Glen-collab/polly-connect/flash_future_polly.docx

Step 1: Create the device in the admin portal

1. Log in as admin at https://polly-connect.com

2. Go to Settings → Devices → Add Device

3. Name it (e.g. "Grandma's Polly")

4. Write down the 6-digit claim code — that's all you need

Step 2: Build the firmware (one time only)

In your ESP-IDF CMD terminal:

cd C:\Users\big_g\Desktop\polly-connect\firmware\polly-waveshare-s3

idf.py build

You only need to build once. Same binary for every device.

Step 3: Flash the device

Plug in the new device, check Device Manager for the COM port, then:

idf.py -p COM5 flash

(Use whatever COM port it shows up on)

Step 4: Give customer the claim code + instructions

Tell them:

1. Go to polly-connect.com → Register

2. Plug in Polly → connect to "Polly-Setup" WiFi on your phone

3. Enter the 6-digit claim code + your home WiFi credentials → hit Connect

4. Go to Settings → Devices on the website → enter the same claim code

5. Done — Polly is yours
