Glen-collab/polly-connect/server/core/database.py

"""
Database module for Polly Connect
"""

import hashlib
import json
import sqlite3
import re
import secrets
from datetime import datetime, timedelta
from typing import Optional, List, Dict


class PollyDB:
    def __init__(self, db_path: str = "polly.db"):
        self.db_path = db_path
        self._conn = None
        if db_path == ":memory:":
            self._conn = sqlite3.connect(":memory:", check_same_thread=False)
        self._init_db()
        self._run_migrations()

    def _get_connection(self):
        if self._conn:
            return self._conn
        return sqlite3.connect(self.db_path)

    def _init_db(self):
        conn = self._get_connection()
        try:
            # Enable WAL mode for better concurrent access
            conn.execute("PRAGMA journal_mode=WAL")

            # ── Original items table ──
            conn.execute("""
                CREATE TABLE IF NOT EXISTS items (
                    id INTEGER PRIMARY KEY AUTOINCREMENT,
                    item TEXT NOT NULL,
                    item_normalized TEXT NOT NULL,
                    location TEXT NOT NULL,
                    location_normalized TEXT NOT NULL,
                    context TEXT,
                    raw_input TEXT,
                    created_at TIMESTAMP DEFAULT CURRENT_TIMESTAMP,
                    updated_at TIMESTAMP DEFAULT CURRENT_TIMESTAMP
                )
            """)
            conn.execute("CREATE INDEX IF NOT EXISTS idx_item_normalized ON items(item_normalized)")
            conn.execute("CREATE INDEX IF NOT EXISTS idx_location_normalized ON items(location_normalized)")

            # ── Device registration ──
            conn.execute("""
                CREATE TABLE IF NOT EXISTS devices (
                    id INTEGER PRIMARY KEY AUTOINCREMENT,
                    device_id TEXT UNIQUE NOT NULL,
                    api_key TEXT,
                    name TEXT,
                    user_id INTEGER REFERENCES user_profiles(id),
                    registered_at TIMESTAMP DEFAULT CURRENT_TIMESTAMP,
                    last_seen TIMESTAMP
                )
            """)

            # ── User profiles ──
            conn.execute("""
                CREATE TABLE IF NOT EXISTS user_profiles (
                    id INTEGER PRIMARY KEY AUTOINCREMENT,
                    name TEXT NOT NULL,
                    familiar_name TEXT,
                    subscription_tier TEXT DEFAULT 'basic',
                    bible_topic_preference TEXT,
                    music_genre_preference TEXT,
                    memory_care_mode INTEGER DEFAULT 0,
                    created_at TIMESTAMP DEFAULT CURRENT_TIMESTAMP,
                    updated_at TIMESTAMP DEFAULT CURRENT_TIMESTAMP
                )
            """)

            # ── Question sessions (Q&A tracking) ──
            conn.execute("""
                CREATE TABLE IF NOT EXISTS question_sessions (
                    id INTEGER PRIMARY KEY AUTOINCREMENT,
                    user_id INTEGER REFERENCES user_profiles(id),
                    question_id TEXT NOT NULL,
                    question_text TEXT NOT NULL,
                    answer_text TEXT,
                    audio_s3_key TEXT,
                    week INTEGER,
                    theme TEXT,
                    answered INTEGER DEFAULT 0,
                    created_at TIMESTAMP DEFAULT CURRENT_TIMESTAMP
                )
            """)

            # ── Free-form stories ──
            conn.execute("""
                CREATE TABLE IF NOT EXISTS stories (
                    id INTEGER PRIMARY KEY AUTOINCREMENT,
                    user_id INTEGER REFERENCES user_profiles(id),
                    transcript TEXT,
                    audio_s3_key TEXT,
                    speaker_name TEXT,
                    chapter TEXT,
                    source TEXT DEFAULT 'voice',
                    duration_seconds REAL,
                    created_at TIMESTAMP DEFAULT CURRENT_TIMESTAMP
                )
            """)

            # ── Medication schedules ──
            conn.execute("""
                CREATE TABLE IF NOT EXISTS medications (
                    id INTEGER PRIMARY KEY AUTOINCREMENT,
                    user_id INTEGER REFERENCES user_profiles(id),
                    name TEXT NOT NULL,
                    dosage TEXT,
                    times TEXT NOT NULL,
                    active_days TEXT DEFAULT '["mon","tue","wed","thu","fri","sat","sun"]',
                    active INTEGER DEFAULT 1,
                    created_at TIMESTAMP DEFAULT CURRENT_TIMESTAMP
                )
            """)

            # ── Medication compliance logs ──
            conn.execute("""
                CREATE TABLE IF NOT EXISTS medication_logs (
                    id INTEGER PRIMARY KEY AUTOINCREMENT,
                    medication_id INTEGER REFERENCES medications(id),
                    status TEXT NOT NULL,
                    reminder_count INTEGER DEFAULT 0,
                    scheduled_time TEXT,
                    responded_at TIMESTAMP,
                    created_at TIMESTAMP DEFAULT CURRENT_TIMESTAMP
                )
            """)

            # ── Bible verses ──
            conn.execute("""
                CREATE TABLE IF NOT EXISTS bible_verses (
                    id INTEGER PRIMARY KEY AUTOINCREMENT,
                    reference TEXT NOT NULL,
                    text TEXT NOT NULL,
                    reflection TEXT,
                    topic TEXT,
                    day_of_year INTEGER
                )
            """)

            # ── Joke history (prevent repeats) ──
            conn.execute("""
                CREATE TABLE IF NOT EXISTS joke_history (
                    id INTEGER PRIMARY KEY AUTOINCREMENT,
                    user_id INTEGER REFERENCES user_profiles(id),
                    joke_id TEXT NOT NULL,
                    told_at TIMESTAMP DEFAULT CURRENT_TIMESTAMP
                )
            """)

            # ── Almanac weather ──
            conn.execute("""
                CREATE TABLE IF NOT EXISTS almanac_weather (
                    id INTEGER PRIMARY KEY AUTOINCREMENT,
                    year INTEGER NOT NULL,
                    week INTEGER NOT NULL,
                    region TEXT DEFAULT 'general',
                    forecast TEXT NOT NULL,
                    details TEXT
                )
            """)

            # ── Family members ──
            conn.execute("""
                CREATE TABLE IF NOT EXISTS family_members (
                    id INTEGER PRIMARY KEY AUTOINCREMENT,
                    name TEXT NOT NULL,
                    name_normalized TEXT NOT NULL,
                    relationship TEXT,
                    primary_user_id INTEGER REFERENCES user_profiles(id),
                    visit_count INTEGER DEFAULT 1,
                    first_seen TIMESTAMP DEFAULT CURRENT_TIMESTAMP,
                    last_seen TIMESTAMP DEFAULT CURRENT_TIMESTAMP
                )
            """)
            conn.execute("CREATE INDEX IF NOT EXISTS idx_family_name ON family_members(name_normalized)")

            # ── Story tags ──
            conn.execute("""
                CREATE TABLE IF NOT EXISTS story_tags (
                    id INTEGER PRIMARY KEY AUTOINCREMENT,
                    story_id INTEGER REFERENCES stories(id),
                    tag_type TEXT NOT NULL,
                    tag_value TEXT NOT NULL
                )
            """)
            conn.execute("CREATE INDEX IF NOT EXISTS idx_story_tags ON story_tags(story_id)")

            # ── Structured memories (narrative-enriched) ──
            conn.execute("""
                CREATE TABLE IF NOT EXISTS memories (
                    id INTEGER PRIMARY KEY AUTOINCREMENT,
                    story_id INTEGER REFERENCES stories(id),
                    speaker TEXT,
                    bucket TEXT DEFAULT 'ordinary_world',
                    life_phase TEXT DEFAULT 'unknown',
                    text_summary TEXT,
                    text TEXT,
                    people TEXT DEFAULT '[]',
                    locations TEXT DEFAULT '[]',
                    emotions TEXT DEFAULT '[]',
                    fingerprint TEXT,
                    verification_status TEXT DEFAULT 'unverified',
                    verified_by TEXT,
                    verified_at TIMESTAMP,
                    created_at TIMESTAMP DEFAULT CURRENT_TIMESTAMP
                )
            """)
            conn.execute("CREATE INDEX IF NOT EXISTS idx_memories_speaker ON memories(speaker)")
            conn.execute("CREATE INDEX IF NOT EXISTS idx_memories_bucket ON memories(bucket)")
            conn.execute("CREATE INDEX IF NOT EXISTS idx_memories_verification ON memories(verification_status)")

            # ── Memory verifications (audit trail) ──
            conn.execute("""
                CREATE TABLE IF NOT EXISTS memory_verifications (
                    id INTEGER PRIMARY KEY AUTOINCREMENT,
                    memory_id INTEGER REFERENCES memories(id),
                    verifier_name TEXT NOT NULL,
                    verifier_relationship TEXT,
                    status TEXT NOT NULL,
                    notes TEXT,
                    created_at TIMESTAMP DEFAULT CURRENT_TIMESTAMP
                )
            """)

            # ── Chapter drafts ──
            conn.execute("""
                CREATE TABLE IF NOT EXISTS chapter_drafts (
                    id INTEGER PRIMARY KEY AUTOINCREMENT,
                    chapter_number INTEGER,
                    title TEXT,
                    bucket TEXT,
                    life_phase TEXT,
                    memory_ids TEXT DEFAULT '[]',
                    content TEXT,
                    status TEXT DEFAULT 'draft',
                    created_at TIMESTAMP DEFAULT CURRENT_TIMESTAMP,
                    updated_at TIMESTAMP DEFAULT CURRENT_TIMESTAMP
                )
            """)

            # ── Session tracking ──
            conn.execute("""
                CREATE TABLE IF NOT EXISTS sessions (
                    id INTEGER PRIMARY KEY AUTOINCREMENT,
                    device_id TEXT,
                    user_id INTEGER REFERENCES user_profiles(id),
                    jokes_told INTEGER DEFAULT 0,
                    questions_asked INTEGER DEFAULT 0,
                    stories_recorded INTEGER DEFAULT 0,
                    duration_seconds REAL,
                    started_at TIMESTAMP DEFAULT CURRENT_TIMESTAMP,
                    ended_at TIMESTAMP
                )
            """)

            # ── Photos ──
            conn.execute("""
                CREATE TABLE IF NOT EXISTS photos (
                    id INTEGER PRIMARY KEY AUTOINCREMENT,
                    user_id INTEGER REFERENCES user_profiles(id),
                    filename TEXT NOT NULL,
                    original_name TEXT,
                    caption TEXT,
                    date_taken TEXT,
                    tags TEXT DEFAULT '[]',
                    story_id INTEGER REFERENCES stories(id),
                    uploaded_by TEXT,
                    created_at TIMESTAMP DEFAULT CURRENT_TIMESTAMP
                )
            """)

            # ── Family message board ──
            conn.execute("""
                CREATE TABLE IF NOT EXISTS family_messages (
                    id INTEGER PRIMARY KEY AUTOINCREMENT,
                    tenant_id INTEGER,
                    from_name TEXT NOT NULL,
                    to_name TEXT,
                    message TEXT NOT NULL,
                    created_at TIMESTAMP DEFAULT CURRENT_TIMESTAMP,
                    expires_at TIMESTAMP,
                    read INTEGER DEFAULT 0
                )
            """)
            conn.execute("CREATE INDEX IF NOT EXISTS idx_family_messages_tenant ON family_messages(tenant_id)")

            # ── family_messages migrations ──
            msg_cols = {row[1] for row in conn.execute("PRAGMA table_info(family_messages)").fetchall()}
            if "device_id" not in msg_cols:
                conn.execute("ALTER TABLE family_messages ADD COLUMN device_id TEXT")
            if "audio_filename" not in msg_cols:
                conn.execute("ALTER TABLE family_messages ADD COLUMN audio_filename TEXT")

            # ── Connected families (cross-tenant message board access) ──
            conn.execute("""
                CREATE TABLE IF NOT EXISTS connected_families (
                    id INTEGER PRIMARY KEY AUTOINCREMENT,
                    tenant_id INTEGER NOT NULL,
                    connected_tenant_id INTEGER NOT NULL,
                    connected_tenant_name TEXT NOT NULL,
                    nickname TEXT,
                    status TEXT DEFAULT 'accepted',
                    created_at TIMESTAMP DEFAULT CURRENT_TIMESTAMP,
                    UNIQUE(tenant_id, connected_tenant_id)
                )
            """)
            # Migration: add status column if missing
            cf_cols = {row[1] for row in conn.execute("PRAGMA table_info(connected_families)").fetchall()}
            if "status" not in cf_cols:
                conn.execute("ALTER TABLE connected_families ADD COLUMN status TEXT DEFAULT 'accepted'")
            if "share_tree" not in cf_cols:
                conn.execute("ALTER TABLE connected_families ADD COLUMN share_tree INTEGER DEFAULT 0")
            if "tree_requested" not in cf_cols:
                conn.execute("ALTER TABLE connected_families ADD COLUMN tree_requested INTEGER DEFAULT 0")
            if "last_wall_visit" not in cf_cols:
                conn.execute("ALTER TABLE connected_families ADD COLUMN last_wall_visit TIMESTAMP")

            # ── Shared Wall ──
            conn.execute("""
                CREATE TABLE IF NOT EXISTS shared_wall_items (
                    id INTEGER PRIMARY KEY AUTOINCREMENT,
                    from_tenant_id INTEGER NOT NULL,
                    to_tenant_id INTEGER NOT NULL,
                    content_type TEXT NOT NULL,
                    content_id INTEGER,
                    caption TEXT,
                    created_at TIMESTAMP DEFAULT CURRENT_TIMESTAMP
                )
            """)
            conn.execute("CREATE INDEX IF NOT EXISTS idx_shared_wall_pair ON shared_wall_items(from_tenant_id, to_tenant_id)")

            conn.execute("""
                CREATE TABLE IF NOT EXISTS wall_comments (
                    id INTEGER PRIMARY KEY AUTOINCREMENT,
                    wall_item_id INTEGER NOT NULL,
                    tenant_id INTEGER NOT NULL,
                    tenant_name TEXT,
                    comment TEXT,
                    audio_filename TEXT,
                    created_at TIMESTAMP DEFAULT CURRENT_TIMESTAMP
                )
            """)

            conn.execute("""
                CREATE TABLE IF NOT EXISTS wall_reactions (
                    id INTEGER PRIMARY KEY AUTOINCREMENT,
                    wall_item_id INTEGER NOT NULL,
                    tenant_id INTEGER NOT NULL,
                    reaction TEXT NOT NULL,
                    created_at TIMESTAMP DEFAULT CURRENT_TIMESTAMP,
                    UNIQUE(wall_item_id, tenant_id)
                )
            """)

            # ── Aviary (community feed) tables ──

            conn.execute("""
                CREATE TABLE IF NOT EXISTS aviary_posts (
                    id INTEGER PRIMARY KEY AUTOINCREMENT,
                    tenant_id INTEGER NOT NULL,
                    author_name TEXT NOT NULL,
                    content_type TEXT NOT NULL DEFAULT 'text',
                    content TEXT,
                    photo_filename TEXT,
                    audio_filename TEXT,
                    created_at TIMESTAMP DEFAULT CURRENT_TIMESTAMP
                )
            """)
            conn.execute("CREATE INDEX IF NOT EXISTS idx_aviary_tenant ON aviary_posts(tenant_id)")

            conn.execute("""
                CREATE TABLE IF NOT EXISTS aviary_reactions (
                    id INTEGER PRIMARY KEY AUTOINCREMENT,
                    post_id INTEGER NOT NULL,
                    tenant_id INTEGER NOT NULL,
                    reactor_name TEXT,
                    reaction TEXT NOT NULL,
                    created_at TIMESTAMP DEFAULT CURRENT_TIMESTAMP,
                    UNIQUE(post_id, tenant_id)
                )
            """)

            conn.execute("""
                CREATE TABLE IF NOT EXISTS aviary_comments (
                    id INTEGER PRIMARY KEY AUTOINCREMENT,
                    post_id INTEGER NOT NULL,
                    tenant_id INTEGER NOT NULL,
                    author_name TEXT NOT NULL,
                    comment TEXT,
                    audio_filename TEXT,
                    created_at TIMESTAMP DEFAULT CURRENT_TIMESTAMP
                )
            """)

            # ── Chatter Groups ──

            conn.execute("""
                CREATE TABLE IF NOT EXISTS chatter_groups (
                    id INTEGER PRIMARY KEY AUTOINCREMENT,
                    name TEXT NOT NULL,
                    creator_tenant_id INTEGER NOT NULL,
                    created_at TIMESTAMP DEFAULT CURRENT_TIMESTAMP
                )
            """)

            conn.execute("""
                CREATE TABLE IF NOT EXISTS chatter_group_members (
                    id INTEGER PRIMARY KEY AUTOINCREMENT,
                    group_id INTEGER NOT NULL,
                    tenant_id INTEGER NOT NULL,
                    role TEXT NOT NULL DEFAULT 'member',
                    joined_at TIMESTAMP DEFAULT CURRENT_TIMESTAMP,
                    last_read_at TIMESTAMP DEFAULT '2000-01-01',
                    UNIQUE(group_id, tenant_id),
                    FOREIGN KEY (group_id) REFERENCES chatter_groups(id)
                )
            """)

            # Migration: add group_id to aviary_posts
            ap_cols = {row[1] for row in conn.execute("PRAGMA table_info(aviary_posts)").fetchall()}
            if "group_id" not in ap_cols:
                conn.execute("ALTER TABLE aviary_posts ADD COLUMN group_id INTEGER")
                conn.execute("CREATE INDEX IF NOT EXISTS idx_aviary_group ON aviary_posts(group_id)")

            # ── Multi-tenant tables ──

            conn.execute("""
                CREATE TABLE IF NOT EXISTS tenants (
                    id INTEGER PRIMARY KEY AUTOINCREMENT,
                    name TEXT NOT NULL,
                    created_at TIMESTAMP DEFAULT CURRENT_TIMESTAMP,
                    updated_at TIMESTAMP DEFAULT CURRENT_TIMESTAMP
                )
            """)

            conn.execute("""
                CREATE TABLE IF NOT EXISTS accounts (
                    id INTEGER PRIMARY KEY AUTOINCREMENT,
                    email TEXT UNIQUE NOT NULL,
                    password_hash TEXT NOT NULL,
                    name TEXT NOT NULL,
                    tenant_id INTEGER REFERENCES tenants(id),
                    role TEXT DEFAULT 'caretaker',
                    created_at TIMESTAMP DEFAULT CURRENT_TIMESTAMP,
                    last_login TIMESTAMP
                )
            """)
            conn.execute("CREATE INDEX IF NOT EXISTS idx_accounts_tenant ON accounts(tenant_id)")

            conn.execute("""
                CREATE TABLE IF NOT EXISTS web_sessions (
                    id TEXT PRIMARY KEY,
                    account_id INTEGER REFERENCES accounts(id),
                    tenant_id INTEGER REFERENCES tenants(id),
                    created_at TIMESTAMP DEFAULT CURRENT_TIMESTAMP,
                    expires_at TIMESTAMP,
                    last_active TIMESTAMP DEFAULT CURRENT_TIMESTAMP
                )
            """)
            conn.execute("CREATE INDEX IF NOT EXISTS idx_web_sessions_account ON web_sessions(account_id)")

            # ── Firmware versions (OTA updates) ──
            conn.execute("""
                CREATE TABLE IF NOT EXISTS firmware_versions (
                    id INTEGER PRIMARY KEY AUTOINCREMENT,
                    variant TEXT NOT NULL,
                    version TEXT NOT NULL,
                    filename TEXT NOT NULL,
                    file_size INTEGER,
                    file_hash TEXT,
                    release_notes TEXT,
                    is_active INTEGER DEFAULT 0,
                    uploaded_at TIMESTAMP DEFAULT CURRENT_TIMESTAMP
                )
            """)

            # ── Narrative log (track which stories were read back) ──
            conn.execute("""
                CREATE TABLE IF NOT EXISTS narrative_log (
                    id INTEGER PRIMARY KEY AUTOINCREMENT,
                    tenant_id INTEGER,
                    story_id INTEGER REFERENCES stories(id),
                    query TEXT,
                    created_at TIMESTAMP DEFAULT CURRENT_TIMESTAMP
                )
            """)
            conn.execute("CREATE INDEX IF NOT EXISTS idx_narrative_log_tenant ON narrative_log(tenant_id, created_at)")
            conn.execute("CREATE INDEX IF NOT EXISTS idx_narrative_log_story ON narrative_log(story_id, created_at)")

            # ── Story narratives (cached GPT narratives for replay) ──
            conn.execute("""
                CREATE TABLE IF NOT EXISTS story_narratives (
                    id INTEGER PRIMARY KEY AUTOINCREMENT,
                    tenant_id INTEGER,
                    narrative TEXT NOT NULL,
                    attribution TEXT,
                    story_ids TEXT,
                    query TEXT,
                    status TEXT DEFAULT 'draft',
                    created_at TIMESTAMP DEFAULT CURRENT_TIMESTAMP
                )
            """)

            # ── Device events (admin telemetry) ──
            conn.execute("""
                CREATE TABLE IF NOT EXISTS device_events (
                    id INTEGER PRIMARY KEY AUTOINCREMENT,
                    device_id TEXT NOT NULL,
                    tenant_id INTEGER,
                    event_type TEXT NOT NULL,
                    intent TEXT,
                    success INTEGER DEFAULT 1,
                    detail TEXT,
                    created_at TIMESTAMP DEFAULT CURRENT_TIMESTAMP
                )
            """)
            conn.execute("CREATE INDEX IF NOT EXISTS idx_device_events_device_time ON device_events(device_id, created_at)")
            conn.execute("CREATE INDEX IF NOT EXISTS idx_device_events_type_time ON device_events(event_type, created_at)")

            conn.commit()
        finally:
            if not self._conn:
                conn.close()

    def _run_migrations(self):
        """Add columns to existing tables (safe to run repeatedly)."""
        conn = self._get_connection()
        try:
            # Get existing columns for user_profiles
            cols = {row[1] for row in conn.execute("PRAGMA table_info(user_profiles)").fetchall()}
            migrations = {
                "owner_email": "ALTER TABLE user_profiles ADD COLUMN owner_email TEXT",
                "caretaker_name": "ALTER TABLE user_profiles ADD COLUMN caretaker_name TEXT",
                "caretaker_email": "ALTER TABLE user_profiles ADD COLUMN caretaker_email TEXT",
                "setup_complete": "ALTER TABLE user_profiles ADD COLUMN setup_complete INTEGER DEFAULT 0",
                "squawk_interval": "ALTER TABLE user_profiles ADD COLUMN squawk_interval INTEGER DEFAULT 10",
                "chatter_interval": "ALTER TABLE user_profiles ADD COLUMN chatter_interval INTEGER DEFAULT 45",
                "squawk_snoozed_until": "ALTER TABLE user_profiles ADD COLUMN squawk_snoozed_until TIMESTAMP",
                "quiet_hours_start": "ALTER TABLE user_profiles ADD COLUMN quiet_hours_start INTEGER DEFAULT 21",
                "quiet_hours_end": "ALTER TABLE user_profiles ADD COLUMN quiet_hours_end INTEGER DEFAULT 7",
                "location_city": "ALTER TABLE user_profiles ADD COLUMN location_city TEXT",
                "location_lat": "ALTER TABLE user_profiles ADD COLUMN location_lat REAL",
                "location_lon": "ALTER TABLE user_profiles ADD COLUMN location_lon REAL",
                "squawk_volume": "ALTER TABLE user_profiles ADD COLUMN squawk_volume INTEGER DEFAULT 30",
                "rms_threshold": "ALTER TABLE user_profiles ADD COLUMN rms_threshold INTEGER DEFAULT 200",
                "voice_volume": "ALTER TABLE user_profiles ADD COLUMN voice_volume INTEGER DEFAULT 100",
                "blessing_volume": "ALTER TABLE user_profiles ADD COLUMN blessing_volume INTEGER DEFAULT 80",
                "kid_mode": "ALTER TABLE user_profiles ADD COLUMN kid_mode INTEGER DEFAULT 0",
                "nostalgia_profile": "ALTER TABLE user_profiles ADD COLUMN nostalgia_profile TEXT",
                "hometown": "ALTER TABLE user_profiles ADD COLUMN hometown TEXT",
                "birth_year": "ALTER TABLE user_profiles ADD COLUMN birth_year INTEGER",
                "squawk_quiet_override": "ALTER TABLE user_profiles ADD COLUMN squawk_quiet_override INTEGER DEFAULT 0",
                "book_page_count": "ALTER TABLE user_profiles ADD COLUMN book_page_count INTEGER",
                "book_cover_config": "ALTER TABLE user_profiles ADD COLUMN book_cover_config TEXT",
                "last_aviary_visit": "ALTER TABLE user_profiles ADD COLUMN last_aviary_visit TIMESTAMP",
            }
            for col, sql in migrations.items():
                if col not in cols:
                    conn.execute(sql)

            # Get existing columns for stories
            cols = {row[1] for row in conn.execute("PRAGMA table_info(stories)").fetchall()}
            migrations = {
                "verified": "ALTER TABLE stories ADD COLUMN verified INTEGER DEFAULT 0",
                "verified_by": "ALTER TABLE stories ADD COLUMN verified_by TEXT",
                "verified_at": "ALTER TABLE stories ADD COLUMN verified_at TIMESTAMP",
                "corrected_transcript": "ALTER TABLE stories ADD COLUMN corrected_transcript TEXT",
                "question_text": "ALTER TABLE stories ADD COLUMN question_text TEXT",
                "photo_id": "ALTER TABLE stories ADD COLUMN photo_id INTEGER REFERENCES photos(id)",
                "qr_in_book": "ALTER TABLE stories ADD COLUMN qr_in_book INTEGER DEFAULT 1",
                "photo_in_book": "ALTER TABLE stories ADD COLUMN photo_in_book INTEGER DEFAULT 1",
                "private": "ALTER TABLE stories ADD COLUMN private INTEGER DEFAULT 0",
            }
            for col, sql in migrations.items():
                if col not in cols:
                    conn.execute(sql)

            # ── Multi-tenant migrations: add tenant_id to all data tables ──
            tenant_tables = [
                "items", "stories", "question_sessions", "medications",
                "medication_logs", "joke_history", "family_members", "memories",
                "memory_verifications", "chapter_drafts", "sessions", "photos",
                "story_tags", "user_profiles", "devices", "family_messages",
            ]
            for table in tenant_tables:
                cols = {row[1] for row in conn.execute(f"PRAGMA table_info({table})").fetchall()}
                if "tenant_id" not in cols:
                    conn.execute(f"ALTER TABLE {table} ADD COLUMN tenant_id INTEGER")

            # Add in_book to photos
            cols = {row[1] for row in conn.execute("PRAGMA table_info(photos)").fetchall()}
            if "in_book" not in cols:
                conn.execute("ALTER TABLE photos ADD COLUMN in_book INTEGER DEFAULT 1")
            if "wall_only" not in cols:
                conn.execute("ALTER TABLE photos ADD COLUMN wall_only INTEGER DEFAULT 0")

            # Add is_admin and terms_accepted_at to accounts
            cols = {row[1] for row in conn.execute("PRAGMA table_info(accounts)").fetchall()}
            if "is_admin" not in cols:
                conn.execute("ALTER TABLE accounts ADD COLUMN is_admin INTEGER DEFAULT 0")
                # First account is always admin (manufacturer)
                conn.execute("UPDATE accounts SET is_admin = 1 WHERE id = 1")
            if "terms_accepted_at" not in cols:
                conn.execute("ALTER TABLE accounts ADD COLUMN terms_accepted_at TIMESTAMP")

            # Add api_key_hash and firmware info to devices
            cols = {row[1] for row in conn.execute("PRAGMA table_info(devices)").fetchall()}
            if "api_key_hash" not in cols:
                conn.execute("ALTER TABLE devices ADD COLUMN api_key_hash TEXT")
            if "fw_version" not in cols:
                conn.execute("ALTER TABLE devices ADD COLUMN fw_version TEXT")
            if "fw_variant" not in cols:
                conn.execute("ALTER TABLE devices ADD COLUMN fw_variant TEXT")
            if "claim_code" not in cols:
                conn.execute("ALTER TABLE devices ADD COLUMN claim_code TEXT")
            if "claimed_at" not in cols:
                conn.execute("ALTER TABLE devices ADD COLUMN claimed_at TIMESTAMP")

            # Per-device settings (NULL = inherit from tenant user_profiles)
            device_settings_migrations = {
                "dev_quiet_hours_start": "ALTER TABLE devices ADD COLUMN dev_quiet_hours_start INTEGER",
                "dev_quiet_hours_end": "ALTER TABLE devices ADD COLUMN dev_quiet_hours_end INTEGER",
                "dev_squawk_interval": "ALTER TABLE devices ADD COLUMN dev_squawk_interval INTEGER",
                "dev_chatter_interval": "ALTER TABLE devices ADD COLUMN dev_chatter_interval INTEGER",
                "dev_squawk_volume": "ALTER TABLE devices ADD COLUMN dev_squawk_volume INTEGER",
                "dev_snoozed_until": "ALTER TABLE devices ADD COLUMN dev_snoozed_until TIMESTAMP",
                "dev_quiet_override": "ALTER TABLE devices ADD COLUMN dev_quiet_override INTEGER",
                "dev_message_nag": "ALTER TABLE devices ADD COLUMN dev_message_nag INTEGER",
                "dev_kid_mode": "ALTER TABLE devices ADD COLUMN dev_kid_mode INTEGER",
            }
            for col, sql in device_settings_migrations.items():
                if col not in cols:
                    conn.execute(sql)

            # Create default tenant #1 and backfill
            conn.execute("INSERT OR IGNORE INTO tenants (id, name) VALUES (1, 'Default')")
            for table in tenant_tables:
                conn.execute(f"UPDATE {table} SET tenant_id = 1 WHERE tenant_id IS NULL")

            # ── Family access code migrations ──
            # Add family_code columns to tenants
            cols = {row[1] for row in conn.execute("PRAGMA table_info(tenants)").fetchall()}
            if "family_code" not in cols:
                conn.execute("ALTER TABLE tenants ADD COLUMN family_code TEXT")
            if "family_code_created_at" not in cols:
                conn.execute("ALTER TABLE tenants ADD COLUMN family_code_created_at TIMESTAMP")

            # ── Medications device_id column ──
            cols = {row[1] for row in conn.execute("PRAGMA table_info(medications)").fetchall()}
            if "device_id" not in cols:
                conn.execute("ALTER TABLE medications ADD COLUMN device_id TEXT")

            # ── Items prep column ──
            cols = {row[1] for row in conn.execute("PRAGMA table_info(items)").fetchall()}
            if "prep" not in cols:
                conn.execute("ALTER TABLE items ADD COLUMN prep TEXT DEFAULT 'on'")

            # ── Family tree migrations ──
            cols = {row[1] for row in conn.execute("PRAGMA table_info(family_members)").fetchall()}
            fm_migrations = {
                "parent_member_id": "ALTER TABLE family_members ADD COLUMN parent_member_id INTEGER REFERENCES family_members(id)",
                "relation_to_owner": "ALTER TABLE family_members ADD COLUMN relation_to_owner TEXT",
                "generation": "ALTER TABLE family_members ADD COLUMN generation INTEGER DEFAULT 0",
            }
            for col, sql in fm_migrations.items():
                if col not in cols:
                    conn.execute(sql)

            # Add extended info to family_members
            cols = {row[1] for row in conn.execute("PRAGMA table_info(family_members)").fetchall()}
            fm_ext = {
                "deceased": "ALTER TABLE family_members ADD COLUMN deceased INTEGER DEFAULT 0",
                "spouse_name": "ALTER TABLE family_members ADD COLUMN spouse_name TEXT",
                "bio": "ALTER TABLE family_members ADD COLUMN bio TEXT",
                "added_by": "ALTER TABLE family_members ADD COLUMN added_by TEXT",
                "birth_year": "ALTER TABLE family_members ADD COLUMN birth_year INTEGER",
                "deceased_year": "ALTER TABLE family_members ADD COLUMN deceased_year INTEGER",
                "access_code": "ALTER TABLE family_members ADD COLUMN access_code TEXT",
                "code_created_at": "ALTER TABLE family_members ADD COLUMN code_created_at TIMESTAMP",
                "is_minor": "ALTER TABLE family_members ADD COLUMN is_minor INTEGER DEFAULT 0",
                "email": "ALTER TABLE family_members ADD COLUMN email TEXT",
            }
            for col, sql in fm_ext.items():
                if col not in cols:
                    conn.execute(sql)

            # Add family_member_id + onboarding columns to web_sessions
            cols = {row[1] for row in conn.execute("PRAGMA table_info(web_sessions)").fetchall()}
            ws_migrations = {
                "family_member_id": "ALTER TABLE web_sessions ADD COLUMN family_member_id INTEGER",
                "onboarding_complete": "ALTER TABLE web_sessions ADD COLUMN onboarding_complete INTEGER DEFAULT 0",
                "invitation_id": "ALTER TABLE web_sessions ADD COLUMN invitation_id INTEGER",
                "last_onboarding_step": "ALTER TABLE web_sessions ADD COLUMN last_onboarding_step INTEGER DEFAULT 1",
            }
            for col, sql in ws_migrations.items():
                if col not in cols:
                    conn.execute(sql)

            # Family invitations table
            conn.execute("""
                CREATE TABLE IF NOT EXISTS family_invitations (
                    id INTEGER PRIMARY KEY AUTOINCREMENT,
                    tenant_id INTEGER NOT NULL,
                    family_member_id INTEGER,
                    inviter_name TEXT NOT NULL,
                    invitee_name TEXT NOT NULL,
                    invitee_email TEXT NOT NULL,
                    voice_message_filename TEXT,
                    family_code TEXT NOT NULL,
                    status TEXT DEFAULT 'sent',
                    sent_at TIMESTAMP DEFAULT CURRENT_TIMESTAMP,
                    visited_at TIMESTAMP,
                    onboarded_at TIMESTAMP,
                    converted_at TIMESTAMP,
                    converted_tenant_id INTEGER,
                    feedback_rating INTEGER,
                    feedback_note TEXT
                )
            """)

            # Add timeline columns to memories
            cols = {row[1] for row in conn.execute("PRAGMA table_info(memories)").fetchall()}
            mem_migrations = {
                "estimated_year": "ALTER TABLE memories ADD COLUMN estimated_year INTEGER",
                "owner_age": "ALTER TABLE memories ADD COLUMN owner_age INTEGER",
                "year_confidence": "ALTER TABLE memories ADD COLUMN year_confidence TEXT DEFAULT 'none'",
                # ── Legacy Funnel: every surface (story/photo/chatter/wall) feeds memories ──
                "source": "ALTER TABLE memories ADD COLUMN source TEXT DEFAULT 'story'",
                "source_ref": "ALTER TABLE memories ADD COLUMN source_ref INTEGER",
                "include_in_book": "ALTER TABLE memories ADD COLUMN include_in_book INTEGER DEFAULT 1",
                "is_quote": "ALTER TABLE memories ADD COLUMN is_quote INTEGER DEFAULT 0",
                "story_value": "ALTER TABLE memories ADD COLUMN story_value REAL",
                # The owner dated or moved this story themselves: the AI
                # sorter never overrides their placement
                "placed_by_user": "ALTER TABLE memories ADD COLUMN placed_by_user INTEGER DEFAULT 0",
                # "Move to this chapter": pinned to a written chapter's draft
                "pinned_draft_id": "ALTER TABLE memories ADD COLUMN pinned_draft_id INTEGER",
            }
            for col, sql in mem_migrations.items():
                if col not in cols:
                    conn.execute(sql)

            # Add chapter continuity columns to chapter_drafts
            cols = {row[1] for row in conn.execute("PRAGMA table_info(chapter_drafts)").fetchall()}
            cd_migrations = {
                "summary": "ALTER TABLE chapter_drafts ADD COLUMN summary TEXT",
                "needs_refresh": "ALTER TABLE chapter_drafts ADD COLUMN needs_refresh INTEGER DEFAULT 0",
                # Memories the coverage check found absent from the prose —
                # the PDF prints these verbatim after the chapter.
                "missing_memory_ids": "ALTER TABLE chapter_drafts ADD COLUMN missing_memory_ids TEXT DEFAULT '[]'",
                # Owner edited the prose by hand: never auto-rewrite it
                "hand_edited": "ALTER TABLE chapter_drafts ADD COLUMN hand_edited INTEGER DEFAULT 0",
                # The version a rewrite replaced, so a rewrite is never a loss
                "previous_content": "ALTER TABLE chapter_drafts ADD COLUMN previous_content TEXT",
                # {memory_id: "bucket/life_phase"} when the chapter was written;
                # a story whose placement changes since then moves out
                "placements": "ALTER TABLE chapter_drafts ADD COLUMN placements TEXT",
            }
            for col, sql in cd_migrations.items():
                if col not in cols:
                    conn.execute(sql)
                    if col == "hand_edited":
                        # Drafts saved after generation were edited by hand
                        conn.execute("UPDATE chapter_drafts SET hand_edited = 1 "
                                     "WHERE updated_at IS NOT NULL AND updated_at > created_at")

            # Prayer requests table
            conn.execute("""
                CREATE TABLE IF NOT EXISTS prayer_requests (
                    id INTEGER PRIMARY KEY AUTOINCREMENT,
                    tenant_id INTEGER,
                    name TEXT NOT NULL,
                    request TEXT,
                    active INTEGER DEFAULT 1,
                    created_at TIMESTAMP DEFAULT CURRENT_TIMESTAMP
                )
            """)

            # Pronunciation guide table
            conn.execute("""
                CREATE TABLE IF NOT EXISTS pronunciations (
                    id INTEGER PRIMARY KEY AUTOINCREMENT,
                    tenant_id INTEGER,
                    word TEXT NOT NULL,
                    phonetic TEXT NOT NULL,
                    created_at TIMESTAMP DEFAULT CURRENT_TIMESTAMP
                )
            """)

            # Nostalgia snippets table
            conn.execute("""
                CREATE TABLE IF NOT EXISTS nostalgia_snippets (
                    id INTEGER PRIMARY KEY AUTOINCREMENT,
                    tenant_id INTEGER,
                    category TEXT NOT NULL,
                    variation_number INTEGER NOT NULL,
                    text TEXT NOT NULL,
                    last_used TIMESTAMP,
                    created_at TIMESTAMP DEFAULT CURRENT_TIMESTAMP
                )
            """)
            conn.execute("CREATE INDEX IF NOT EXISTS idx_nostalgia_tenant ON nostalgia_snippets(tenant_id)")

            # Add original_text to nostalgia_snippets for tracking edits
            cols = {row[1] for row in conn.execute("PRAGMA table_info(nostalgia_snippets)").fetchall()}
            if "original_text" not in cols:
                conn.execute("ALTER TABLE nostalgia_snippets ADD COLUMN original_text TEXT")

            # Deleted nostalgia snippets log (so GPT avoids these topics)
            conn.execute("""
                CREATE TABLE IF NOT EXISTS nostalgia_deleted (
                    id INTEGER PRIMARY KEY AUTOINCREMENT,
                    tenant_id INTEGER,
                    category TEXT,
                    text TEXT NOT NULL,
                    deleted_at TIMESTAMP DEFAULT CURRENT_TIMESTAMP
                )
            """)

            # Song briefs table (chapter-to-song pipeline)
            conn.execute("""
                CREATE TABLE IF NOT EXISTS song_briefs (
                    id INTEGER PRIMARY KEY AUTOINCREMENT,
                    tenant_id INTEGER,
                    chapter_number INTEGER,
                    chapter_title TEXT,
                    song_title TEXT,
                    genre TEXT,
                    jungian_stage TEXT,
                    lyrics_json TEXT,
                    style_prompt TEXT,
                    essence_json TEXT,
                    audio_filename TEXT,
                    created_at TIMESTAMP DEFAULT CURRENT_TIMESTAMP
                )
            """)

            # Prayer recordings table (voice prayers, blessings, grace)
            conn.execute("""
                CREATE TABLE IF NOT EXISTS prayer_recordings (
                    id INTEGER PRIMARY KEY AUTOINCREMENT,
                    tenant_id INTEGER,
                    speaker_name TEXT,
                    category TEXT NOT NULL DEFAULT 'general',
                    title TEXT,
                    audio_filename TEXT NOT NULL,
                    transcript TEXT,
                    schedule_time TEXT,
                    schedule_days TEXT DEFAULT '0,1,2,3,4,5,6',
                    active INTEGER DEFAULT 1,
                    play_count INTEGER DEFAULT 0,
                    last_played TIMESTAMP,
                    created_at TIMESTAMP DEFAULT CURRENT_TIMESTAMP
                )
            """)

            # Add family_name and role columns to web_sessions
            cols = {row[1] for row in conn.execute("PRAGMA table_info(web_sessions)").fetchall()}
            if "family_name" not in cols:
                conn.execute("ALTER TABLE web_sessions ADD COLUMN family_name TEXT")
            if "role" not in cols:
                conn.execute("ALTER TABLE web_sessions ADD COLUMN role TEXT")

            # ── Subscription / Stripe migrations ──
            cols = {row[1] for row in conn.execute("PRAGMA table_info(tenants)").fetchall()}
            sub_migrations = {
                "subscription_tier": "ALTER TABLE tenants ADD COLUMN subscription_tier TEXT DEFAULT 'trial'",
                "subscription_status": "ALTER TABLE tenants ADD COLUMN subscription_status TEXT DEFAULT 'active'",
                "stripe_customer_id": "ALTER TABLE tenants ADD COLUMN stripe_customer_id TEXT",
                "stripe_subscription_id": "ALTER TABLE tenants ADD COLUMN stripe_subscription_id TEXT",
                "trial_ends_at": "ALTER TABLE tenants ADD COLUMN trial_ends_at TIMESTAMP",
                # One-time "Buy the Book" unlock (separate from monthly tier)
                "book_purchased": "ALTER TABLE tenants ADD COLUMN book_purchased INTEGER DEFAULT 0",
            }
            for col, sql in sub_migrations.items():
                if col not in cols:
                    conn.execute(sql)

            # Set trial_ends_at for existing tenants that don't have it yet
            # (30 days from now for existing users, generous grace period)
            conn.execute("""
                UPDATE tenants SET trial_ends_at = datetime('now', '+30 days')
                WHERE trial_ends_at IS NULL AND subscription_tier IS NULL AND id > 1
            """)
            # Tenant 1 (admin) gets legacy tier
            conn.execute("""
                UPDATE tenants SET subscription_tier = 'legacy', subscription_status = 'active'
                WHERE id = 1 AND (subscription_tier IS NULL OR subscription_tier = 'trial')
            """)

            # Photo index table (Memory module — photo-based item indexing)
            conn.execute("""
                CREATE TABLE IF NOT EXISTS photo_indexes (
                    id INTEGER PRIMARY KEY AUTOINCREMENT,
                    tenant_id INTEGER,
                    filename TEXT NOT NULL,
                    location TEXT NOT NULL,
                    description TEXT,
                    item_count INTEGER DEFAULT 0,
                    created_at TIMESTAMP DEFAULT CURRENT_TIMESTAMP
                )
            """)

            # Add recorded_by_member_id to stories (tracks which family member recorded)
            story_cols = {row[1] for row in conn.execute("PRAGMA table_info(stories)").fetchall()}
            if "recorded_by_member_id" not in story_cols:
                conn.execute("ALTER TABLE stories ADD COLUMN recorded_by_member_id INTEGER")

            # Security questions for code recovery
            conn.execute("""
                CREATE TABLE IF NOT EXISTS security_questions (
                    id INTEGER PRIMARY KEY AUTOINCREMENT,
                    tenant_id INTEGER NOT NULL,
                    question TEXT NOT NULL,
                    answer_hash TEXT NOT NULL,
                    created_at TIMESTAMP DEFAULT CURRENT_TIMESTAMP
                )
            """)

            conn.commit()
        finally:
            if not self._conn:
                conn.close()

    @staticmethod
    def _normalize(text: str) -> str:
        if not text:
            return ""
        text = text.lower().strip()
        text = re.sub(r'\b(the|a|an|my|that|this)\b', '', text)
        text = re.sub(r'\s+', ' ', text).strip()
        return text

    # ── Tenant management ──

    def create_tenant(self, name: str) -> int:
        conn = self._get_connection()
        try:
            cursor = conn.execute(
                "INSERT INTO tenants (name) VALUES (?)", (name,)
            )
            conn.commit()
            return cursor.lastrowid
        finally:
            if not self._conn:
                conn.close()

    def get_tenant(self, tenant_id: int) -> Optional[Dict]:
        conn = self._get_connection()
        try:
            conn.row_factory = sqlite3.Row
            result = conn.execute(
                "SELECT * FROM tenants WHERE id = ?", (tenant_id,)
            ).fetchone()
            return dict(result) if result else None
        finally:
            if not self._conn:
                conn.close()

    def get_all_tenants(self) -> List[Dict]:
        conn = self._get_connection()
        try:
            conn.row_factory = sqlite3.Row
            results = conn.execute("SELECT * FROM tenants ORDER BY name").fetchall()
            return [dict(r) for r in results]
        finally:
            if not self._conn:
                conn.close()

    def delete_tenant(self, tenant_id: int) -> Dict[str, int]:
        """ADMIN: permanently delete a tenant and all of its data. Sweeps every
        table that has a tenant_id column, then removes the tenant row itself.
        Returns {table: rows_deleted}."""
        conn = self._get_connection()
        try:
            tables = [r[0] for r in conn.execute(
                "SELECT name FROM sqlite_master WHERE type='table'").fetchall()]
            deleted = {}
            for t in tables:
                if t == "tenants":
                    continue
                cols = [c[1] for c in conn.execute(f"PRAGMA table_info({t})").fetchall()]
                if "tenant_id" in cols:
                    cur = conn.execute(f"DELETE FROM {t} WHERE tenant_id = ?", (tenant_id,))
                    if cur.rowcount:
                        deleted[t] = cur.rowcount
            cur = conn.execute("DELETE FROM tenants WHERE id = ?", (tenant_id,))
            deleted["tenants"] = cur.rowcount
            conn.commit()
            return deleted
        finally:
            if not self._conn:
                conn.close()

    def set_tenant_subscription(self, tenant_id: int, tier: str, status: str = "active"):
        """ADMIN: set a tenant's subscription tier + status (trial|basic|legacy)."""
        conn = self._get_connection()
        try:
            conn.execute(
                "UPDATE tenants SET subscription_tier = ?, subscription_status = ? WHERE id = ?",
                (tier, status, tenant_id))
            conn.commit()
        finally:
            if not self._conn:
                conn.close()

    def is_book_purchased(self, tenant_id: int) -> bool:
        """True if this tenant bought the one-time Legacy Book unlock."""
        conn = self._get_connection()
        try:
            row = conn.execute(
                "SELECT book_purchased FROM tenants WHERE id = ?", (tenant_id,)
            ).fetchone()
            return bool(row and row[0])
        finally:
            if not self._conn:
                conn.close()

    def set_book_purchased(self, tenant_id: int, purchased: bool = True):
        """Mark the one-time Legacy Book unlock for a tenant."""
        conn = self._get_connection()
        try:
            conn.execute("UPDATE tenants SET book_purchased = ? WHERE id = ?",
                         (1 if purchased else 0, tenant_id))
            conn.commit()
        finally:
            if not self._conn:
                conn.close()

    # ── Connected families (cross-tenant) ──

    def send_friend_request(self, tenant_id: int, target_family_code: str) -> Optional[Dict]:
        """Connect to another family by code. Sender is instantly connected.
        Target gets a pending request they must accept."""
        conn = self._get_connection()
        try:
            conn.row_factory = sqlite3.Row
            target = conn.execute(
                "SELECT * FROM tenants WHERE family_code = ?", (target_family_code,)
            ).fetchone()
            if not target:
                return None
            target_tid = target["id"]
            if target_tid == tenant_id:
                return None  # Can't connect to yourself

            # Check if already connected or pending in either direction
            existing = conn.execute(
                "SELECT 1 FROM connected_families WHERE "
                "(tenant_id = ? AND connected_tenant_id = ?) OR "
                "(tenant_id = ? AND connected_tenant_id = ?)",
                (tenant_id, target_tid, target_tid, tenant_id)
            ).fetchone()
            if existing:
                return None

            # Get both tenant names
            my_tenant = conn.execute("SELECT name FROM tenants WHERE id = ?", (tenant_id,)).fetchone()
            my_name = my_tenant["name"] if my_tenant else "Unknown"
            target_name = target["name"]

            # Sender side: instantly accepted, tree shared, wall visit set to now
            conn.execute(
                "INSERT INTO connected_families (tenant_id, connected_tenant_id, connected_tenant_name, status, share_tree, last_wall_visit) VALUES (?, ?, ?, 'accepted', 1, datetime('now'))",
                (tenant_id, target_tid, target_name))
            # Target side: pending, tree pre-shared, wall visit set to now
            conn.execute(
                "INSERT INTO connected_families (tenant_id, connected_tenant_id, connected_tenant_name, status, share_tree, last_wall_visit) VALUES (?, ?, ?, 'pending', 1, datetime('now'))",
                (target_tid, tenant_id, my_name))
            conn.commit()
            return {"connected_tenant_id": target_tid, "connected_tenant_name": target_name}
        finally:
            if not self._conn:
                conn.close()

    def send_friend_request_by_tenant(self, tenant_id: int, target_tenant_id: int) -> Optional[Dict]:
        """Connect to another family by tenant ID (email-based discovery).
        Same as send_friend_request but skips code lookup."""
        conn = self._get_connection()
        try:
            conn.row_factory = sqlite3.Row
            if target_tenant_id == tenant_id:
                return None

            existing = conn.execute(
                "SELECT 1 FROM connected_families WHERE "
                "(tenant_id = ? AND connected_tenant_id = ?) OR "
                "(tenant_id = ? AND connected_tenant_id = ?)",
                (tenant_id, target_tenant_id, target_tenant_id, tenant_id)
            ).fetchone()
            if existing:
                return None

            my_tenant = conn.execute("SELECT name FROM tenants WHERE id = ?", (tenant_id,)).fetchone()
            target_tenant = conn.execute("SELECT name FROM tenants WHERE id = ?", (target_tenant_id,)).fetchone()
            if not target_tenant:
                return None
            my_name = my_tenant["name"] if my_tenant else "Unknown"
            target_name = target_tenant["name"]

            # Sender side: instantly accepted, tree shared, wall visit set to now
            conn.execute(
                "INSERT INTO connected_families (tenant_id, connected_tenant_id, connected_tenant_name, status, share_tree, last_wall_visit) VALUES (?, ?, ?, 'accepted', 1, datetime('now'))",
                (tenant_id, target_tenant_id, target_name))
            # Target side: pending (they need to accept), tree pre-shared, wall visit set to now
            conn.execute(
                "INSERT INTO connected_families (tenant_id, connected_tenant_id, connected_tenant_name, status, share_tree, last_wall_visit) VALUES (?, ?, ?, 'pending', 1, datetime('now'))",
                (target_tenant_id, tenant_id, my_name))
            conn.commit()
            return {"connected_tenant_id": target_tenant_id, "connected_tenant_name": target_name}
        finally:
            if not self._conn:
                conn.close()

    def accept_friend_request(self, tenant_id: int, requester_tenant_id: int) -> bool:
        """Accept a pending friend request. Updates to accepted and adds sender to accepter's family tree."""
        conn = self._get_connection()
        try:
            conn.row_factory = sqlite3.Row
            # Find the pending request
            pending = conn.execute(
                "SELECT * FROM connected_families WHERE tenant_id = ? AND connected_tenant_id = ? AND status = 'pending'",
                (tenant_id, requester_tenant_id)
            ).fetchone()
            if not pending:
                return False

            # Update to accepted and auto-share trees both ways
            conn.execute(
                "UPDATE connected_families SET status = 'accepted', share_tree = 1 WHERE id = ?",
                (pending["id"],))
            # Also share on the other side
            conn.execute(
                "UPDATE connected_families SET share_tree = 1 WHERE tenant_id = ? AND connected_tenant_id = ? AND status = 'accepted'",
                (requester_tenant_id, tenant_id))

            # Get the requester's owner name to add to accepter's family tree
            requester_user = conn.execute(
                "SELECT name FROM user_profiles WHERE tenant_id = ? LIMIT 1",
                (requester_tenant_id,)
            ).fetchone()
            requester_name = requester_user["name"] if requester_user else pending["connected_tenant_name"]

            # Add requester to accepter's family tree as "Friend" (if not already there)
            existing_member = conn.execute(
                "SELECT 1 FROM family_members WHERE LOWER(name) = ? AND tenant_id = ?",
                (requester_name.lower(), tenant_id)
            ).fetchone()
            if not existing_member:
                name_norm = requester_name.lower().strip()
                conn.execute("""
                    INSERT INTO family_members (name, name_normalized, relationship, relation_to_owner,
                    generation, tenant_id, added_by)
                    VALUES (?, ?, 'friend', 'friend', 0, ?, 'Polly Connect')
                """, (requester_name, name_norm, tenant_id))

            conn.commit()
            return True
        finally:
            if not self._conn:
                conn.close()

    def decline_friend_request(self, tenant_id: int, requester_tenant_id: int):
        """Decline a friend request. Removes both directions."""
        conn = self._get_connection()
        try:
            # Remove both directions
            conn.execute(
                "DELETE FROM connected_families WHERE tenant_id = ? AND connected_tenant_id = ?",
                (tenant_id, requester_tenant_id))
            conn.execute(
                "DELETE FROM connected_families WHERE tenant_id = ? AND connected_tenant_id = ?",
                (requester_tenant_id, tenant_id))
            conn.commit()
        finally:
            if not self._conn:
                conn.close()

    def disconnect_family(self, tenant_id: int, connected_tenant_id: int):
        """Remove a family connection (both directions)."""
        conn = self._get_connection()
        try:
            conn.execute(
                "DELETE FROM connected_families WHERE tenant_id = ? AND connected_tenant_id = ?",
                (tenant_id, connected_tenant_id))
            conn.execute(
                "DELETE FROM connected_families WHERE tenant_id = ? AND connected_tenant_id = ?",
                (connected_tenant_id, tenant_id))
            conn.commit()
        finally:
            if not self._conn:
                conn.close()

    def get_connected_families(self, tenant_id: int) -> List[Dict]:
        """Get accepted connections for this tenant."""
        conn = self._get_connection()
        try:
            conn.row_factory = sqlite3.Row
            results = conn.execute(
                "SELECT * FROM connected_families WHERE tenant_id = ? AND status = 'accepted' ORDER BY connected_tenant_name",
                (tenant_id,)
            ).fetchall()
            return [dict(r) for r in results]
        finally:
            if not self._conn:
                conn.close()

    def get_pending_friend_requests(self, tenant_id: int) -> List[Dict]:
        """Get pending friend requests sent TO this tenant."""
        conn = self._get_connection()
        try:
            conn.row_factory = sqlite3.Row
            results = conn.execute(
                "SELECT * FROM connected_families WHERE tenant_id = ? AND status = 'pending' ORDER BY created_at DESC",
                (tenant_id,)
            ).fetchall()
            return [dict(r) for r in results]
        finally:
            if not self._conn:
                conn.close()

    # ── Shared Wall ──

    def share_to_wall(self, from_tenant_id: int, to_tenant_id: int,
                      content_type: str, content_id: int, caption: str = None) -> Optional[int]:
        """Share a photo/story/message to the wall between two connected families."""
        conn = self._get_connection()
        try:
            # Verify connection exists
            conn.row_factory = sqlite3.Row
            exists = conn.execute(
                "SELECT 1 FROM connected_families WHERE tenant_id = ? AND connected_tenant_id = ? AND status = 'accepted'",
                (from_tenant_id, to_tenant_id)
            ).fetchone()
            if not exists:
                return None
            # Prevent duplicates
            dup = conn.execute(
                "SELECT 1 FROM shared_wall_items WHERE from_tenant_id = ? AND to_tenant_id = ? AND content_type = ? AND content_id = ?",
                (from_tenant_id, to_tenant_id, content_type, content_id)
            ).fetchone()
            if dup:
                return None
            cursor = conn.execute(
                "INSERT INTO shared_wall_items (from_tenant_id, to_tenant_id, content_type, content_id, caption) VALUES (?, ?, ?, ?, ?)",
                (from_tenant_id, to_tenant_id, content_type, content_id, caption))
            conn.commit()
            return cursor.lastrowid
        finally:
            if not self._conn:
                conn.close()

    def get_wall_items(self, tenant_a: int, tenant_b: int, limit: int = 50) -> List[Dict]:
        """Get all shared wall items between two tenants (both directions), newest first."""
        conn = self._get_connection()
        try:
            conn.row_factory = sqlite3.Row
            rows = conn.execute("""
                SELECT w.*, t.name as from_tenant_name
                FROM shared_wall_items w
                LEFT JOIN tenants t ON t.id = w.from_tenant_id
                WHERE (w.from_tenant_id = ? AND w.to_tenant_id = ?)
                   OR (w.from_tenant_id = ? AND w.to_tenant_id = ?)
                ORDER BY w.created_at DESC LIMIT ?
            """, (tenant_a, tenant_b, tenant_b, tenant_a, limit)).fetchall()

            items = []
            for r in rows:
                item = dict(r)
                ctype = item["content_type"]
                cid = item["content_id"]
                if ctype == "photo" and cid:
                    photo = conn.execute("SELECT filename, caption, date_taken FROM photos WHERE id = ?", (cid,)).fetchone()
                    if photo:
                        item["photo"] = dict(photo)
                    else:
                        continue  # skip orphaned
                elif ctype == "story" and cid:
                    story = conn.execute(
                        "SELECT corrected_transcript, transcript, audio_s3_key, speaker_name, question_text FROM stories WHERE id = ?",
                        (cid,)).fetchone()
                    if story:
                        item["story"] = dict(story)
                    else:
                        continue
                elif ctype == "message" and cid:
                    msg = conn.execute(
                        "SELECT from_name, message, audio_filename FROM family_messages WHERE id = ?",
                        (cid,)).fetchone()
                    if msg:
                        item["message"] = dict(msg)
                    else:
                        continue
                items.append(item)
            return items
        finally:
            if not self._conn:
                conn.close()

    def react_to_wall_item(self, wall_item_id: int, tenant_id: int, reaction: str) -> bool:
        """Toggle a reaction on a wall item. Same reaction again = remove it."""
        conn = self._get_connection()
        try:
            existing = conn.execute(
                "SELECT reaction FROM wall_reactions WHERE wall_item_id = ? AND tenant_id = ?",
                (wall_item_id, tenant_id)
            ).fetchone()
            if existing and existing[0] == reaction:
                # Same reaction = toggle off
                conn.execute("DELETE FROM wall_reactions WHERE wall_item_id = ? AND tenant_id = ?",
                             (wall_item_id, tenant_id))
            else:
                # New or different reaction = upsert
                conn.execute(
                    "INSERT OR REPLACE INTO wall_reactions (wall_item_id, tenant_id, reaction) VALUES (?, ?, ?)",
                    (wall_item_id, tenant_id, reaction))
            conn.commit()
            return True
        finally:
            if not self._conn:
                conn.close()

    def get_wall_reactions(self, wall_item_ids: list) -> dict:
        """Get reactions for a list of wall item IDs. Returns {item_id: [{tenant_id, reaction}]}."""
        if not wall_item_ids:
            return {}
        conn = self._get_connection()
        try:
            conn.row_factory = sqlite3.Row
            placeholders = ",".join("?" * len(wall_item_ids))
            rows = conn.execute(
                f"SELECT wall_item_id, tenant_id, reaction FROM wall_reactions WHERE wall_item_id IN ({placeholders})",
                wall_item_ids
            ).fetchall()
            result = {}
            for r in rows:
                wid = r["wall_item_id"]
                if wid not in result:
                    result[wid] = []
                result[wid].append({"tenant_id": r["tenant_id"], "reaction": r["reaction"]})
            return result
        finally:
            if not self._conn:
                conn.close()

    def add_wall_comment(self, wall_item_id: int, tenant_id: int,
                         tenant_name: str, comment: str = None,
                         audio_filename: str = None) -> int:
        conn = self._get_connection()
        try:
            cursor = conn.execute(
                "INSERT INTO wall_comments (wall_item_id, tenant_id, tenant_name, comment, audio_filename) VALUES (?, ?, ?, ?, ?)",
                (wall_item_id, tenant_id, tenant_name, comment, audio_filename))
            conn.commit()
            return cursor.lastrowid
        finally:
            if not self._conn:
                conn.close()

    def get_wall_comments(self, wall_item_ids: list) -> dict:
        """Returns {item_id: [comment_dicts]} for all given wall item IDs."""
        if not wall_item_ids:
            return {}
        conn = self._get_connection()
        try:
            conn.row_factory = sqlite3.Row
            placeholders = ",".join("?" * len(wall_item_ids))
            rows = conn.execute(
                f"SELECT * FROM wall_comments WHERE wall_item_id IN ({placeholders}) ORDER BY created_at ASC",
                wall_item_ids
            ).fetchall()
            result = {}
            for r in rows:
                d = dict(r)
                wid = d["wall_item_id"]
                if wid not in result:
                    result[wid] = []
                result[wid].append(d)
            return result
        finally:
            if not self._conn:
                conn.close()

    def get_wall_new_count(self, from_tenant_id: int, to_tenant_id: int) -> int:
        """Count wall items shared TO this tenant since their last wall visit."""
        conn = self._get_connection()
        try:
            # Get last visit timestamp
            row = conn.execute(
                "SELECT last_wall_visit FROM connected_families WHERE tenant_id = ? AND connected_tenant_id = ? AND status = 'accepted'",
                (to_tenant_id, from_tenant_id)
            ).fetchone()
            last_visit = row[0] if row and row[0] else "2000-01-01"
            count = conn.execute(
                "SELECT COUNT(*) FROM shared_wall_items WHERE from_tenant_id = ? AND to_tenant_id = ? AND created_at > ?",
                (from_tenant_id, to_tenant_id, last_visit)
            ).fetchone()[0]
            return count
        finally:
            if not self._conn:
                conn.close()

    def delete_wall_item(self, item_id: int, tenant_id: int) -> bool:
        """Delete a wall item (only the sharer can remove it)."""
        conn = self._get_connection()
        try:
            conn.execute("DELETE FROM shared_wall_items WHERE id = ? AND from_tenant_id = ?", (item_id, tenant_id))
            conn.commit()
            return True
        finally:
            if not self._conn:
                conn.close()

    # ── Family Invitations ──

    def save_family_invitation(self, tenant_id: int, family_member_id: int,
                                inviter_name: str, invitee_name: str,
                                invitee_email: str, voice_filename: str = None,
                                family_code: str = None) -> int:
        conn = self._get_connection()
        try:
            cursor = conn.execute("""
                INSERT INTO family_invitations
                (tenant_id, family_member_id, inviter_name, invitee_name, invitee_email,
                 voice_message_filename, family_code)
                VALUES (?, ?, ?, ?, ?, ?, ?)
            """, (tenant_id, family_member_id, inviter_name, invitee_name,
                  invitee_email, voice_filename, family_code))
            conn.commit()
            return cursor.lastrowid
        finally:
            if not self._conn:
                conn.close()

    def get_invitation_by_id(self, invitation_id: int) -> Optional[Dict]:
        conn = self._get_connection()
        try:
            conn.row_factory = sqlite3.Row
            result = conn.execute(
                "SELECT * FROM family_invitations WHERE id = ?", (invitation_id,)
            ).fetchone()
            return dict(result) if result else None
        finally:
            if not self._conn:
                conn.close()

    def get_invitations_for_tenant(self, tenant_id: int) -> List[Dict]:
        conn = self._get_connection()
        try:
            conn.row_factory = sqlite3.Row
            results = conn.execute(
                "SELECT * FROM family_invitations WHERE tenant_id = ? ORDER BY sent_at DESC",
                (tenant_id,)
            ).fetchall()
            return [dict(r) for r in results]
        finally:
            if not self._conn:
                conn.close()

    def get_invitation_by_email_and_tenant(self, email: str, tenant_id: int) -> Optional[Dict]:
        conn = self._get_connection()
        try:
            conn.row_factory = sqlite3.Row
            result = conn.execute(
                "SELECT * FROM family_invitations WHERE LOWER(invitee_email) = ? AND tenant_id = ? ORDER BY sent_at DESC LIMIT 1",
                (email.lower(), tenant_id)
            ).fetchone()
            return dict(result) if result else None
        finally:
            if not self._conn:
                conn.close()

    def update_invitation_status(self, invitation_id: int, status: str, **kwargs):
        conn = self._get_connection()
        try:
            timestamp_col = {
                "visited": "visited_at",
                "onboarded": "onboarded_at",
                "converted": "converted_at",
            }.get(status)
            if timestamp_col:
                conn.execute(
                    f"UPDATE family_invitations SET status = ?, {timestamp_col} = CURRENT_TIMESTAMP WHERE id = ?",
                    (status, invitation_id))
            else:
                conn.execute(
                    "UPDATE family_invitations SET status = ? WHERE id = ?",
                    (status, invitation_id))
            # Handle extra kwargs like converted_tenant_id
            for key, val in kwargs.items():
                if key in ("converted_tenant_id", "feedback_rating", "feedback_note"):
                    conn.execute(
                        f"UPDATE family_invitations SET {key} = ? WHERE id = ?",
                        (val, invitation_id))
            conn.commit()
        finally:
            if not self._conn:
                conn.close()

    def mark_session_onboarded(self, session_id: str, step: int = None):
        conn = self._get_connection()
        try:
            if step:
                conn.execute(
                    "UPDATE web_sessions SET last_onboarding_step = ? WHERE id = ?",
                    (step, session_id))
            else:
                conn.execute(
                    "UPDATE web_sessions SET onboarding_complete = 1 WHERE id = ?",
                    (session_id,))
            conn.commit()
        finally:
            if not self._conn:
                conn.close()

    def save_onboarding_feedback(self, invitation_id: int, rating: int, note: str = None):
        conn = self._get_connection()
        try:
            conn.execute(
                "UPDATE family_invitations SET feedback_rating = ?, feedback_note = ? WHERE id = ?",
                (rating, note, invitation_id))
            conn.commit()
        finally:
            if not self._conn:
                conn.close()

    def get_invitation_funnel_stats(self) -> Dict:
        conn = self._get_connection()
        try:
            row = conn.execute("""
                SELECT
                    COUNT(*) as total_sent,
                    SUM(CASE WHEN status IN ('visited','onboarded','converted') THEN 1 ELSE 0 END) as total_visited,
                    SUM(CASE WHEN status IN ('onboarded','converted') THEN 1 ELSE 0 END) as total_onboarded,
                    SUM(CASE WHEN status = 'converted' THEN 1 ELSE 0 END) as total_converted
                FROM family_invitations
            """).fetchone()
            return {
                "total_sent": row[0] or 0,
                "total_visited": row[1] or 0,
                "total_onboarded": row[2] or 0,
                "total_converted": row[3] or 0,
            }
        finally:
            if not self._conn:
                conn.close()

    # ── Account management ──

    def create_account(self, email: str, password_hash: str, name: str,
                       tenant_id: int, role: str = "caretaker") -> int:
        conn = self._get_connection()
        try:
            cursor = conn.execute("""
                INSERT INTO accounts (email, password_hash, name, tenant_id, role, terms_accepted_at)
                VALUES (?, ?, ?, ?, ?, CURRENT_TIMESTAMP)
            """, (email, password_hash, name, tenant_id, role))
            conn.commit()
            return cursor.lastrowid
        finally:
            if not self._conn:
                conn.close()

    def get_account_by_email(self, email: str) -> Optional[Dict]:
        conn = self._get_connection()
        try:
            conn.row_factory = sqlite3.Row
            result = conn.execute(
                "SELECT * FROM accounts WHERE email = ?", (email,)
            ).fetchone()
            return dict(result) if result else None
        finally:
            if not self._conn:
                conn.close()

    def get_account_by_id(self, account_id: int) -> Optional[Dict]:
        conn = self._get_connection()
        try:
            conn.row_factory = sqlite3.Row
            result = conn.execute(
                "SELECT * FROM accounts WHERE id = ?", (account_id,)
            ).fetchone()
            return dict(result) if result else None
        finally:
            if not self._conn:
                conn.close()

    def update_account_login(self, account_id: int):
        conn = self._get_connection()
        try:
            conn.execute(
                "UPDATE accounts SET last_login = CURRENT_TIMESTAMP WHERE id = ?",
                (account_id,)
            )
            conn.commit()
        finally:
            if not self._conn:
                conn.close()

    def has_accounts(self) -> bool:
        conn = self._get_connection()
        try:
            count = conn.execute("SELECT COUNT(*) FROM accounts").fetchone()[0]
            return count > 0
        finally:
            if not self._conn:
                conn.close()

    # ── Web session management ──

    def create_web_session(self, account_id: int, tenant_id: int,
                           duration_hours: int = 72) -> str:
        session_id = secrets.token_urlsafe(32)
        expires_at = (datetime.utcnow() + timedelta(hours=duration_hours)).isoformat()
        conn = self._get_connection()
        try:
            conn.execute("""
                INSERT INTO web_sessions (id, account_id, tenant_id, expires_at)
                VALUES (?, ?, ?, ?)
            """, (session_id, account_id, tenant_id, expires_at))
            conn.commit()
            return session_id
        finally:
            if not self._conn:
                conn.close()

    def get_web_session(self, session_id: str) -> Optional[Dict]:
        conn = self._get_connection()
        try:
            conn.row_factory = sqlite3.Row
            result = conn.execute("""
                SELECT ws.*, a.name as account_name, a.email as account_email,
                       a.role as account_role, a.is_admin as account_is_admin,
                       ws.role as session_role, ws.family_name
                FROM web_sessions ws
                LEFT JOIN accounts a ON ws.account_id = a.id
                WHERE ws.id = ? AND ws.expires_at > datetime('now')
            """, (session_id,)).fetchone()
            return dict(result) if result else None
        finally:
            if not self._conn:
                conn.close()

    def touch_web_session(self, session_id: str):
        conn = self._get_connection()
        try:
            conn.execute(
                "UPDATE web_sessions SET last_active = CURRENT_TIMESTAMP WHERE id = ?",
                (session_id,)
            )
            conn.commit()
        finally:
            if not self._conn:
                conn.close()

    def delete_web_session(self, session_id: str):
        conn = self._get_connection()
        try:
            conn.execute("DELETE FROM web_sessions WHERE id = ?", (session_id,))
            conn.commit()
        finally:
            if not self._conn:
                conn.close()

    def cleanup_expired_sessions(self):
        conn = self._get_connection()
        try:
            conn.execute("DELETE FROM web_sessions WHERE expires_at <= datetime('now')")
            conn.commit()
        finally:
            if not self._conn:
                conn.close()

    # ── Family access code ──

    def generate_family_code(self, tenant_id: int) -> str:
        import random
        code = f"{random.randint(0, 999999):06d}"
        conn = self._get_connection()
        try:
            conn.execute(
                "UPDATE tenants SET family_code = ?, family_code_created_at = CURRENT_TIMESTAMP WHERE id = ?",
                (code, tenant_id)
            )
            conn.commit()
            return code
        finally:
            if not self._conn:
                conn.close()

    def revoke_family_code(self, tenant_id: int):
        conn = self._get_connection()
        try:
            conn.execute(
                "UPDATE tenants SET family_code = NULL, family_code_created_at = NULL WHERE id = ?",
                (tenant_id,)
            )
            # Kill all active family sessions for this tenant
            conn.execute(
                "DELETE FROM web_sessions WHERE tenant_id = ? AND role = 'family'",
                (tenant_id,)
            )
            conn.commit()
        finally:
            if not self._conn:
                conn.close()

    def validate_family_code(self, code: str) -> Optional[Dict]:
        """Validate a family access code. Checks tenant-level family_code only."""
        conn = self._get_connection()
        try:
            conn.row_factory = sqlite3.Row
            result = conn.execute(
                "SELECT * FROM tenants WHERE family_code = ?", (code,)
            ).fetchone()
            if result:
                return {"tenant": dict(result), "type": "general"}
            return None
        finally:
            if not self._conn:
                conn.close()

    def create_family_session(self, tenant_id: int, family_name: str,
                              duration_hours: int = 72) -> str:
        session_id = secrets.token_urlsafe(32)
        expires_at = (datetime.utcnow() + timedelta(hours=duration_hours)).isoformat()
        conn = self._get_connection()
        try:
            conn.execute("""
                INSERT INTO web_sessions (id, account_id, tenant_id, expires_at, family_name, role)
                VALUES (?, NULL, ?, ?, ?, 'family')
            """, (session_id, tenant_id, expires_at, family_name))
            conn.commit()
            return session_id
        finally:
            if not self._conn:
                conn.close()

    # ── Device management (per-tenant) ──

    def register_device(self, device_id: str, tenant_id: int, name: str = None,
                        api_key: str = None) -> Dict:
        api_key_hash = hashlib.sha256(api_key.encode()).hexdigest() if api_key else None
        conn = self._get_connection()
        try:
            conn.row_factory = sqlite3.Row
            existing = conn.execute(
                "SELECT * FROM devices WHERE device_id = ?", (device_id,)
            ).fetchone()
            if existing:
                conn.execute("""
                    UPDATE devices SET tenant_id = ?, name = ?, api_key_hash = ?,
                    last_seen = CURRENT_TIMESTAMP WHERE device_id = ?
                """, (tenant_id, name or existing["name"], api_key_hash or existing["api_key_hash"],
                      device_id))
            else:
                conn.execute("""
                    INSERT INTO devices (device_id, tenant_id, name, api_key_hash)
                    VALUES (?, ?, ?, ?)
                """, (device_id, tenant_id, name, api_key_hash))
            conn.commit()
            result = conn.execute(
                "SELECT * FROM devices WHERE device_id = ?", (device_id,)
            ).fetchone()
            return dict(result)
        finally:
            if not self._conn:
                conn.close()

    def get_device(self, device_id: str) -> Optional[Dict]:
        conn = self._get_connection()
        try:
            conn.row_factory = sqlite3.Row
            result = conn.execute(
                "SELECT * FROM devices WHERE device_id = ?", (device_id,)
            ).fetchone()
            return dict(result) if result else None
        finally:
            if not self._conn:
                conn.close()

    def get_all_devices(self) -> List[Dict]:
        """All devices regardless of tenant (for admin view)."""
        conn = self._get_connection()
        try:
            conn.row_factory = sqlite3.Row
            results = conn.execute(
                """SELECT d.*, t.name AS tenant_name
                   FROM devices d LEFT JOIN tenants t ON d.tenant_id = t.id
                   ORDER BY d.registered_at DESC"""
            ).fetchall()
            return [dict(r) for r in results]
        finally:
            if not self._conn:
                conn.close()

    def get_device_by_api_key_hash(self, api_key_hash: str) -> Optional[Dict]:
        conn = self._get_connection()
        try:
            conn.row_factory = sqlite3.Row
            result = conn.execute(
                "SELECT * FROM devices WHERE api_key_hash = ?", (api_key_hash,)
            ).fetchone()
            return dict(result) if result else None
        finally:
            if not self._conn:
                conn.close()

    def get_devices_by_tenant(self, tenant_id: int) -> List[Dict]:
        conn = self._get_connection()
        try:
            conn.row_factory = sqlite3.Row
            results = conn.execute(
                "SELECT * FROM devices WHERE tenant_id = ? ORDER BY registered_at DESC",
                (tenant_id,)
            ).fetchall()
            return [dict(r) for r in results]
        finally:
            if not self._conn:
                conn.close()

    def get_device_settings(self, device_id: str, tenant_id: int) -> Dict:
        """Get merged settings: device-level overrides > tenant profile defaults.
        NULL device columns inherit from user_profiles."""
        conn = self._get_connection()
        try:
            conn.row_factory = sqlite3.Row
            device = conn.execute(
                "SELECT * FROM devices WHERE device_id = ?", (device_id,)
            ).fetchone()
            profile = conn.execute(
                "SELECT * FROM user_profiles WHERE tenant_id = ? LIMIT 1", (tenant_id,)
            ).fetchone()

            dev = dict(device) if device else {}
            prof = dict(profile) if profile else {}

            def _pick(dev_key, prof_key, default):
                v = dev.get(dev_key)
                if v is not None:
                    return v
                v = prof.get(prof_key)
                if v is not None:
                    return v
                return default

            return {
                "squawk_interval": _pick("dev_squawk_interval", "squawk_interval", 10),
                "chatter_interval": _pick("dev_chatter_interval", "chatter_interval", 45),
                "quiet_hours_start": _pick("dev_quiet_hours_start", "quiet_hours_start", 21),
                "quiet_hours_end": _pick("dev_quiet_hours_end", "quiet_hours_end", 7),
                "squawk_volume": _pick("dev_squawk_volume", "squawk_volume", 30),
                "squawk_snoozed_until": dev.get("dev_snoozed_until") or prof.get("squawk_snoozed_until"),
                "squawk_quiet_override": dev.get("dev_quiet_override") if dev.get("dev_quiet_override") is not None else prof.get("squawk_quiet_override", 0),
                "message_nag_enabled": _pick("dev_message_nag", "message_nag_enabled", 1) if "message_nag_enabled" in prof else (dev.get("dev_message_nag") if dev.get("dev_message_nag") is not None else 1),
                "rms_threshold": prof.get("rms_threshold", 200),
                "voice_volume": prof.get("voice_volume", 100),
                "kid_mode": dev.get("dev_kid_mode") if dev.get("dev_kid_mode") is not None else prof.get("kid_mode", 0),
            }
        finally:
            if not self._conn:
                conn.close()

    def update_device_settings(self, device_id: str, **kwargs) -> None:
        """Update per-device settings columns. Only updates provided keys.
        Pass None to clear an override (revert to tenant default)."""
        col_map = {
            "quiet_hours_start": "dev_quiet_hours_start",
            "quiet_hours_end": "dev_quiet_hours_end",
            "squawk_interval": "dev_squawk_interval",
            "chatter_interval": "dev_chatter_interval",
            "squawk_volume": "dev_squawk_volume",
            "squawk_snoozed_until": "dev_snoozed_until",
            "squawk_quiet_override": "dev_quiet_override",
            "message_nag_enabled": "dev_message_nag",
            "kid_mode": "dev_kid_mode",
        }
        updates = {}
        for k, v in kwargs.items():
            if k in col_map:
                updates[col_map[k]] = v
        if not updates:
            return
        set_clause = ", ".join(f"{k} = ?" for k in updates)
        values = list(updates.values()) + [device_id]
        conn = self._get_connection()
        try:
            conn.execute(f"UPDATE devices SET {set_clause} WHERE device_id = ?", values)
            conn.commit()
        finally:
            if not self._conn:
                conn.close()

    def update_device_last_seen(self, device_id: str):
        conn = self._get_connection()
        try:
            conn.execute(
                "UPDATE devices SET last_seen = CURRENT_TIMESTAMP WHERE device_id = ?",
                (device_id,)
            )
            conn.commit()
        finally:
            if not self._conn:
                conn.close()

    def delete_device(self, device_id: str, tenant_id: int = None, is_admin: bool = False) -> bool:
        conn = self._get_connection()
        try:
            if is_admin:
                cursor = conn.execute(
                    "DELETE FROM devices WHERE device_id = ?", (device_id,)
                )
            else:
                cursor = conn.execute(
                    "DELETE FROM devices WHERE device_id = ? AND tenant_id = ?",
                    (device_id, tenant_id)
                )
            conn.commit()
            return cursor.rowcount > 0
        finally:
            if not self._conn:
                conn.close()

    def generate_claim_code(self, device_id: str, tenant_id: int = None) -> str:
        """Generate a unique 6-digit claim code for a device."""
        import random
        conn = self._get_connection()
        try:
            for _ in range(100):
                code = f"{random.randint(0, 999999):06d}"
                t_clash = conn.execute(
                    "SELECT 1 FROM tenants WHERE family_code = ?", (code,)
                ).fetchone()
                m_clash = conn.execute(
                    "SELECT 1 FROM family_members WHERE access_code = ?", (code,)
                ).fetchone()
                d_clash = conn.execute(
                    "SELECT 1 FROM devices WHERE claim_code = ?", (code,)
                ).fetchone()
                if not t_clash and not m_clash and not d_clash:
                    conn.execute(
                        "UPDATE devices SET claim_code = ? WHERE device_id = ?",
                        (code, device_id)
                    )
                    conn.commit()
                    return code
            raise RuntimeError("Could not generate unique claim code after 100 attempts")
        finally:
            if not self._conn:
                conn.close()

    def claim_device(self, claim_code: str, new_tenant_id: int, device_name: str = None) -> Optional[Dict]:
        """Claim a device by its 6-digit code. Transfers to new tenant. Optionally rename."""
        conn = self._get_connection()
        try:
            conn.row_factory = sqlite3.Row
            device = conn.execute(
                "SELECT * FROM devices WHERE claim_code = ? AND claimed_at IS NULL",
                (claim_code,)
            ).fetchone()
            if not device:
                return None
            if device_name:
                conn.execute("""
                    UPDATE devices SET tenant_id = ?, claimed_at = CURRENT_TIMESTAMP,
                    claim_code = NULL, name = ?
                    WHERE device_id = ?
                """, (new_tenant_id, device_name, device["device_id"]))
            else:
                conn.execute("""
                    UPDATE devices SET tenant_id = ?, claimed_at = CURRENT_TIMESTAMP,
                    claim_code = NULL
                    WHERE device_id = ?
                """, (new_tenant_id, device["device_id"]))
            conn.commit()
            result = conn.execute(
                "SELECT * FROM devices WHERE device_id = ?", (device["device_id"],)
            ).fetchone()
            return dict(result)
        finally:
            if not self._conn:
                conn.close()

    def provision_device_by_claim_code(self, claim_code: str) -> Optional[Dict]:
        """Device calls this with claim code to get its device_id + fresh api_key."""
        from core.auth import generate_api_key
        conn = self._get_connection()
        try:
            conn.row_factory = sqlite3.Row
            device = conn.execute(
                "SELECT * FROM devices WHERE claim_code = ?",
                (claim_code,)
            ).fetchone()
            if not device:
                return None
            # Generate fresh API key
            raw_key = generate_api_key()
            key_hash = hashlib.sha256(raw_key.encode()).hexdigest()
            conn.execute(
                "UPDATE devices SET api_key_hash = ? WHERE device_id = ?",
                (key_hash, device["device_id"])
            )
            conn.commit()
            return {
                "device_id": device["device_id"],
                "api_key": raw_key,
            }
        finally:
            if not self._conn:
                conn.close()

    # ── Items (memory storage) ──

    def store_item(self, item: str, location: str, context: Optional[str] = None,
                   raw_input: Optional[str] = None, tenant_id: int = None,
                   prep: str = "on") -> int:
        item_norm = self._normalize(item)
        location_norm = self._normalize(location)

        conn = self._get_connection()
        try:
            if tenant_id:
                existing = conn.execute(
                    "SELECT id FROM items WHERE item_normalized = ? AND tenant_id = ?",
                    (item_norm, tenant_id)
                ).fetchone()
            else:
                existing = conn.execute(
                    "SELECT id FROM items WHERE item_normalized = ?", (item_norm,)
                ).fetchone()

            if existing:
                conn.execute("""
                    UPDATE items SET location = ?, location_normalized = ?,
                    context = ?, raw_input = ?, prep = ?, updated_at = CURRENT_TIMESTAMP
                    WHERE id = ?
                """, (location, location_norm, context, raw_input, prep, existing[0]))
                conn.commit()
                return existing[0]
            else:
                cursor = conn.execute("""
                    INSERT INTO items (item, item_normalized, location,
                                      location_normalized, context, raw_input, prep, tenant_id)
                    VALUES (?, ?, ?, ?, ?, ?, ?, ?)
                """, (item, item_norm, location, location_norm, context, raw_input, prep, tenant_id))
                conn.commit()
                return cursor.lastrowid
        finally:
            if not self._conn:
                conn.close()

    def find_item(self, item: str, tenant_id: int = None) -> List[Dict]:
        item_norm = self._normalize(item)
        conn = self._get_connection()
        try:
            conn.row_factory = sqlite3.Row
            t_clause = " AND tenant_id = ?" if tenant_id else ""
            t_params = (tenant_id,) if tenant_id else ()

            results = conn.execute(
                f"SELECT id, item, location, context, prep, created_at, updated_at FROM items WHERE item_normalized = ?{t_clause}",
                (item_norm,) + t_params
            ).fetchall()

            if not results:
                results = conn.execute(
                    f"SELECT id, item, location, context, prep, created_at, updated_at FROM items WHERE item_normalized LIKE ?{t_clause}",
                    (f"%{item_norm}%",) + t_params
                ).fetchall()

            return [dict(r) for r in results]
        finally:
            if not self._conn:
                conn.close()

    def find_by_location(self, location: str, tenant_id: int = None) -> List[Dict]:
        location_norm = self._normalize(location)
        conn = self._get_connection()
        try:
            conn.row_factory = sqlite3.Row
            t_clause = " AND tenant_id = ?" if tenant_id else ""
            t_params = (tenant_id,) if tenant_id else ()
            results = conn.execute(
                f"SELECT id, item, location, context, created_at, updated_at FROM items WHERE location_normalized LIKE ?{t_clause}",
                (f"%{location_norm}%",) + t_params
            ).fetchall()
            return [dict(r) for r in results]
        finally:
            if not self._conn:
                conn.close()

    def list_all(self, tenant_id: int = None) -> List[Dict]:
        conn = self._get_connection()
        try:
            conn.row_factory = sqlite3.Row
            if tenant_id:
                results = conn.execute(
                    "SELECT id, item, location, context, created_at, updated_at FROM items WHERE tenant_id = ? ORDER BY updated_at DESC",
                    (tenant_id,)
                ).fetchall()
            else:
                results = conn.execute(
                    "SELECT id, item, location, context, created_at, updated_at FROM items ORDER BY updated_at DESC"
                ).fetchall()
            return [dict(r) for r in results]
        finally:
            if not self._conn:
                conn.close()

    def update_item(self, item_id: int, item: str = None, location: str = None,
                    prep: str = None, tenant_id: int = None) -> bool:
        conn = self._get_connection()
        try:
            updates = []
            params = []
            if item is not None:
                updates.append("item = ?")
                updates.append("item_normalized = ?")
                params.extend([item, self._normalize(item)])
            if location is not None:
                updates.append("location = ?")
                updates.append("location_normalized = ?")
                params.extend([location, self._normalize(location)])
            if prep is not None:
                updates.append("prep = ?")
                params.append(prep)
            if not updates:
                return False
            updates.append("updated_at = CURRENT_TIMESTAMP")
            query = f"UPDATE items SET {', '.join(updates)} WHERE id = ?"
            params.append(item_id)
            if tenant_id:
                query += " AND tenant_id = ?"
                params.append(tenant_id)
            cursor = conn.execute(query, params)
            conn.commit()
            return cursor.rowcount > 0
        finally:
            if not self._conn:
                conn.close()

    def delete_item(self, item: str, tenant_id: int = None) -> bool:
        item_norm = self._normalize(item)
        conn = self._get_connection()
        try:
            if tenant_id:
                cursor = conn.execute(
                    "DELETE FROM items WHERE item_normalized = ? AND tenant_id = ?",
                    (item_norm, tenant_id)
                )
            else:
                cursor = conn.execute(
                    "DELETE FROM items WHERE item_normalized = ?", (item_norm,)
                )
            conn.commit()
            return cursor.rowcount > 0
        finally:
            if not self._conn:
                conn.close()

    def delete_items_by_ids(self, ids: list, tenant_id: int = None) -> int:
        """Bulk-delete stored items by id (tenant-scoped). Returns rows deleted."""
        ids = [int(i) for i in ids if str(i).isdigit()]
        if not ids:
            return 0
        conn = self._get_connection()
        try:
            placeholders = ",".join("?" * len(ids))
            params = list(ids)
            q = f"DELETE FROM items WHERE id IN ({placeholders})"
            if tenant_id:
                q += " AND tenant_id = ?"
                params.append(tenant_id)
            cursor = conn.execute(q, params)
            conn.commit()
            return cursor.rowcount
        finally:
            if not self._conn:
                conn.close()

    def delete_by_id(self, item_id: int, tenant_id: int = None) -> bool:
        """Delete an item by id. When tenant_id is given the delete is scoped to
        that tenant, so a user can never delete another tenant's item."""
        conn = self._get_connection()
        try:
            if tenant_id is not None:
                cursor = conn.execute(
                    "DELETE FROM items WHERE id = ? AND tenant_id = ?",
                    (item_id, tenant_id))
            else:
                cursor = conn.execute("DELETE FROM items WHERE id = ?", (item_id,))
            conn.commit()
            return cursor.rowcount > 0
        finally:
            if not self._conn:
                conn.close()

    def search(self, query: str, tenant_id: int = None) -> List[Dict]:
        query_norm = self._normalize(query)
        if not query_norm:
            return []
        conn = self._get_connection()
        try:
            conn.row_factory = sqlite3.Row
            t_clause = " AND tenant_id = ?" if tenant_id else ""
            t_params = (tenant_id,) if tenant_id else ()
            results = conn.execute(
                f"SELECT id, item, location, context, created_at, updated_at FROM items WHERE (item LIKE ? OR location LIKE ? OR context LIKE ?){t_clause} LIMIT 20",
                (f"%{query_norm}%",) * 3 + t_params
            ).fetchall()
            return [dict(r) for r in results]
        finally:
            if not self._conn:
                conn.close()

    def get_stats(self, tenant_id: int = None) -> Dict:
        conn = self._get_connection()
        try:
            t_clause = " WHERE tenant_id = ?" if tenant_id else ""
            t_params = (tenant_id,) if tenant_id else ()

            total = conn.execute(f"SELECT COUNT(*) FROM items{t_clause}", t_params).fetchone()[0]
            locations = conn.execute(
                f"SELECT COUNT(DISTINCT location_normalized) FROM items{t_clause}", t_params
            ).fetchone()[0]
            recent = conn.execute(
                f"SELECT item, location FROM items{t_clause} ORDER BY updated_at DESC LIMIT 5", t_params
            ).fetchall()
            return {
                "total_items": total,
                "unique_locations": locations,
                "recent": [{"item": r[0], "location": r[1]} for r in recent]
            }
        finally:
            if not self._conn:
                conn.close()

    # ── Medications ──

    def add_medication(self, user_id: int, name: str, dosage: str, times: str,
                       active_days: str = None, tenant_id: int = None,
                       device_id: str = None) -> int:
        conn = self._get_connection()
        try:
            cursor = conn.execute("""
                INSERT INTO medications (user_id, name, dosage, times, active_days, tenant_id, device_id)
                VALUES (?, ?, ?, ?, ?, ?, ?)
            """, (user_id, name, dosage, times,
                  active_days or '["mon","tue","wed","thu","fri","sat","sun"]', tenant_id, device_id))
            conn.commit()
            return cursor.lastrowid
        finally:
            if not self._conn:
                conn.close()

    def get_medications(self, user_id: int = None, tenant_id: int = None) -> List[Dict]:
        conn = self._get_connection()
        try:
            conn.row_factory = sqlite3.Row
            query = "SELECT * FROM medications WHERE active = 1"
            params = []
            if user_id:
                query += " AND user_id = ?"
                params.append(user_id)
            if tenant_id:
                query += " AND tenant_id = ?"
                params.append(tenant_id)
            results = conn.execute(query, params).fetchall()
            return [dict(r) for r in results]
        finally:
            if not self._conn:
                conn.close()

    def get_medication_by_id(self, medication_id: int, tenant_id: int = None) -> Optional[Dict]:
        conn = self._get_connection()
        try:
            conn.row_factory = sqlite3.Row
            query = "SELECT * FROM medications WHERE id = ?"
            params = [medication_id]
            if tenant_id:
                query += " AND tenant_id = ?"
                params.append(tenant_id)
            row = conn.execute(query, params).fetchone()
            return dict(row) if row else None
        finally:
            if not self._conn:
                conn.close()

    def update_medication(self, medication_id: int, name: str, dosage: str,
                          times: str, active_days: str = None,
                          tenant_id: int = None):
        conn = self._get_connection()
        try:
            query = "UPDATE medications SET name = ?, dosage = ?, times = ?"
            params = [name, dosage, times]
            if active_days is not None:
                query += ", active_days = ?"
                params.append(active_days)
            query += " WHERE id = ?"
            params.append(medication_id)
            if tenant_id:
                query += " AND tenant_id = ?"
                params.append(tenant_id)
            conn.execute(query, params)
            conn.commit()
        finally:
            if not self._conn:
                conn.close()

    def delete_medication(self, medication_id: int, tenant_id: int = None):
        conn = self._get_connection()
        try:
            query = "DELETE FROM medications WHERE id = ?"
            params = [medication_id]
            if tenant_id:
                query += " AND tenant_id = ?"
                params.append(tenant_id)
            conn.execute(query, params)
            conn.commit()
        finally:
            if not self._conn:
                conn.close()

    def log_medication(self, medication_id: int, status: str,
                       scheduled_time: str = None, reminder_count: int = 0) -> int:
        conn = self._get_connection()
        try:
            cursor = conn.execute("""
                INSERT INTO medication_logs (medication_id, status, scheduled_time, reminder_count)
                VALUES (?, ?, ?, ?)
            """, (medication_id, status, scheduled_time, reminder_count))
            conn.commit()
            return cursor.lastrowid
        finally:
            if not self._conn:
                conn.close()

    # ── Stories ──

    def save_story(self, transcript: str, audio_s3_key: str = None,
                   speaker_name: str = None, source: str = "voice",
                   duration_seconds: float = None, user_id: int = None,
                   tenant_id: int = None, question_text: str = None,
                   photo_id: int = None, recorded_by_member_id: int = None) -> int:
        conn = self._get_connection()
        try:
            cursor = conn.execute("""
                INSERT INTO stories (user_id, transcript, audio_s3_key, speaker_name,
                                    source, duration_seconds, tenant_id, question_text,
                                    photo_id, recorded_by_member_id)
                VALUES (?, ?, ?, ?, ?, ?, ?, ?, ?, ?)
            """, (user_id, transcript, audio_s3_key, speaker_name, source,
                  duration_seconds, tenant_id, question_text, photo_id,
                  recorded_by_member_id))
            conn.commit()
            return cursor.lastrowid
        finally:
            if not self._conn:
                conn.close()

    def get_stories(self, user_id: int = None, limit: int = 50,
                    tenant_id: int = None, verified_only: bool = True,
                    exclude_private: bool = False) -> List[Dict]:
        conn = self._get_connection()
        try:
            conn.row_factory = sqlite3.Row
            query = "SELECT * FROM stories WHERE 1=1"
            params = []
            if verified_only:
                query += " AND verified = 1"
            if exclude_private:
                query += " AND (private = 0 OR private IS NULL)"
            if user_id:
                query += " AND user_id = ?"
                params.append(user_id)
            if tenant_id:
                query += " AND tenant_id = ?"
                params.append(tenant_id)
            query += " ORDER BY created_at DESC LIMIT ?"
            params.append(limit)
            results = conn.execute(query, params).fetchall()
            rows = [dict(r) for r in results]
            # Convert UTC timestamps to local timezone for display
            try:
                from zoneinfo import ZoneInfo
                from datetime import datetime
                tz = ZoneInfo("America/Chicago")
                for row in rows:
                    if row.get("created_at"):
                        try:
                            dt = datetime.strptime(row["created_at"], "%Y-%m-%d %H:%M:%S")
                            dt_utc = dt.replace(tzinfo=ZoneInfo("UTC"))
                            dt_local = dt_utc.astimezone(tz)
                            row["created_at"] = dt_local.strftime("%Y-%m-%d %I:%M %p")
                        except (ValueError, TypeError):
                            pass
            except ImportError:
                pass
            return rows
        finally:
            if not self._conn:
                conn.close()

    # ── Question sessions ──

    def save_question_session(self, question_id: str, question_text: str,
                              answer_text: str = None, audio_s3_key: str = None,
                              week: int = None, theme: str = None,
                              user_id: int = None, tenant_id: int = None) -> int:
        conn = self._get_connection()
        try:
            cursor = conn.execute("""
                INSERT INTO question_sessions (user_id, question_id, question_text,
                    answer_text, audio_s3_key, week, theme, answered, tenant_id)
                VALUES (?, ?, ?, ?, ?, ?, ?, ?, ?)
            """, (user_id, question_id, question_text, answer_text, audio_s3_key,
                  week, theme, 1 if answer_text else 0, tenant_id))
            conn.commit()
            return cursor.lastrowid
        finally:
            if not self._conn:
                conn.close()

    # ── Bible verses ──

    def get_verse_by_day(self, day_of_year: int) -> Optional[Dict]:
        conn = self._get_connection()
        try:
            conn.row_factory = sqlite3.Row
            result = conn.execute(
                "SELECT * FROM bible_verses WHERE day_of_year = ?", (day_of_year,)
            ).fetchone()
            return dict(result) if result else None
        finally:
            if not self._conn:
                conn.close()

    def get_verse_by_topic(self, topic: str) -> Optional[Dict]:
        conn = self._get_connection()
        try:
            conn.row_factory = sqlite3.Row
            # Search by topic first, then fall back to reference (e.g., "Psalm", "Proverbs")
            result = conn.execute(
                "SELECT * FROM bible_verses WHERE topic LIKE ? ORDER BY RANDOM() LIMIT 1",
                (f"%{topic}%",)
            ).fetchone()
            if not result:
                result = conn.execute(
                    "SELECT * FROM bible_verses WHERE reference LIKE ? ORDER BY RANDOM() LIMIT 1",
                    (f"%{topic}%",)
                ).fetchone()
            return dict(result) if result else None
        finally:
            if not self._conn:
                conn.close()

    # ── Family members ──

    def add_family_member(self, name: str, relationship: str = None,
                          primary_user_id: int = None,
                          tenant_id: int = None) -> int:
        name_norm = self._normalize(name)
        conn = self._get_connection()
        try:
            t_clause = " AND tenant_id = ?" if tenant_id else ""
            t_params = (tenant_id,) if tenant_id else ()

            existing = conn.execute(
                f"SELECT id FROM family_members WHERE name_normalized = ?{t_clause}",
                (name_norm,) + t_params
            ).fetchone()
            if existing:
                conn.execute("""
                    UPDATE family_members SET visit_count = visit_count + 1,
                    last_seen = CURRENT_TIMESTAMP WHERE id = ?
                """, (existing[0],))
                if relationship:
                    conn.execute(
                        "UPDATE family_members SET relationship = ? WHERE id = ?",
                        (relationship, existing[0])
                    )
                conn.commit()
                return existing[0]
            cursor = conn.execute("""
                INSERT INTO family_members (name, name_normalized, relationship,
                                           primary_user_id, tenant_id)
                VALUES (?, ?, ?, ?, ?)
            """, (name, name_norm, relationship, primary_user_id, tenant_id))
            conn.commit()
            return cursor.lastrowid
        finally:
            if not self._conn:
                conn.close()

    def find_family_member(self, name: str, tenant_id: int = None) -> Optional[Dict]:
        name_norm = self._normalize(name)
        conn = self._get_connection()
        try:
            conn.row_factory = sqlite3.Row
            t_clause = " AND tenant_id = ?" if tenant_id else ""
            t_params = (tenant_id,) if tenant_id else ()

            result = conn.execute(
                f"SELECT * FROM family_members WHERE name_normalized = ?{t_clause}",
                (name_norm,) + t_params
            ).fetchone()
            if not result:
                result = conn.execute(
                    f"SELECT * FROM family_members WHERE name_normalized LIKE ?{t_clause}",
                    (f"%{name_norm}%",) + t_params
                ).fetchone()
            return dict(result) if result else None
        finally:
            if not self._conn:
                conn.close()

    def get_family_members(self, tenant_id: int = None) -> List[Dict]:
        conn = self._get_connection()
        try:
            conn.row_factory = sqlite3.Row
            if tenant_id:
                results = conn.execute(
                    "SELECT * FROM family_members WHERE tenant_id = ? ORDER BY last_seen DESC",
                    (tenant_id,)
                ).fetchall()
            else:
                results = conn.execute(
                    "SELECT * FROM family_members ORDER BY last_seen DESC"
                ).fetchall()
            return [dict(r) for r in results]
        finally:
            if not self._conn:
                conn.close()

    def update_family_member(self, member_id: int, name: str = None,
                             relationship: str = None, relation_to_owner: str = None,
                             parent_member_id: int = None, generation: int = None,
                             deceased: int = None, spouse_name: str = None,
                             bio: str = None, added_by: str = None,
                             birth_year: int = None,
                             deceased_year: int = None,
                             is_minor: int = None,
                             email: str = None) -> bool:
        conn = self._get_connection()
        try:
            updates = []
            params = []
            if name is not None:
                updates.append("name = ?")
                params.append(name)
                updates.append("name_normalized = ?")
                params.append(self._normalize(name))
            if relationship is not None:
                updates.append("relationship = ?")
                params.append(relationship)
            if relation_to_owner is not None:
                updates.append("relation_to_owner = ?")
                params.append(relation_to_owner)
            if parent_member_id is not None:
                updates.append("parent_member_id = ?")
                params.append(parent_member_id if parent_member_id > 0 else None)
            if generation is not None:
                updates.append("generation = ?")
                params.append(generation)
            if deceased is not None:
                updates.append("deceased = ?")
                params.append(deceased)
            if spouse_name is not None:
                updates.append("spouse_name = ?")
                params.append(spouse_name if spouse_name.strip() else None)
            if bio is not None:
                updates.append("bio = ?")
                params.append(bio if bio.strip() else None)
            if added_by is not None:
                updates.append("added_by = ?")
                params.append(added_by if added_by.strip() else None)
            if birth_year is not None:
                updates.append("birth_year = ?")
                params.append(birth_year if birth_year > 0 else None)
            if deceased_year is not None:
                updates.append("deceased_year = ?")
                params.append(deceased_year if deceased_year > 0 else None)
            if is_minor is not None:
                updates.append("is_minor = ?")
                params.append(is_minor)
            if email is not None:
                updates.append("email = ?")
                params.append(email.strip().lower() if email.strip() else None)
            if not updates:
                return False
            params.append(member_id)
            conn.execute(f"UPDATE family_members SET {', '.join(updates)} WHERE id = ?", params)
            conn.commit()
            return True
        finally:
            if not self._conn:
                conn.close()

    def get_family_member_by_id(self, member_id: int) -> Optional[Dict]:
        conn = self._get_connection()
        try:
            conn.row_factory = sqlite3.Row
            result = conn.execute("SELECT * FROM family_members WHERE id = ?", (member_id,)).fetchone()
            return dict(result) if result else None
        finally:
            if not self._conn:
                conn.close()

    def delete_family_member(self, member_id: int) -> bool:
        conn = self._get_connection()
        try:
            # Clear parent references pointing to this member
            conn.execute("UPDATE family_members SET parent_member_id = NULL WHERE parent_member_id = ?", (member_id,))
            conn.execute("DELETE FROM family_members WHERE id = ?", (member_id,))
            conn.commit()
            return True
        finally:
            if not self._conn:
                conn.close()

    def update_family_member_visit(self, member_id: int):
        conn = self._get_connection()
        try:
            conn.execute("""
                UPDATE family_members SET visit_count = visit_count + 1,
                last_seen = CURRENT_TIMESTAMP WHERE id = ?
            """, (member_id,))
            conn.commit()
        finally:
            if not self._conn:
                conn.close()

    def search_stories_by_speaker_or_topic(self, query: str, limit: int = 20,
                                           tenant_id: int = None) -> List[Dict]:
        query_norm = self._normalize(query)
        conn = self._get_connection()
        try:
            conn.row_factory = sqlite3.Row
            t_clause = " AND s.tenant_id = ?" if tenant_id else ""
            t_params = (tenant_id,) if tenant_id else ()
            results = conn.execute(f"""
                SELECT s.* FROM stories s
                LEFT JOIN story_tags st ON s.id = st.story_id
                WHERE (s.speaker_name LIKE ? OR s.transcript LIKE ?
                   OR st.tag_value LIKE ?) AND s.verified = 1{t_clause}
                GROUP BY s.id ORDER BY s.created_at DESC LIMIT ?
            """, (f"%{query_norm}%", f"%{query_norm}%", f"%{query_norm}%") + t_params + (limit,)).fetchall()
            return [dict(r) for r in results]
        finally:
            if not self._conn:
                conn.close()

    def add_story_tag(self, story_id: int, tag_type: str, tag_value: str,
                      tenant_id: int = None) -> int:
        conn = self._get_connection()
        try:
            cursor = conn.execute("""
                INSERT INTO story_tags (story_id, tag_type, tag_value, tenant_id)
                VALUES (?, ?, ?, ?)
            """, (story_id, tag_type, tag_value, tenant_id))
            conn.commit()
            return cursor.lastrowid
        finally:
            if not self._conn:
                conn.close()

    # ── Narrative log ──

    # ── Prayer requests ──

    def add_prayer_request(self, name: str, request: str = None,
                           tenant_id: int = None) -> int:
        conn = self._get_connection()
        try:
            cursor = conn.execute("""
                INSERT INTO prayer_requests (tenant_id, name, request)
                VALUES (?, ?, ?)
            """, (tenant_id, name, request))
            conn.commit()
            return cursor.lastrowid
        finally:
            if not self._conn:
                conn.close()

    def get_prayer_requests(self, tenant_id: int, active_only: bool = True) -> list:
        conn = self._get_connection()
        try:
            conn.row_factory = sqlite3.Row
            if active_only:
                rows = conn.execute(
                    "SELECT * FROM prayer_requests WHERE tenant_id = ? AND active = 1 ORDER BY created_at DESC",
                    (tenant_id,)
                ).fetchall()
            else:
                rows = conn.execute(
                    "SELECT * FROM prayer_requests WHERE tenant_id = ? ORDER BY created_at DESC",
                    (tenant_id,)
                ).fetchall()
            return [dict(r) for r in rows]
        finally:
            if not self._conn:
                conn.close()

    def delete_prayer_request(self, request_id: int):
        conn = self._get_connection()
        try:
            conn.execute("DELETE FROM prayer_requests WHERE id = ?", (request_id,))
            conn.commit()
        finally:
            if not self._conn:
                conn.close()

    # ── Prayer recordings ──
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
