Glen-collab/polly-connect/server/core/book_pdf.py

"""
PDF Book Generator for Polly Connect Legacy Books.

Generates a print-ready 6x9 inch PDF suitable for KDP, Lulu, IngramSpark.
Uses ReportLab for layout and qrcode for audio companion QR codes.

Trim: 6" x 9" (432 x 648 points)
Margins: gutter 0.85", outside 0.65", top 0.75", bottom 0.75"
Works for both softcover and hardcover binding.
"""

import io
import logging
import os
import textwrap
from typing import Dict, List, Optional

from reportlab.lib.pagesizes import inch
from reportlab.lib.styles import getSampleStyleSheet, ParagraphStyle
from reportlab.lib.enums import TA_CENTER, TA_LEFT, TA_JUSTIFY, TA_RIGHT
from reportlab.lib.colors import HexColor
from reportlab.platypus import (
    SimpleDocTemplate, Paragraph, Spacer, PageBreak, Image,
    Table, TableStyle, NextPageTemplate, PageTemplate, Frame,
    BaseDocTemplate,
)
from reportlab.lib.units import inch as INCH
from reportlab.pdfbase import pdfmetrics
from reportlab.pdfbase.ttfonts import TTFont

logger = logging.getLogger(__name__)

# ── Page dimensions (6x9 trim) ──

PAGE_WIDTH = 6 * INCH
PAGE_HEIGHT = 9 * INCH

# Margins (in inches) — KDP-safe for up to 300 pages
GUTTER = 0.85 * INCH       # inside margin (binding side)
OUTSIDE = 0.65 * INCH      # outside margin
TOP = 0.75 * INCH
BOTTOM = 0.75 * INCH

# Text area
TEXT_WIDTH = PAGE_WIDTH - GUTTER - OUTSIDE
TEXT_HEIGHT = PAGE_HEIGHT - TOP - BOTTOM

# QR code config
QR_SIZE = 0.8 * INCH
PHOTO_MAX_WIDTH = TEXT_WIDTH - 0.5 * INCH  # leave some margin
PHOTO_MAX_HEIGHT = 3.5 * INCH              # max height for inline photos
AUDIO_BASE_URL = "https://polly-connect.com/web/listen"
UPLOADS_DIR = os.path.join(os.path.dirname(os.path.dirname(os.path.dirname(__file__))), "server", "static", "uploads")

BUCKET_LABELS = {
    "ordinary_world": "Everyday Life",
    "call_to_adventure": "Turning Points",
    "crossing_threshold": "Big Decisions",
    "trials_allies_enemies": "Challenges & Helpers",
    "transformation": "How You Changed",
    "return_with_knowledge": "Wisdom & Lessons",
}

PHASE_LABELS = {
    "childhood": "Childhood",
    "adolescence": "Adolescence",
    "young_adult": "Young Adult",
    "adult": "Adult",
    "midlife": "Midlife",
    "elder": "Elder",
    "reflection": "Reflection",
}


def _build_styles():
    """Build custom paragraph styles for the book."""
    styles = getSampleStyleSheet()

    styles.add(ParagraphStyle(
        name='BookTitle',
        fontName='Times-Bold',
        fontSize=28,
        leading=34,
        alignment=TA_CENTER,
        spaceAfter=12,
        textColor=HexColor('#1a1a1a'),
    ))

    styles.add(ParagraphStyle(
        name='BookSubtitle',
        fontName='Times-Italic',
        fontSize=16,
        leading=20,
        alignment=TA_CENTER,
        spaceAfter=6,
        textColor=HexColor('#555555'),
    ))

    styles.add(ParagraphStyle(
        name='BookAuthor',
        fontName='Times-Roman',
        fontSize=14,
        leading=18,
        alignment=TA_CENTER,
        spaceBefore=24,
        spaceAfter=6,
        textColor=HexColor('#333333'),
    ))

    styles.add(ParagraphStyle(
        name='ChapterTitle',
        fontName='Times-Bold',
        fontSize=22,
        leading=28,
        alignment=TA_LEFT,
        spaceBefore=72,
        spaceAfter=24,
        textColor=HexColor('#1a1a1a'),
    ))

    styles.add(ParagraphStyle(
        name='ChapterSubhead',
        fontName='Times-Italic',
        fontSize=11,
        leading=14,
        alignment=TA_LEFT,
        spaceAfter=18,
        textColor=HexColor('#777777'),
    ))

    # Override the default BodyText style
    styles['BodyText'].fontName = 'Times-Roman'
    styles['BodyText'].fontSize = 11
    styles['BodyText'].leading = 15
    styles['BodyText'].alignment = TA_JUSTIFY
    styles['BodyText'].spaceBefore = 0
    styles['BodyText'].spaceAfter = 8
    styles['BodyText'].firstLineIndent = 18
    styles['BodyText'].textColor = HexColor('#1a1a1a')

    styles.add(ParagraphStyle(
        name='BodyFirst',
        fontName='Times-Roman',
        fontSize=11,
        leading=15,
        alignment=TA_JUSTIFY,
        spaceBefore=0,
        spaceAfter=8,
        firstLineIndent=0,  # first paragraph after heading: no indent
        textColor=HexColor('#1a1a1a'),
    ))

    styles.add(ParagraphStyle(
        name='QRCaption',
        fontName='Times-Italic',
        fontSize=8,
        leading=10,
        alignment=TA_CENTER,
        textColor=HexColor('#888888'),
    ))

    styles.add(ParagraphStyle(
        name='Dedication',
        fontName='Times-Italic',
        fontSize=13,
        leading=18,
        alignment=TA_CENTER,
        spaceBefore=120,
        textColor=HexColor('#333333'),
    ))

    styles.add(ParagraphStyle(
        name='TOCEntry',
        fontName='Times-Roman',
        fontSize=12,
        leading=20,
        alignment=TA_LEFT,
        textColor=HexColor('#1a1a1a'),
    ))

    styles.add(ParagraphStyle(
        name='TOCTitle',
        fontName='Times-Bold',
        fontSize=18,
        leading=24,
        alignment=TA_CENTER,
        spaceBefore=48,
        spaceAfter=24,
        textColor=HexColor('#1a1a1a'),
    ))

    styles.add(ParagraphStyle(
        name='Footer',
        fontName='Times-Roman',
        fontSize=9,
        leading=12,
        alignment=TA_CENTER,
        textColor=HexColor('#999999'),
    ))

    return styles


def _generate_qr_image(url: str, size_px: int = 120) -> Optional[io.BytesIO]:
    """Generate a QR code as an in-memory PNG image."""
    try:
        import qrcode
        qr = qrcode.QRCode(
            version=1,
            error_correction=qrcode.constants.ERROR_CORRECT_M,
            box_size=4,
            border=1,
        )
        qr.add_data(url)
        qr.make(fit=True)
        img = qr.make_image(fill_color="black", back_color="white")

        buf = io.BytesIO()
        img.save(buf, format='PNG')
        buf.seek(0)
        return buf
    except Exception as e:
        logger.warning(f"QR generation failed: {e}")
        return None


def _qr_label(story: dict, limit: int, use_text: bool = True) -> str:
    """Caption under a story's QR code: its title/question, else the start of
    what was said, else — for audio-only moments (kids playing, Christmas
    chaos) — the date it was recorded."""
    title = (story.get("question_text") or "").strip()
    if title:
        return title
    text = ((story.get("corrected_transcript") or "").strip()
            or (story.get("transcript") or "").strip())
    if use_text and text and not text.startswith("(no transcription"):
        return text[:limit].strip() + ("..." if len(text) > limit else "")
    from datetime import datetime
    try:
        when = datetime.strptime((story.get("created_at") or "")[:10], "%Y-%m-%d")
        return f"Voice recording, {when.strftime('%b')} {when.day}, {when.year}"
    except ValueError:
        return "Voice recording"


class LegacyBookPDF:
    """Generates a print-ready 6x9 PDF for a family legacy book."""

    def __init__(self, db, book_builder, tenant_id: int = None):
        self.db = db
        self.book_builder = book_builder
        self.tenant_id = tenant_id
        self.styles = _build_styles()
        self._page_count = 0

    def generate(self, speaker_name: str = None,
                 book_title: str = None,
                 subtitle: str = None,
                 dedication: str = None,
                 include_qr_codes: bool = True) -> bytes:
        """
        Generate the full book PDF.

        Returns PDF bytes ready for download/print.
        """
        buf = io.BytesIO()

        # Get chapters and drafts — use tenant_id only (speaker filter can miss mismatched names)
        chapters = self.book_builder.generate_chapter_outline(tenant_id=self.tenant_id)
        drafts = self.db.get_chapter_drafts(tenant_id=self.tenant_id)

        # Every chapter prints. Drafts attach by shared memories (not by
        # chapter number, which shifts as stories are added); whatever a
        # draft's prose doesn't cover prints verbatim after it.
        self.book_builder.match_drafts(chapters, drafts)
        # Skip only chapters with nothing left to say (every memory already
        # told in another chapter's prose); number the rest consecutively.
        printable = [ch for ch in chapters if ch["draft"] or ch["uncovered_ids"]]
        for i, ch in enumerate(printable, 1):
            ch["print_number"] = i
        for ch in printable:
            if ch["draft"]:
                # Photo/QR lookups cover both the chapter's memories and any
                # the draft's prose still references.
                import json as _json
                try:
                    draft_mids = _json.loads(ch["draft"].get("memory_ids") or "[]")
                except (ValueError, TypeError):
                    draft_mids = []
                ch["media_memory_ids"] = list(dict.fromkeys(ch["memory_ids"] + draft_mids))

        # Determine title
        if not book_title:
            if speaker_name:
                book_title = f"The Story of {speaker_name}"
            else:
                book_title = "A Family Legacy"

        if not subtitle:
            subtitle = "Stories, Memories, and Wisdom"

        # Build document
        doc = SimpleDocTemplate(
            buf,
            pagesize=(PAGE_WIDTH, PAGE_HEIGHT),
            topMargin=TOP,
            bottomMargin=BOTTOM,
            leftMargin=GUTTER,
            rightMargin=OUTSIDE,
        )

        story = []

        # ── Title Page ──
        story.append(Spacer(1, 120))
        story.append(Paragraph(book_title, self.styles['BookTitle']))
        story.append(Spacer(1, 12))
        story.append(Paragraph(subtitle, self.styles['BookSubtitle']))
        if speaker_name:
            story.append(Paragraph(f"As told by {speaker_name}", self.styles['BookAuthor']))
        story.append(Spacer(1, 48))
        story.append(Paragraph(
            "Captured and preserved by Polly Connect",
            self.styles['BookSubtitle'],
        ))
        story.append(PageBreak())

        # ── Copyright / blank page ──
        story.append(Spacer(1, 300))
        story.append(Paragraph(
            f"Copyright &copy; 2026. All rights reserved.",
            ParagraphStyle(
                name='Copyright',
                fontName='Times-Roman',
                fontSize=9,
                leading=12,
                alignment=TA_CENTER,
                textColor=HexColor('#999999'),
            ),
        ))
        story.append(Spacer(1, 6))
        story.append(Paragraph(
            "This book was created using Polly Connect, a voice-powered<br/>"
            "family legacy preservation system. The stories within were<br/>"
            "spoken aloud and captured in the storyteller's own words.",
            ParagraphStyle(
                name='CopyrightBody',
                fontName='Times-Italic',
                fontSize=8,
                leading=11,
                alignment=TA_CENTER,
                textColor=HexColor('#aaaaaa'),
            ),
        ))
        story.append(PageBreak())

        # ── Dedication (optional) ──
        if dedication:
            story.append(Paragraph(dedication, self.styles['Dedication']))
            story.append(PageBreak())

        # ── Table of Contents ──
        story.append(Paragraph("Contents", self.styles['TOCTitle']))
        for ch in printable:
            entry = f"Chapter {ch['print_number']}:&nbsp;&nbsp;&nbsp;{ch['title']}"
            story.append(Paragraph(entry, self.styles['TOCEntry']))
        if self.tenant_id and self.book_builder.appendix_stories(self.tenant_id):
            story.append(Paragraph("Appendix", self.styles['TOCEntry']))
        story.append(PageBreak())

        # ── Chapters ──
        # Track globally used photos and audio to avoid duplicates across chapters
        global_used_photos = set()
        global_used_audio = set()
        for ch in printable:
            # Chapter heading
            story.append(Paragraph(
                f"Chapter {ch['print_number']}",
                ParagraphStyle(
                    name='ChapterNum',
                    fontName='Times-Roman',
                    fontSize=12,
                    leading=16,
                    alignment=TA_LEFT,
                    spaceBefore=72,
                    spaceAfter=4,
                    textColor=HexColor('#999999'),
                ),
            ))
            story.append(Paragraph(ch['title'], self.styles['ChapterTitle']))

            # Bucket / phase subtitle
            bucket_label = BUCKET_LABELS.get(ch.get('bucket', ''), '')
            phase_label = PHASE_LABELS.get(ch.get('life_phase', ''), '')
            if bucket_label or phase_label:
                subhead = " — ".join(filter(None, [bucket_label, phase_label]))
                story.append(Paragraph(subhead, self.styles['ChapterSubhead']))

            # Build media lookup for inline photo placement
            media_by_story = self._get_chapter_media_by_story(
                ch, global_used_photos, global_used_audio
            )
            # Also build lookup for unlinked photos (PHOTO:p123 markers)
            media_by_photo_id = {}
            if self.tenant_id:
                try:
                    conn = self.db._get_connection()
                    unlinked = conn.execute("""
                        SELECT id, filename, caption FROM photos
                        WHERE tenant_id = ? AND in_book = 1
                        AND (story_id IS NULL OR story_id = 0)
                        AND id NOT IN (SELECT COALESCE(photo_id,0) FROM stories WHERE tenant_id = ?)
                    """, (self.tenant_id, self.tenant_id)).fetchall()
                    for up in unlinked:
                        pid = up[0]
                        if pid in global_used_photos:
                            continue
                        fname = up[1]
                        for base in [UPLOADS_DIR,
                                     os.path.join(os.path.dirname(__file__), "..", "static", "uploads"),
                                     os.path.join(os.path.dirname(__file__), "..", "static", "photos"),
                                     "server/static/uploads", "server/static/photos"]:
                            path = os.path.join(base, fname)
                            if os.path.exists(path):
                                media_by_photo_id[pid] = {
                                    "story_id": None,
                                    "photo_id": pid,
                                    "photo_path": path,
                                    "photo_caption": up[2] or "",
                                }
                                break
                except Exception:
                    pass
            placed_stories = set()

            # Chapter body
            draft = ch.get("draft")
            if draft and draft.get("content"):
                # AI-generated chapter draft — parse [PHOTO:story_id] markers
                import re
                paragraphs = draft["content"].split("\n\n")
                body_para_idx = 0
                for para in paragraphs:
                    para = para.strip()
                    if not para:
                        continue

                    # Check for inline photo marker: [PHOTO:123] or [PHOTO:p123]
                    photo_match = re.match(r'^\[PHOTO:(p?)(\d+)\]$', para)
                    if photo_match:
                        is_photo_id = photo_match.group(1) == 'p'
                        num = int(photo_match.group(2))
                        if is_photo_id and num in media_by_photo_id:
                            self._render_media_item(
                                story, media_by_photo_id[num],
                                include_qr_codes, placed_stories
                            )
                            global_used_photos.add(num)
                        elif not is_photo_id and num in media_by_story:
                            self._render_media_item(
                                story, media_by_story[num],
                                include_qr_codes, placed_stories
                            )
                        continue

                    # Strip any rogue photo markers GPT invented
                    # (e.g. [PHOTO: Memory 1], [PHOTO: 5], etc.)
                    if re.match(r'^\[PHOTO[:\s].*\]$', para, re.IGNORECASE):
                        continue

                    # Check if paragraph contains embedded markers mixed with text
                    # Split on valid markers and render text + photos in order
                    parts = re.split(r'\[PHOTO:(p?\d+)\]', para)
                    if len(parts) > 1:
                        for j, part in enumerate(parts):
                            if j % 2 == 0:
                                # Text part — also strip rogue markers
                                text = re.sub(r'\[PHOTO[:\s][^\]]*\]', '', part).strip()
                                if text:
                                    text = text.replace("&", "&amp;").replace("<", "&lt;").replace(">", "&gt;")
                                    style = self.styles['BodyFirst'] if body_para_idx == 0 else self.styles['BodyText']
                                    story.append(Paragraph(text, style))
                                    body_para_idx += 1
                            else:
                                # Photo marker part (e.g. "123" or "p123")
                                if part.startswith('p'):
                                    pid = int(part[1:])
                                    if pid in media_by_photo_id:
                                        self._render_media_item(
                                            story, media_by_photo_id[pid],
                                            include_qr_codes, placed_stories
                                        )
                                        global_used_photos.add(pid)
                                else:
                                    sid = int(part)
                                    if sid in media_by_story:
                                        self._render_media_item(
                                            story, media_by_story[sid],
                                            include_qr_codes, placed_stories
                                        )
                    else:
                        # Normal paragraph — strip rogue markers, then render
                        para = re.sub(r'\[PHOTO[:\s][^\]]*\]', '', para).strip()
                        if not para:
                            continue
                        para = para.replace("&", "&amp;").replace("<", "&lt;").replace(">", "&gt;")
                        style = self.styles['BodyFirst'] if body_para_idx == 0 else self.styles['BodyText']
                        story.append(Paragraph(para, style))
                        body_para_idx += 1

            # Memories not told in the draft prose (no draft yet, added since
            # drafting, or skipped by the AI) print in the speaker's own words.
            memories = []
            for mid in ch.get("uncovered_ids", []):
                mem = self.db.get_memory_by_id(mid, tenant_id=self.tenant_id)
                if mem:
                    memories.append(mem)

            if memories or not (draft and draft.get("content")):
                if draft and draft.get("content"):
                    story.append(Spacer(1, 12))
                    story.append(Paragraph("More from this chapter", self.styles['ChapterSubhead']))
                if memories:
                    for i, mem in enumerate(memories):
                        text = self._verbatim_text(mem)
                        if not text:
                            continue
                        text = text.replace("&", "&amp;").replace("<", "&lt;").replace(">", "&gt;")
                        speaker = mem.get("speaker", "")
                        if speaker:
                            text = f"<i>{speaker}:</i> {text}"
                        style = self.styles['BodyFirst'] if i == 0 else self.styles['BodyText']
                        story.append(Paragraph(text, style))
                        story.append(Spacer(1, 4))

                        # Inline photo for this memory (by story_id)
                        sid = mem.get("story_id")
                        if sid and sid in media_by_story:
                            self._render_media_item(
                                story, media_by_story[sid],
                                include_qr_codes, placed_stories
                            )
                else:
                    story.append(Paragraph(
                        "<i>This chapter is still being written...</i>",
                        self.styles['BodyFirst'],
                    ))

            # Render any remaining photos that weren't placed inline
            # (fallback for photos GPT didn't place or old drafts without markers)
            unplaced = [
                v for sid, v in media_by_story.items()
                if sid not in placed_stories
            ]
            if unplaced:
                story.append(Spacer(1, 18))
                for item in unplaced:
                    self._render_media_item(
                        story, item, include_qr_codes, placed_stories
                    )

            story.append(PageBreak())

        # ── Appendix — stories not ✔ verified yet ──
        # Kept, never dropped: the real voice (QR) with a title or date, but
        # not the unchecked transcript. Typed stories print as typed.
        appendix = self.book_builder.appendix_stories(self.tenant_id) if self.tenant_id else []
        if appendix:
            story.append(Paragraph("Appendix", self.styles['TOCTitle']))
            story.append(Paragraph(
                "More recordings, kept just as they were captured.",
                self.styles['ChapterSubhead'],
            ))
            for s in appendix:
                audio_key = s.get("audio_s3_key")
                speaker = (s.get("speaker_name") or "").strip()
                if audio_key:
                    label = _qr_label(s, 60, use_text=False)
                    if speaker:
                        label = f"{speaker}: {label}"
                    label = label.replace("&", "&amp;").replace("<", "&lt;").replace(">", "&gt;")
                    qr_buf = _generate_qr_image(f"{AUDIO_BASE_URL}/{audio_key}") if include_qr_codes else None
                    if qr_buf:
                        t = Table([[Image(qr_buf, width=QR_SIZE, height=QR_SIZE),
                                    Paragraph(label, self.styles['BodyFirst'])]],
                                  colWidths=[QR_SIZE + 12, TEXT_WIDTH - QR_SIZE - 12])
                        t.setStyle(TableStyle([('VALIGN', (0, 0), (-1, -1), 'MIDDLE')]))
                        story.append(t)
                        story.append(Spacer(1, 10))
                    else:
                        story.append(Paragraph(label, self.styles['BodyFirst']))
                    global_used_audio.add(audio_key)
                else:
                    text = ((s.get("corrected_transcript") or "").strip()
                            or (s.get("transcript") or "").strip())
                    text = text.replace("&", "&amp;").replace("<", "&lt;").replace(">", "&gt;")
                    if speaker:
                        text = f"<i>{speaker}:</i> {text}"
                    story.append(Paragraph(text, self.styles['BodyText']))
            story.append(PageBreak())

        # ── Audio Index — orphaned QR codes (no inline photo) ──
        if include_qr_codes:
            orphan_qrs = self._get_orphan_audio(
                printable, global_used_audio, global_used_photos
            )
            if orphan_qrs:
                story.append(Paragraph("Voice Recordings", self.styles['TOCTitle']))
                story.append(Paragraph(
                    "Scan any code below to hear the original voice recording.",
                    ParagraphStyle(
                        name='IndexIntro',
                        fontName='Times-Italic',
                        fontSize=10,
                        leading=14,
                        alignment=TA_CENTER,
                        spaceAfter=18,
                        textColor=HexColor('#777777'),
                    ),
                ))

                # Render QR codes in a grid-like layout, 2 per row
                row_items = []
                for oq in orphan_qrs:
                    audio_url = f"{AUDIO_BASE_URL}/{oq['audio_key']}"
                    qr_buf = _generate_qr_image(audio_url)
                    if not qr_buf:
                        continue

                    # Build a mini block: QR + label with speaker name
                    qr_img = Image(qr_buf, width=QR_SIZE, height=QR_SIZE)
                    speaker = oq.get("speaker") or ""
                    label = oq.get("label") or "Voice Recording"
                    # Escape for ReportLab
                    label = label.replace("&", "&amp;").replace("<", "&lt;").replace(">", "&gt;")
                    speaker = speaker.replace("&", "&amp;").replace("<", "&lt;").replace(">", "&gt;")
                    if speaker:
                        formatted = f"<b>{speaker}</b>: <i>{label}</i>"
                    else:
                        formatted = f"<i>{label}</i>"

                    row_items.append((qr_img, formatted))

                # Render 2 per row using a table
                for i in range(0, len(row_items), 2):
                    pair = row_items[i:i+2]
                    if len(pair) == 2:
                        table_data = [[pair[0][0], pair[1][0]],
                                      [Paragraph(pair[0][1], self.styles['QRCaption']),
                                       Paragraph(pair[1][1], self.styles['QRCaption'])]]
                    else:
                        table_data = [[pair[0][0], ""],
                                      [Paragraph(pair[0][1], self.styles['QRCaption']), ""]]

                    col_w = TEXT_WIDTH / 2
                    t = Table(table_data, colWidths=[col_w, col_w])
                    t.setStyle(TableStyle([
                        ('ALIGN', (0, 0), (-1, -1), 'CENTER'),
                        ('VALIGN', (0, 0), (-1, -1), 'TOP'),
                        ('BOTTOMPADDING', (0, 0), (-1, 0), 6),
                        ('TOPPADDING', (0, 1), (-1, 1), 2),
                        ('BOTTOMPADDING', (0, 1), (-1, 1), 14),
                    ]))
                    story.append(t)

                story.append(PageBreak())

        # ── Back matter ──
        story.append(Spacer(1, 120))
        story.append(Paragraph(
            "This book was created with love by Polly Connect.",
            self.styles['Dedication'],
        ))
        story.append(Spacer(1, 24))
        story.append(Paragraph(
            "Every story matters. Every voice deserves to be heard.",
            ParagraphStyle(
                name='BackMatter',
                fontName='Times-Italic',
                fontSize=11,
                leading=15,
                alignment=TA_CENTER,
                textColor=HexColor('#777777'),
            ),
        ))

        # Build PDF
        try:
            doc.build(story, onFirstPage=self._page_header_footer,
                      onLaterPages=self._page_header_footer)
        except Exception as e:
            logger.error(f"PDF generation failed: {e}")
            # Try without the import that might fail
            try:
                doc.build(story)
            except Exception as e2:
                logger.error(f"PDF generation failed completely: {e2}")
                raise

        return buf.getvalue()

    def _verbatim_text(self, mem: dict) -> str:
        """The memory in the speaker's own words, as last edited.

        memories.text is a copy taken at save time; edits land on the story's
        corrected_transcript, so prefer that (same order the chapter writer uses).
        """
        sid = mem.get("story_id")
        if sid:
            story = self.db.get_story_by_id(sid, tenant_id=self.tenant_id)
            if story:
                text = (story.get("corrected_transcript") or "").strip() or (story.get("transcript") or "").strip()
                if text and not text.startswith("(no transcription"):
                    return text
        return (mem.get("text") or mem.get("text_summary") or "").strip()

    def _page_header_footer(self, canvas, doc):
        """Add page numbers to each page."""
        self._page_count += 1
        page_num = self._page_count

        # Skip page number on title page and copyright
        if page_num <= 2:
            return

        canvas.saveState()
        canvas.setFont('Times-Roman', 9)
        canvas.setFillColor(HexColor('#999999'))

        # Page number centered at bottom
        canvas.drawCentredString(
            PAGE_WIDTH / 2,
            BOTTOM - 20,
            str(page_num),
        )
        canvas.restoreState()

    def _get_chapter_photos(self, chapter: dict) -> List[dict]:
        """Get photos linked to stories in this chapter."""
        photos = []
        seen_ids = set()
        for mid in (chapter.get("media_memory_ids") or chapter.get("memory_ids", [])):
            mem = self.db.get_memory_by_id(mid, tenant_id=self.tenant_id)
            if mem and mem.get("story_id"):
                story = self.db.get_story_by_id(mem["story_id"], tenant_id=self.tenant_id)
                if story and story.get("photo_id") and story.get("photo_in_book", 1):
                    pid = story["photo_id"]
                    if pid in seen_ids:
                        continue
                    seen_ids.add(pid)
                    photo = self.db.get_photo_by_id(pid, tenant_id=self.tenant_id)
                    if photo and photo.get("filename") and photo.get("in_book", 1):
                        # Try multiple possible upload directories
                        for base in [UPLOADS_DIR,
                                     os.path.join(os.path.dirname(__file__), "..", "static", "uploads"),
                                     "server/static/uploads"]:
                            path = os.path.join(base, photo["filename"])
                            if os.path.exists(path):
                                photos.append({
                                    "path": path,
                                    "caption": photo.get("caption", ""),
                                    "date_taken": photo.get("date_taken", ""),
                                })
                                break
        return photos

    def _get_chapter_audio_entries(self, chapter: dict) -> List[dict]:
        """Get audio entries for memories in a chapter, filtered by qr_in_book."""
        entries = []
        seen_keys = set()
        for mid in (chapter.get("media_memory_ids") or chapter.get("memory_ids", [])):
            mem = self.db.get_memory_by_id(mid, tenant_id=self.tenant_id)
            if mem and mem.get("story_id"):
                story = self.db.get_story_by_id(mem["story_id"], tenant_id=self.tenant_id)
                if (story and story.get("audio_s3_key")
                        and story.get("qr_in_book", 1)
                        and story["audio_s3_key"] not in seen_keys):
                    seen_keys.add(story["audio_s3_key"])
                    entries.append({
                        "audio_key": story["audio_s3_key"],
                        "speaker": story.get("speaker_name", ""),
                    })
        return entries

    def _render_media_item(self, story: list, item: dict,
                           include_qr_codes: bool,
                           placed_stories: set):
        """Render a single photo+QR media item into the PDF story flow."""
        story_id = item.get("story_id")
        if story_id in placed_stories:
            return
        placed_stories.add(story_id)

        story.append(Spacer(1, 10))
        photo_path = item.get("photo_path")
        if photo_path and os.path.exists(photo_path):
            try:
                img = Image(photo_path)
                iw, ih = img.drawWidth, img.drawHeight
                if iw > 0 and ih > 0:
                    scale = min(PHOTO_MAX_WIDTH / iw, PHOTO_MAX_HEIGHT / ih, 1.0)
                    img.drawWidth = iw * scale
                    img.drawHeight = ih * scale
                img.hAlign = 'CENTER'
                story.append(img)
                cap = item.get("photo_caption", "")
                if cap:
                    story.append(Paragraph(cap, self.styles['QRCaption']))
            except Exception as e:
                logger.warning(f"Failed to embed photo: {e}")

        if include_qr_codes and item.get("audio_key"):
            # If this item has a photo, use photo listen page (shows all voices)
            # Otherwise use individual audio listen page
            photo_id = item.get("photo_id")
            if photo_id:
                qr_url = f"https://polly-connect.com/web/photo-listen/{photo_id}"
            else:
                qr_url = f"{AUDIO_BASE_URL}/{item['audio_key']}"
            qr_buf = _generate_qr_image(qr_url)
            if qr_buf:
                story.append(Spacer(1, 6))
                img = Image(qr_buf, width=QR_SIZE, height=QR_SIZE)
                story.append(img)
                photo_id = item.get("photo_id")
                speaker = item.get('speaker', '')
                label = item.get('qr_label', '')
                if label:
                    label = label.replace("&", "&amp;").replace("<", "&lt;").replace(">", "&gt;")
                if photo_id:
                    # Photo QR — may have multiple voices
                    photo_caption = item.get("photo_caption", "")
                    if photo_caption:
                        photo_caption = photo_caption.replace("&", "&amp;").replace("<", "&lt;").replace(">", "&gt;")
                        qr_caption = f"Hear the family talk about this photo"
                    else:
                        qr_caption = "Scan to hear family memories about this photo"
                elif speaker and label:
                    qr_caption = f"<b>{speaker}</b>: <i>{label}</i>"
                elif speaker:
                    qr_caption = f"Hear {speaker}'s voice"
                elif label:
                    qr_caption = f"<i>{label}</i>"
                else:
                    qr_caption = "Scan to hear the original voice recording"
                story.append(Paragraph(qr_caption, self.styles['QRCaption']))
        story.append(Spacer(1, 10))

    def _get_chapter_media_by_story(self, chapter: dict,
                                     global_used_photos: set,
                                     global_used_audio: set) -> dict:
        """Get media items keyed by story_id for inline placement.

        Returns dict of story_id -> media item (photo_path, caption, audio_key, etc.)
        Each photo/QR appears only once across the entire book (globally deduplicated).
        """
        items = {}
        seen_stories = set()

        for mid in (chapter.get("media_memory_ids") or chapter.get("memory_ids", [])):
            mem = self.db.get_memory_by_id(mid, tenant_id=self.tenant_id)
            if not mem or not mem.get("story_id"):
                continue
            story_id = mem["story_id"]
            if story_id in seen_stories:
                continue
            seen_stories.add(story_id)

            story = self.db.get_story_by_id(story_id, tenant_id=self.tenant_id)
            if not story:
                continue

            item = {"story_id": story_id, "photo_id": story.get("photo_id")}
            has_content = False

            # Check photo
            photo_id = story.get("photo_id")
            if (photo_id and photo_id not in global_used_photos
                    and story.get("photo_in_book", 1)):
                photo = self.db.get_photo_by_id(photo_id, tenant_id=self.tenant_id)
                if photo and photo.get("filename"):
                    for base in [UPLOADS_DIR,
                                 os.path.join(os.path.dirname(__file__), "..", "static", "uploads"),
                                 "server/static/uploads"]:
                        path = os.path.join(base, photo["filename"])
                        if os.path.exists(path):
                            item["photo_path"] = path
                            item["photo_caption"] = photo.get("caption", "")
                            global_used_photos.add(photo_id)
                            has_content = True
                            break

            # Check audio/QR
            audio_key = story.get("audio_s3_key")
            if (audio_key and audio_key not in global_used_audio
                    and story.get("qr_in_book", 1)):
                item["audio_key"] = audio_key
                # Get speaker from memory
                speaker = ""
                mem_row = self.db._get_connection().execute(
                    "SELECT speaker FROM memories WHERE story_id = ? LIMIT 1",
                    (story_id,)
                ).fetchone()
                if mem_row:
                    speaker = mem_row[0] or ""
                item["speaker"] = speaker or (story.get("speaker_name") or "").strip()
                item["qr_label"] = _qr_label(story, 50)
                global_used_audio.add(audio_key)
                has_content = True

            if has_content:
                items[story_id] = item

        return items

    def _get_orphan_audio(self, chapters: list,
                          global_used_audio: set,
                          global_used_photos: set) -> list:
        """Get audio recordings not already placed inline with photos.

        These are QR codes for stories that either:
        - Have no photo attached
        - Have their photo toggled off (photo_in_book=0)
        - Were not placed inline by GPT

        Returns list of dicts with audio_key, speaker, label (story description).
        """
        orphans = []
        seen_audio = set(global_used_audio)  # copy — don't mutate the original

        # Walk ALL memories across all chapters
        all_memory_ids = set()
        for ch in chapters:
            for mid in (ch.get("media_memory_ids") or ch.get("memory_ids", [])):
                all_memory_ids.add(mid)

        # Also get ALL stories for this tenant that have audio
        # (some stories may not be in any chapter yet)
        conn = self.db._get_connection()
        try:
            import sqlite3
            conn.row_factory = sqlite3.Row
            all_stories = conn.execute(
                "SELECT s.id, s.audio_s3_key, s.qr_in_book, s.photo_id, s.photo_in_book, "
                "s.question_text, s.transcript, s.corrected_transcript, s.speaker_name, s.created_at "
                "FROM stories s WHERE s.tenant_id = ? AND s.audio_s3_key IS NOT NULL "
                "ORDER BY s.created_at, s.id",
                (self.tenant_id,)
            ).fetchall()
        finally:
            if not self.db._conn:
                conn.close()

        for s in all_stories:
            s = dict(s)
            audio_key = s.get("audio_s3_key")
            if not audio_key or audio_key in seen_audio:
                continue
            if not s.get("qr_in_book", 1):
                continue

            # Get speaker from memory
            mem = None
            conn = self.db._get_connection()
            try:
                mem = conn.execute(
                    "SELECT speaker, COALESCE(include_in_book, 1) FROM memories WHERE story_id = ? LIMIT 1",
                    (s["id"],)
                ).fetchone()
            finally:
                if not self.db._conn:
                    conn.close()
            if mem and not mem[1]:
                continue  # taken out of the book with 📖 — its QR goes too

            speaker = (mem[0] if mem else "") or (s.get("speaker_name") or "").strip()
            label = _qr_label(s, 60)

            seen_audio.add(audio_key)
            orphans.append({
                "audio_key": audio_key,
                "speaker": speaker,
                "label": label,
            })

        return orphans

    def _get_chapter_media(self, chapter: dict,
                           global_used_photos: set,
                           global_used_audio: set) -> List[dict]:
        """Get paired photo+QR media items for a chapter, globally deduplicated.

        Each photo and QR code appears only ONCE across the entire book.
        When a story has both a photo and audio, they are paired together
        (photo above, QR underneath). Returns list of media items.
        """
        items = []
        seen_stories = set()

        for mid in (chapter.get("media_memory_ids") or chapter.get("memory_ids", [])):
            mem = self.db.get_memory_by_id(mid, tenant_id=self.tenant_id)
            if not mem or not mem.get("story_id"):
                continue
            story_id = mem["story_id"]
            if story_id in seen_stories:
                continue
            seen_stories.add(story_id)

            story = self.db.get_story_by_id(story_id, tenant_id=self.tenant_id)
            if not story:
                continue

            item = {}
            has_content = False

            # Check photo
            photo_id = story.get("photo_id")
            if (photo_id and photo_id not in global_used_photos
                    and story.get("photo_in_book", 1)):
                photo = self.db.get_photo_by_id(photo_id, tenant_id=self.tenant_id)
                if photo and photo.get("filename") and photo.get("in_book", 1):
                    for base in [UPLOADS_DIR,
                                 os.path.join(os.path.dirname(__file__), "..", "static", "uploads"),
                                 "server/static/uploads"]:
                        path = os.path.join(base, photo["filename"])
                        if os.path.exists(path):
                            item["photo_path"] = path
                            item["photo_caption"] = photo.get("caption", "")
                            global_used_photos.add(photo_id)
                            has_content = True
                            break

            # Check audio/QR
            audio_key = story.get("audio_s3_key")
            if (audio_key and audio_key not in global_used_audio
                    and story.get("qr_in_book", 1)):
                item["audio_key"] = audio_key
                item["speaker"] = story.get("speaker_name", "")
                global_used_audio.add(audio_key)
                has_content = True

            if has_content:
                items.append(item)

        return items
