Glen-collab/polly-connect/server/core/notify.py

"""Email notifications for Polly Connect."""

import logging
import smtplib
from email.mime.text import MIMEText
from email.mime.multipart import MIMEMultipart

logger = logging.getLogger(__name__)


def send_notification(subject: str, body: str, to_email: str = None):
    """Send an email notification. Defaults to admin if no to_email specified."""
    from config import settings

    if not settings.GMAIL_APP_PASSWORD:
        logger.warning("GMAIL_APP_PASSWORD not set — skipping email notification")
        return False

    recipient = to_email or settings.NOTIFY_EMAIL
    msg = MIMEMultipart("alternative")
    msg["From"] = f"Polly Connect <{settings.GMAIL_USER}>"
    msg["To"] = recipient
    msg["Subject"] = subject
    msg.attach(MIMEText(body, "html"))

    try:
        with smtplib.SMTP_SSL("smtp.gmail.com", 465) as server:
            server.login(settings.GMAIL_USER, settings.GMAIL_APP_PASSWORD)
            server.send_message(msg)
        logger.info(f"Notification sent: {subject}")
        return True
    except Exception as e:
        logger.error(f"Failed to send notification: {e}")
        return False


def send_chatter_post_notification(poster_name: str, group_name: str, snippet: str,
                                   to_email: str, group_url: str, optout_url: str):
    """Email an away group member that someone posted in their Chatter group.
    The opt-out is scoped clearly to the email — not to leaving the group."""
    from markupsafe import escape
    # Plain-text subject: strip CR/LF to prevent email-header injection.
    s_poster = (poster_name or "").replace("\n", " ").replace("\r", " ")
    s_group = (group_name or "").replace("\n", " ").replace("\r", " ")
    subject = f"\U0001F4AC {s_poster} posted in {s_group} on Polly"
    # HTML body: escape all user-controlled values to prevent HTML/phishing injection.
    e_poster = escape(poster_name or "")
    e_group = escape(group_name or "")
    e_snippet = escape(snippet or "")
    body = f"""
    <div style="font-family: sans-serif; max-width: 500px; margin: 0 auto;">
        <h2 style="color: #ea580c; margin-bottom: 4px;">New message in {e_group}</h2>
        <p style="font-size: 15px; color: #333; margin-top: 0;"><strong>{e_poster}</strong> just posted:</p>
        <div style="background: #fff7ed; border-left: 4px solid #fb923c; padding: 12px 16px; border-radius: 6px; color: #444; font-size: 15px;">{e_snippet}</div>
        <p style="margin: 24px 0;">
            <a href="{group_url}" style="background: #ea580c; color: #fff; padding: 12px 24px; border-radius: 8px; text-decoration: none; font-weight: bold; display: inline-block;">Open the conversation</a>
        </p>
        <p style="color: #999; font-size: 12px; margin-top: 28px; border-top: 1px solid #eee; padding-top: 12px;">
            You're getting this because you're in the &ldquo;{e_group}&rdquo; group on Polly.
            <a href="{optout_url}" style="color: #999;">Turn off &ldquo;email me when someone posts&rdquo;</a> &mdash;
            you'll stay in the group and the conversation, this only stops these emails.
        </p>
    </div>
    """
    return send_notification(subject, body, to_email)


def notify_new_registration(name: str, email: str, household: str):
    """Notify admin when a new user registers."""
    subject = f"New Polly Connect Registration: {name}"
    body = f"""
    <div style="font-family: sans-serif; max-width: 500px;">
        <h2 style="color: #059669;">New Registration</h2>
        <table style="border-collapse: collapse; width: 100%;">
            <tr><td style="padding: 8px; font-weight: bold;">Name</td><td style="padding: 8px;">{name}</td></tr>
            <tr><td style="padding: 8px; font-weight: bold;">Email</td><td style="padding: 8px;">{email}</td></tr>
            <tr><td style="padding: 8px; font-weight: bold;">Household</td><td style="padding: 8px;">{household}</td></tr>
        </table>
        <p style="color: #666; font-size: 12px; margin-top: 20px;">— Polly Connect</p>
    </div>
    """
    return send_notification(subject, body)


def send_family_invitation(inviter_name: str, invitee_name: str, invitee_email: str,
                            family_code: str, invitation_id: int,
                            has_voice_message: bool = False,
                            base_url: str = "https://polly-connect.com"):
    """Send a family invitation email with the family code and link."""
    invite_url = f"{base_url}/web/invite-signup?invite={invitation_id}"

    voice_hook = ""
    if has_voice_message:
        voice_hook = f"""
        <div style="background: #f0fdf4; border: 2px solid #86efac; border-radius: 12px; padding: 20px; text-align: center; margin: 20px 0;">
            <p style="font-size: 18px; color: #166534; margin: 0 0 8px 0;">&#x1F3A4; {inviter_name} recorded a message for you</p>
            <p style="font-size: 13px; color: #15803d; margin: 0;">Click below to listen</p>
        </div>
        """
    else:
        voice_hook = f"""
        <div style="background: #f0fdf4; border: 2px solid #86efac; border-radius: 12px; padding: 20px; text-align: center; margin: 20px 0;">
            <p style="font-size: 18px; color: #166534; margin: 0;">{inviter_name} wants to share something with you</p>
        </div>
        """

    subject = f"{inviter_name} invited you to Polly Connect"
    body = f"""
    <div style="font-family: sans-serif; max-width: 500px; margin: 0 auto;">
        <div style="text-align: center; padding: 20px 0;">
            <span style="font-size: 48px;">&#x1F99C;</span>
            <h1 style="color: #059669; font-size: 24px; margin: 10px 0 5px 0;">Polly Connect</h1>
        </div>

        <h2 style="color: #1f2937; font-size: 20px; text-align: center;">
            Hi {invitee_name}!
        </h2>

        {voice_hook}

        <p style="color: #374151; font-size: 15px; line-height: 1.6; text-align: center;">
            Polly Connect is where families capture and share stories, messages, and memories
            across generations &mdash; through a friendly parrot-shaped device that listens,
            remembers, and connects.
        </p>

        <div style="text-align: center; margin: 25px 0;">
            <a href="{invite_url}"
               style="display: inline-block; background: #059669; color: white; font-size: 18px;
                      font-weight: bold; padding: 14px 32px; border-radius: 8px;
                      text-decoration: none;">
                Listen &amp; Get Started
            </a>
        </div>

        <div style="background: #f9fafb; border: 1px solid #e5e7eb; border-radius: 8px;
                    padding: 16px; text-align: center; margin: 20px 0;">
            <p style="color: #6b7280; font-size: 12px; margin: 0 0 4px 0;">Your access code</p>
            <p style="font-size: 28px; font-weight: bold; font-family: monospace;
                      letter-spacing: 6px; color: #059669; margin: 0;">
                {family_code}
            </p>
            <p style="color: #9ca3af; font-size: 11px; margin: 8px 0 0 0;">
                Or enter this code at polly-connect.com/web/family
            </p>
        </div>

        <p style="color: #9ca3af; font-size: 11px; text-align: center; margin-top: 30px;">
            Polly Connect &mdash; Your Life, Your Voice, Your Growth
        </p>
    </div>
    """
    return send_notification(subject, body, to_email=invitee_email)


def send_chatter_invitation(inviter_name: str, invitee_name: str, invitee_email: str,
                            invitation_id: int,
                            base_url: str = "https://polly-connect.com",
                            group_name: str = None):
    """Friend/Chatter invite. Creates a SEPARATE free account for the invitee and
    connects them via Chatter + the shared Wall ONLY — never hands out a household
    access code, so the invitee can't see the inviter's private stories/photos/
    family/legacy. Warm, legacy-selling copy. If group_name is given, the invite
    names the specific group they're being added to."""
    invite_url = f"{base_url}/web/invite-signup?invite={invitation_id}"
    from markupsafe import escape
    # Plain-text subject: strip CR/LF (header-injection safe).
    s_inviter = (inviter_name or "").replace("\n", " ").replace("\r", " ")
    s_group = (group_name or "").replace("\n", " ").replace("\r", " ")
    subject = (f"{s_inviter} invited you to {s_group} on Polly" if group_name
               else f"{s_inviter} invited you to chat on Polly")
    # HTML body: escape all user-controlled values.
    inviter_name = str(escape(inviter_name or ""))
    invitee_name = str(escape(invitee_name or ""))
    e_group = str(escape(group_name)) if group_name else None
    place = f"&ldquo;{e_group}&rdquo;" if e_group else "Chatter"
    join_label = f"Join {e_group}" if e_group else f"Join {inviter_name} on Chatter"
    body = f"""
    <div style="font-family: sans-serif; max-width: 500px; margin: 0 auto;">
        <div style="text-align: center; padding: 20px 0;">
            <span style="font-size: 48px;">&#x1F99C;</span>
            <h1 style="color: #d97706; font-size: 24px; margin: 10px 0 5px 0;">Polly Connect</h1>
        </div>

        <h2 style="color: #1f2937; font-size: 20px; text-align: center;">
            Hi {invitee_name}!
        </h2>

        <p style="color: #374151; font-size: 15px; line-height: 1.6; text-align: center;">
            <strong>{inviter_name}</strong> invited you to <strong>{place}</strong> on Polly &mdash;
            a simple, private place to talk, share, and reminisce together.
        </p>

        <p style="color: #374151; font-size: 15px; line-height: 1.6; text-align: center;">
            Here's the beautiful part: Polly listens for the moments that matter &mdash;
            the memories, the stories, the inside jokes &mdash; and gently gathers them into a
            living <strong>legacy book</strong> for the people you love.
            {inviter_name} thinks you're an important part of theirs.
        </p>

        <div style="text-align: center; margin: 28px 0;">
            <a href="{invite_url}"
               style="display: inline-block; background: #ea580c; color: white; font-size: 18px;
                      font-weight: bold; padding: 14px 32px; border-radius: 8px;
                      text-decoration: none;">
                {join_label}
            </a>
        </div>

        <p style="color: #6b7280; font-size: 13px; line-height: 1.6; text-align: center;">
            It's free to chat. And when you're ready, your free account lets you start
            saving <em>your</em> family's stories too.
        </p>

        <p style="color: #9ca3af; font-size: 11px; text-align: center; margin-top: 30px;">
            Polly Connect &mdash; turning everyday conversations into a family legacy
        </p>
    </div>
    """
    return send_notification(subject, body, to_email=invitee_email)


def send_chatter_connect_request(inviter_name: str, invitee_name: str, invitee_email: str,
                                 base_url: str = "https://polly-connect.com"):
    """Heads-up email for someone who ALREADY has a Polly account: a friend wants
    to connect on Chatter. They accept the pending request inside their own app —
    no signup, no access code, keeps their account separate."""
    login_url = f"{base_url}/web/login"
    subject = f"{inviter_name} wants to connect with you on Polly"
    body = f"""
    <div style="font-family: sans-serif; max-width: 500px; margin: 0 auto;">
        <div style="text-align: center; padding: 20px 0;">
            <span style="font-size: 48px;">&#x1F99C;</span>
            <h1 style="color: #d97706; font-size: 24px; margin: 10px 0 5px 0;">Polly Connect</h1>
        </div>
        <h2 style="color: #1f2937; font-size: 20px; text-align: center;">Hi {invitee_name}!</h2>
        <p style="color: #374151; font-size: 15px; line-height: 1.6; text-align: center;">
            <strong>{inviter_name}</strong> wants to connect with you on <strong>Chatter</strong>.
            You already have a Polly account &mdash; just open Polly and accept the request
            to start chatting and sharing memories together.
        </p>
        <div style="text-align: center; margin: 28px 0;">
            <a href="{login_url}"
               style="display: inline-block; background: #ea580c; color: white; font-size: 18px;
                      font-weight: bold; padding: 14px 32px; border-radius: 8px;
                      text-decoration: none;">
                Open Polly &amp; Accept
            </a>
        </div>
        <p style="color: #9ca3af; font-size: 11px; text-align: center; margin-top: 30px;">
            Polly Connect &mdash; turning everyday conversations into a family legacy
        </p>
    </div>
    """
    return send_notification(subject, body, to_email=invitee_email)
