Glen-collab/polly-connect/server/core/squawk.py

"""
Parrot squawk / ambient sound system for Polly Connect.

Clock-based scheduling: squawks and chatter fire on wall-clock intervals,
surviving WebSocket reconnects without resetting timers.

Short squawks: play at regular intervals (default every 10 min) with jitter.
Long chatter: play at longer intervals (default every 45 min) with jitter.
Post-response squawks: 50% chance after TTS, with delay to avoid mic feedback.
"""

import asyncio
import base64
import io
import logging
import os
import random
import time
import wave
from datetime import datetime
from typing import Dict, List, Optional

import numpy as np

logger = logging.getLogger(__name__)

# Default intervals (can be overridden per-device via settings)
DEFAULT_SQUAWK_MINUTES = 10
DEFAULT_CHATTER_MINUTES = 45

# Chance of squawk after a TTS response (disabled — causes ESP32 crash)
POST_RESPONSE_SQUAWK_CHANCE = 0.0  # disabled

# Volume reduction (0.0 = silent, 1.0 = full)
SQUAWK_VOLUME = 0.30  # 30% volume so mic doesn't pick it up

# Jitter range (seconds) added to scheduled times so sounds feel natural
JITTER_SECONDS = 120  # ±2 minutes

# Delay before first squawk after reconnect (seconds)
RECONNECT_GRACE = 60


def _convert_to_16k_mono(wav_bytes: bytes, volume: float = SQUAWK_VOLUME) -> bytes:
    """Convert any WAV to 16kHz mono 16-bit WAV with volume adjustment."""
    with wave.open(io.BytesIO(wav_bytes), 'rb') as w:
        channels = w.getnchannels()
        sampwidth = w.getsampwidth()
        framerate = w.getframerate()
        raw = w.readframes(w.getnframes())

    # Convert to numpy
    if sampwidth == 2:
        samples = np.frombuffer(raw, dtype=np.int16).astype(np.float32)
    elif sampwidth == 1:
        samples = (np.frombuffer(raw, dtype=np.uint8).astype(np.float32) - 128) * 256
    elif sampwidth == 4:
        samples = (np.frombuffer(raw, dtype=np.int32).astype(np.float32) / 65536)
    else:
        logger.warning(f"Unsupported sample width: {sampwidth}")
        return wav_bytes

    # Stereo to mono
    if channels == 2:
        samples = (samples[0::2] + samples[1::2]) / 2

    # Resample if not 16kHz
    if framerate != 16000:
        num_out = int(len(samples) * 16000 / framerate)
        indices = np.linspace(0, len(samples) - 1, num_out)
        samples = np.interp(indices, np.arange(len(samples)), samples)

    # Apply volume reduction
    samples = samples * volume

    # Back to int16
    samples = np.clip(samples, -32768, 32767).astype(np.int16)

    # Wrap in WAV
    out = io.BytesIO()
    with wave.open(out, 'wb') as w:
        w.setnchannels(1)
        w.setsampwidth(2)
        w.setframerate(16000)
        w.writeframes(samples.tobytes())
    return out.getvalue()


def _convert_to_16k_mono_from_pcm(wav_bytes: bytes, volume: float) -> bytes:
    """Apply volume to an already-converted 16kHz mono WAV."""
    with wave.open(io.BytesIO(wav_bytes), 'rb') as w:
        raw = w.readframes(w.getnframes())
    samples = np.frombuffer(raw, dtype=np.int16).astype(np.float32)
    samples = samples * volume
    samples = np.clip(samples, -32768, 32767).astype(np.int16)
    out = io.BytesIO()
    with wave.open(out, 'wb') as w:
        w.setnchannels(1)
        w.setsampwidth(2)
        w.setframerate(16000)
        w.writeframes(samples.tobytes())
    return out.getvalue()


class SquawkManager:
    def __init__(self, sounds_dir: str, db=None):
        self._db = db
        self.squawks: List[bytes] = []       # short squawk WAVs (16kHz mono, default volume)
        self.chatter: List[bytes] = []       # long chatter WAVs (16kHz mono, default volume)
        self.ambient: List[bytes] = []       # ambient bird clips (for button mode only)
        self._raw_squawks: List[bytes] = []  # raw WAVs at full volume (for per-device volume)
        self._raw_chatter: List[bytes] = []  # raw WAVs at full volume (for per-device volume)
        self._raw_ambient: List[bytes] = []  # raw ambient WAVs at full volume
        self._active_devices: Dict[str, asyncio.WebSocketServerProtocol] = {}
        self._playing: Dict[str, bool] = {}  # True if currently sending squawk/chatter
        self._busy: Dict[str, bool] = {}     # True if device is recording/processing/playing TTS
        self._send_locks: Dict[str, asyncio.Lock] = {}  # prevent concurrent WS writes
        self._snoozed_until: Dict[str, Optional[float]] = {}  # epoch time when snooze ends
        self._quiet_override: Dict[str, bool] = {}  # True = ignore quiet hours until they end
        self._quiet_hours: Dict[str, tuple] = {}  # per-device (start_hour, end_hour)
        self._message_callbacks: Dict[str, Any] = {}  # device_id -> async fn() -> bool (has messages)
        self._tts_callbacks: Dict[str, Any] = {}  # device_id -> async fn(text) -> None
        self._last_message_nag: Dict[str, float] = {}  # device_id -> last nag time
        self._message_nag_enabled: Dict[str, bool] = {}  # per-device message nag toggle
        self.last_squawk_end: Dict[str, float] = {}  # monotonic time when last squawk/chatter finished
        self._volume: Dict[str, float] = {}  # per-device volume (0.0-1.0)
        self._ambient_tasks: Dict[str, asyncio.Task] = {}  # device_id -> ambient mode task
        self._ambient_active: Dict[str, bool] = {}  # device_id -> True if ambient playing

        # Clock-based scheduling: wall-clock epoch timestamps
        self._next_squawk_time: Dict[str, float] = {}  # next squawk epoch
        self._next_chatter_time: Dict[str, float] = {}  # next chatter epoch
        self._squawk_interval: Dict[str, int] = {}   # per-device squawk interval (minutes)
        self._chatter_interval: Dict[str, int] = {}  # per-device chatter interval (minutes)

        # Nostalgia callbacks: device_id -> async callable
        self._nostalgia_callbacks: Dict[str, callable] = {}

        # Single scheduler task per device (polling loop)
        self._scheduler_tasks: Dict[str, asyncio.Task] = {}

        self._load_sounds(sounds_dir)

    def _load_sounds(self, sounds_dir: str):
        """Load and convert all squawk/chatter WAV files."""
        if not os.path.isdir(sounds_dir):
            logger.warning(f"Sounds directory not found: {sounds_dir}")
            return

        for fname in sorted(os.listdir(sounds_dir)):
            if not fname.endswith('.wav'):
                continue
            path = os.path.join(sounds_dir, fname)
            try:
                with open(path, 'rb') as f:
                    raw_bytes = f.read()
                converted = _convert_to_16k_mono(raw_bytes)
                raw_full = _convert_to_16k_mono(raw_bytes, volume=1.0)
                if fname.startswith('ambient'):
                    self.ambient.append(converted)
                    self._raw_ambient.append(raw_full)
                    logger.info(f"Loaded ambient sound: {fname}")
                elif fname.startswith('chatter'):
                    self.chatter.append(converted)
                    self._raw_chatter.append(raw_full)
                    logger.info(f"Loaded chatter sound: {fname}")
                elif fname.startswith('squawk'):
                    self.squawks.append(converted)
                    self._raw_squawks.append(raw_full)
                    logger.info(f"Loaded squawk sound: {fname}")
            except Exception as e:
                logger.error(f"Failed to load sound {fname}: {e}")

        logger.info(f"SquawkManager ready: {len(self.squawks)} squawks, {len(self.chatter)} chatter, {len(self.ambient)} ambient")

    def _schedule_next_squawk(self, device_id: str, min_delay: float = 0):
        """Set the next squawk time based on interval + jitter. 0 = disabled."""
        interval_min = self._squawk_interval.get(device_id, DEFAULT_SQUAWK_MINUTES)
        if interval_min == 0:
            self._next_squawk_time[device_id] = float('inf')  # never fires
            return
        interval = interval_min * 60
        jitter = random.uniform(-JITTER_SECONDS, JITTER_SECONDS)
        delay = max(min_delay, interval + jitter)
        self._next_squawk_time[device_id] = time.time() + delay
        logger.debug(f"Next squawk for {device_id} in {delay:.0f}s")

    def _schedule_next_chatter(self, device_id: str, min_delay: float = 0):
        """Set the next chatter time based on interval + jitter. 0 = disabled."""
        interval_min = self._chatter_interval.get(device_id, DEFAULT_CHATTER_MINUTES)
        if interval_min == 0:
            self._next_chatter_time[device_id] = float('inf')  # never fires
            return
        interval = interval_min * 60
        jitter = random.uniform(-JITTER_SECONDS, JITTER_SECONDS)
        delay = max(min_delay, interval + jitter)
        self._next_chatter_time[device_id] = time.time() + delay
        logger.debug(f"Next chatter for {device_id} in {delay:.0f}s")

    def register_device(self, device_id: str, websocket,
                        squawk_interval: int = None, chatter_interval: int = None,
                        quiet_hours_start: int = 21, quiet_hours_end: int = 7,
                        squawk_volume: int = 30, message_nag_enabled: int = 1):
        """Register or re-register a connected device. Preserves existing schedules."""
        # Always update the websocket reference
        self._active_devices[device_id] = websocket
        self._playing[device_id] = False
        self._send_locks[device_id] = asyncio.Lock()
        self._quiet_hours[device_id] = (quiet_hours_start, quiet_hours_end)
        self._volume[device_id] = max(0, min(100, squawk_volume)) / 100.0
        self._message_nag_enabled[device_id] = bool(message_nag_enabled)

        # Update intervals
        self._squawk_interval[device_id] = squawk_interval if squawk_interval is not None else DEFAULT_SQUAWK_MINUTES
        self._chatter_interval[device_id] = chatter_interval if chatter_interval is not None else DEFAULT_CHATTER_MINUTES

        # Only schedule if no existing schedule (don't reset on reconnect!)
        now = time.time()
        if device_id not in self._next_squawk_time or self._next_squawk_time[device_id] < now:
            # Either first time or schedule already passed — schedule with grace period
            self._schedule_next_squawk(device_id, min_delay=RECONNECT_GRACE)

        if device_id not in self._next_chatter_time or self._next_chatter_time[device_id] < now:
            self._schedule_next_chatter(device_id, min_delay=RECONNECT_GRACE * 3)

        # Start scheduler loop if not already running
        existing_task = self._scheduler_tasks.get(device_id)
        if not existing_task or existing_task.done():
            task = asyncio.ensure_future(self._scheduler_loop(device_id))
            self._scheduler_tasks[device_id] = task

        logger.info(
            f"Squawk registered {device_id}: "
            f"squawk every {self._squawk_interval[device_id]}min, "
            f"chatter every {self._chatter_interval[device_id]}min, "
            f"next squawk in {self._next_squawk_time[device_id] - now:.0f}s, "
            f"next chatter in {self._next_chatter_time[device_id] - now:.0f}s"
        )

    def register_nostalgia_callback(self, device_id: str, callback):
        """Register an async callback for nostalgia TTS during chatter slots."""
        self._nostalgia_callbacks[device_id] = callback

    def unregister_nostalgia_callback(self, device_id: str):
        self._nostalgia_callbacks.pop(device_id, None)

    def register_prayer_callback(self, device_id: str, callback):
        """Register an async callback for scheduled prayer playback."""
        if not hasattr(self, '_prayer_callbacks'):
            self._prayer_callbacks = {}
        self._prayer_callbacks[device_id] = callback

    def unregister_prayer_callback(self, device_id: str):
        if hasattr(self, '_prayer_callbacks'):
            self._prayer_callbacks.pop(device_id, None)

    def register_message_callback(self, device_id: str, has_messages_cb, tts_cb):
        """Register callbacks for message nagging.
        has_messages_cb: async fn() -> bool (True if unread messages exist)
        tts_cb: async fn(text) -> None (sends TTS to device)
        """
        self._message_callbacks[device_id] = has_messages_cb
        self._tts_callbacks[device_id] = tts_cb

    def unregister_device(self, device_id: str):
        """Mark device as disconnected. Does NOT cancel schedules."""
        self._active_devices.pop(device_id, None)
        self._playing.pop(device_id, None)
        self._nostalgia_callbacks.pop(device_id, None)
        self._message_callbacks.pop(device_id, None)
        self._tts_callbacks.pop(device_id, None)
        # Keep send lock, schedules, intervals, quiet hours — they survive reconnects
        # The scheduler loop will idle while device is not in _active_devices

    def snooze(self, device_id: str, minutes: int):
        """Snooze all squawks/chatter for N minutes."""
        self._snoozed_until[device_id] = time.time() + minutes * 60
        self._quiet_override.pop(device_id, None)  # cancel any wake override
        logger.info(f"Squawks snoozed for {minutes}min → {device_id}")

    def unsnooze(self, device_id: str):
        """Cancel snooze and resume squawks immediately (overrides quiet hours too)."""
        self._snoozed_until.pop(device_id, None)
        self._quiet_override[device_id] = True
        logger.info(f"Squawks unsnoozed (quiet hours overridden) → {device_id}")

    def is_snoozed(self, device_id: str) -> bool:
        until = self._snoozed_until.get(device_id)
        if until and time.time() < until:
            return True
        return self._in_quiet_hours(device_id)

    def snooze_status(self, device_id: str) -> str:
        """Return snooze reason: 'snoozed', 'quiet_hours', or 'awake'."""
        until = self._snoozed_until.get(device_id)
        if until and time.time() < until:
            remaining = int((until - time.time()) / 60)
            return f"snoozed:{remaining}"
        if self._in_quiet_hours(device_id):
            return "quiet_hours"
        return "awake"

    def _in_quiet_hours(self, device_id: str) -> bool:
        """Check if current time is within quiet hours (no squawks at night)."""
        from config import settings as app_settings
        try:
            from zoneinfo import ZoneInfo
            tz = ZoneInfo(app_settings.TIMEZONE)
        except Exception:
            try:
                import pytz
                tz = pytz.timezone(app_settings.TIMEZONE)
            except Exception:
                from datetime import timezone
                tz = timezone.utc
        now_hour = datetime.now(tz).hour
        start, end = self._quiet_hours.get(device_id, (21, 7))
        if start > end:
            in_quiet = now_hour >= start or now_hour < end
        elif start < end:
            in_quiet = start <= now_hour < end
        else:
            in_quiet = False

        # Handle quiet hours override from "Wake Up Polly"
        if self._quiet_override.get(device_id):
            if in_quiet:
                return False  # Override active, still in quiet hours — stay awake
            else:
                # Quiet hours ended naturally — clear override in memory and DB
                self._quiet_override.pop(device_id, None)
                logger.info(f"Quiet override auto-cleared (quiet hours ended) → {device_id}")
                try:
                    if self._db:
                        conn = self._db._get_connection()
                        conn.execute("UPDATE devices SET dev_quiet_override = 0 WHERE device_id = ?", (device_id,))
                        conn.commit()
                        if not self._db._conn:
                            conn.close()
                except Exception as e:
                    logger.warning(f"Failed to clear DB quiet override: {e}")

        return in_quiet

    def update_intervals(self, device_id: str, squawk_interval: int = None,
                         chatter_interval: int = None,
                         quiet_hours_start: int = None, quiet_hours_end: int = None,
                         squawk_volume: int = None):
        """Update intervals for a device (from web settings)."""
        if squawk_interval is not None:
            self._squawk_interval[device_id] = squawk_interval
        if chatter_interval is not None:
            self._chatter_interval[device_id] = chatter_interval
        if quiet_hours_start is not None and quiet_hours_end is not None:
            self._quiet_hours[device_id] = (quiet_hours_start, quiet_hours_end)
        if squawk_volume is not None:
            self._volume[device_id] = max(0, min(100, squawk_volume)) / 100.0
        # Reschedule with new intervals
        self._schedule_next_squawk(device_id, min_delay=30)
        self._schedule_next_chatter(device_id, min_delay=60)

    def get_send_lock(self, device_id: str) -> Optional[asyncio.Lock]:
        """Get the websocket send lock for a device (used by _send_tts too)."""
        return self._send_locks.get(device_id)

    def stop_playback(self, device_id: str):
        """Interrupt any currently playing squawk/chatter."""
        self._playing[device_id] = False

    def is_playing(self, device_id: str) -> bool:
        return self._playing.get(device_id, False)

    def set_busy(self, device_id: str, busy: bool):
        """Mark device as busy (recording, processing, or playing TTS). Suppresses squawks."""
        self._busy[device_id] = busy

    def is_busy(self, device_id: str) -> bool:
        return self._busy.get(device_id, False)

    def reset_idle_timer(self, device_id: str):
        """Push back the next squawk after user activity (so it doesn't squawk mid-conversation)."""
        grace = self._squawk_interval.get(device_id, DEFAULT_SQUAWK_MINUTES) * 60
        next_time = time.time() + grace
        # Only push forward, never pull back
        if next_time > self._next_squawk_time.get(device_id, 0):
            self._next_squawk_time[device_id] = next_time

    # ── Scheduler loop ──────────────────────────────────────────────

    async def _scheduler_loop(self, device_id: str):
        """Single polling loop per device. Checks wall-clock schedules every 15s."""
        logger.info(f"Scheduler loop started → {device_id}")
        try:
            while True:
                await asyncio.sleep(15)  # Check every 15 seconds

                # If device not connected, just idle
                ws = self._active_devices.get(device_id)
                if not ws:
                    continue

                # Skip during quiet hours or snooze
                if self.is_snoozed(device_id):
                    continue

                # Skip if device is busy (recording, processing, or playing TTS)
                if self.is_busy(device_id):
                    continue

                now = time.time()

                # Check scheduled prayer recordings first
                prayer_cb = getattr(self, '_prayer_callbacks', {}).get(device_id)
                if prayer_cb:
                    try:
                        played = await prayer_cb()
                        if played:
                            continue  # Prayer played — skip squawk/chatter this cycle
                    except Exception as e:
                        logger.error(f"Prayer callback error: {e}")

                # Check for pending messages — nag every 15 min (if enabled for this device)
                msg_cb = self._message_callbacks.get(device_id)
                tts_cb = self._tts_callbacks.get(device_id)
                if msg_cb and tts_cb and self._message_nag_enabled.get(device_id, True):
                    last_nag = self._last_message_nag.get(device_id, 0)
                    if now - last_nag >= 900:  # 15 minutes
                        try:
                            has_msgs = await msg_cb()
                            if has_msgs:
                                self._last_message_nag[device_id] = now
                                # Squawk first, then say "Message!"
                                if self.squawks:
                                    await self.send_squawk(device_id)
                                    await asyncio.sleep(1.0)
                                await tts_cb("Message! Message!")
                                logger.info(f"Message nag → {device_id}")
                                continue  # Skip regular squawk/chatter this cycle
                        except Exception as e:
                            logger.error(f"Message nag error: {e}")

                # Check squawk schedule
                next_sq = self._next_squawk_time.get(device_id, 0)
                if now >= next_sq and self.squawks:
                    await self.send_squawk(device_id)
                    self._schedule_next_squawk(device_id)

                # Check chatter schedule (20% chance to play nostalgia snippet instead)
                next_ch = self._next_chatter_time.get(device_id, 0)
                if now >= next_ch and self.chatter:
                    nostalgia_cb = self._nostalgia_callbacks.get(device_id)
                    if nostalgia_cb and random.random() < 0.20:
                        try:
                            await nostalgia_cb()
                        except Exception as e:
                            logger.error(f"Nostalgia callback error: {e}")
                            await self.send_chatter(device_id)
                    else:
                        await self.send_chatter(device_id)
                    self._schedule_next_chatter(device_id)

        except asyncio.CancelledError:
            logger.info(f"Scheduler loop cancelled → {device_id}")
        except Exception as e:
            logger.error(f"Scheduler loop error for {device_id}: {e}")

    # ── Sound sending ───────────────────────────────────────────────

    def _pick_sound(self, device_id: str, raw_list: List[bytes], default_list: List[bytes]) -> bytes:
        """Pick a random sound with per-device volume applied."""
        vol = self._volume.get(device_id, SQUAWK_VOLUME)
        idx = random.randrange(len(raw_list))
        # If volume matches default, use pre-converted version
        if abs(vol - SQUAWK_VOLUME) < 0.01:
            return default_list[idx]
        return _convert_to_16k_mono_from_pcm(raw_list[idx], vol)

    async def send_squawk(self, device_id: str):
        """Send a random short squawk to a device."""
        if not self.squawks:
            return
        ws = self._active_devices.get(device_id)
        if not ws:
            return
        squawk = self._pick_sound(device_id, self._raw_squawks, self.squawks)
        logger.info(f"Squawk! → {device_id} (vol {self._volume.get(device_id, SQUAWK_VOLUME):.0%})")
        await self._send_wav(ws, device_id, squawk)

    async def send_chatter(self, device_id: str):
        """Send a random long chatter clip (interruptible)."""
        if not self.chatter:
            return
        ws = self._active_devices.get(device_id)
        if not ws:
            return
        chatter = self._pick_sound(device_id, self._raw_chatter, self.chatter)
        logger.info(f"Chatter starting → {device_id} (vol {self._volume.get(device_id, SQUAWK_VOLUME):.0%})")
        await self._send_wav(ws, device_id, chatter, interruptible=True)

    async def maybe_post_response_squawk(self, device_id: str, tts_duration: float = 0.0):
        """50% chance of a short squawk after a TTS response."""
        if not self.squawks or self.is_snoozed(device_id):
            return
        if self._squawk_interval.get(device_id, DEFAULT_SQUAWK_MINUTES) == 0:
            return  # squawks disabled
        if random.random() < POST_RESPONSE_SQUAWK_CHANCE:
            # Wait for TTS to finish playing on ESP32, plus buffer for speaker→mic fade
            wait = max(3.5, tts_duration + 2.0) + random.uniform(0.5, 2.0)
            await asyncio.sleep(wait)
            # Re-check busy/snoozed after waiting (user may have started talking)
            if self.is_busy(device_id) or self.is_snoozed(device_id):
                return
            await self.send_squawk(device_id)

    # ── Ambient bird sounds mode ──────────────────────────────────────

    def is_ambient(self, device_id: str) -> bool:
        return self._ambient_active.get(device_id, False)

    async def start_ambient(self, device_id: str, duration_minutes: int = 10):
        """Start ambient bird sounds — plays chatter clips back to back for N minutes."""
        # Stop any existing ambient session
        await self.stop_ambient(device_id)

        self._ambient_active[device_id] = True
        self.set_busy(device_id, True)  # suppress normal squawks/commands during ambient

        async def _ambient_loop():
            try:
                end_time = time.time() + duration_minutes * 60
                clip_count = 0
                logger.info(f"Ambient mode started → {device_id} ({duration_minutes} min)")
                while time.time() < end_time and self._ambient_active.get(device_id):
                    ws = self._active_devices.get(device_id)
                    if not ws:
                        break
                    # Pick a random ambient clip (fall back to chatter if no ambient)
                    raw_pool = self._raw_ambient if self._raw_ambient else self._raw_chatter
                    default_pool = self.ambient if self.ambient else self.chatter
                    if raw_pool:
                        clip = self._pick_sound(device_id, raw_pool, default_pool)
                        await self._send_wav(ws, device_id, clip, interruptible=False)
                        clip_count += 1
                    # Short pause between clips (2-5 seconds)
                    pause = random.uniform(2.0, 5.0)
                    await asyncio.sleep(pause)
                logger.info(f"Ambient mode ended → {device_id} ({clip_count} clips played)")
            except asyncio.CancelledError:
                logger.info(f"Ambient mode cancelled → {device_id}")
            except Exception as e:
                logger.error(f"Ambient mode error → {device_id}: {e}")
            finally:
                self._ambient_active[device_id] = False
                self.set_busy(device_id, False)

        task = asyncio.ensure_future(_ambient_loop())
        self._ambient_tasks[device_id] = task

    async def stop_ambient(self, device_id: str):
        """Stop ambient bird sounds and return to normal listening."""
        self._ambient_active[device_id] = False
        task = self._ambient_tasks.pop(device_id, None)
        if task and not task.done():
            task.cancel()
            try:
                await task
            except asyncio.CancelledError:
                pass
        self.set_busy(device_id, False)
        self.stop_playback(device_id)
        logger.info(f"Ambient mode stopped → {device_id}")

    async def send_wake_squawk(self, device_id: str):
        """Short squawk on wake word detection."""
        if not self.squawks:
            return
        ws = self._active_devices.get(device_id)
        if not ws:
            return
        squawk = self._pick_sound(device_id, self._raw_squawks, self.squawks)
        logger.info(f"Wake squawk → {device_id}")
        await self._send_wav(ws, device_id, squawk)

    async def _send_wav(self, ws, device_id: str, wav_data: bytes, interruptible: bool = False):
        """Send WAV data as chunked base64 audio_chunk events."""
        lock = self._send_locks.get(device_id)
        if not lock:
            return

        async with lock:
            self._playing[device_id] = True
            try:
                # Notify ESP32 that ambient sound is starting
                await ws.send_json({"event": "squawk_start"})

                # Adaptive chunking: pace sends based on audio length
                # to avoid overwhelming ESP32's TCP/WebSocket buffer
                total_len = len(wav_data)
                if total_len > 128000:  # >4s — voice messages, long clips
                    chunk_size = 4000
                    chunk_delay = 0.08
                elif total_len > 64000:  # >2s — medium clips
                    chunk_size = 6000
                    chunk_delay = 0.06
                else:  # short squawk clips
                    chunk_size = 8000
                    chunk_delay = 0.05

                for i in range(0, total_len, chunk_size):
                    if not self._playing.get(device_id, False):
                        logger.info(f"Squawk/chatter interrupted → {device_id}")
                        break
                    chunk = wav_data[i:i + chunk_size]
                    chunk_b64 = base64.b64encode(chunk).decode()
                    await ws.send_json({
                        "event": "audio_chunk",
                        "audio": chunk_b64,
                        "final": (i + chunk_size >= total_len),
                        "squawk": True,
                    })
                    await asyncio.sleep(chunk_delay)

                await ws.send_json({"event": "squawk_end"})
            except Exception as e:
                logger.error(f"Squawk send error: {e}")
            finally:
                self._playing[device_id] = False
                self.last_squawk_end[device_id] = time.monotonic()
