Glen-collab/polly-connect/server/core/intent_parser.py

"""
Intent Parser for Polly Connect
"""

import re
from typing import Dict, Optional


class IntentParser:
    def __init__(self, use_spacy: bool = False):
        self.use_spacy = False  # Disabled for simplicity
        self._family_names = set()  # populated from family tree
        self._relation_to_name = {}  # "wife" → "Ali", populated from family tree

        # Family storytelling intents
        self._introduce_self_phrases = [
            "this is ", "my name is ", "i'm ",
        ]
        self._tell_story_phrases = [
            "let me tell you about", "i remember when", "i want to tell you",
            "let me share", "i have a story",
            "i want to share", "record my story", "take my story",
            "story time", "i want to record", "i have something to share",
            "i want to tell a story", "let me tell you something",
            "can i tell you something", "i got a story",
            "i have a memory to share", "can i share a story",
        ]
        self._hear_stories_phrases = [
            "tell me about", "play back",
            "what stories", "any stories about", "any stories",
            "read me a story", "play a story", "do you have any stories",
            "what have you heard about", "play my stories", "read my stories",
            "what did grandma say", "what did she say", "what did he say",
            "what has grandma said", "what has she said",
            "read me my stories", "tell me one of my stories",
            "read a story", "tell me my story", "share a story",
            "read back my stories", "read me one of my stories",
            "narrate a story", "story reading",
            "tell me a story", "say a story", "give me a story",
            "got any stories", "hear a story", "let's hear a story",
            "i want to hear a story", "i'd like to hear a story",
            "let me hear a story", "can you tell me a story",
            "do you have a story",
        ]
        self._family_question_phrases = [
            "ask me about my family", "family question", "ask me a family question",
            "family story", "ask me something about my life",
            "ask me about my life", "tell me about my family",
            "ask me a question about my life",
            "i want to answer questions", "interview me",
            "let's do a family question", "give me a question",
            "ask me about my past", "ask me about growing up",
        ]
        self._story_progress_phrases = [
            "how many stories", "my progress", "how are we doing",
            "story progress", "how many memories", "show my progress",
            "what have we captured", "book progress",
            "how's the book coming", "how's my book",
            "how far along are we", "how many have we done",
        ]

        self.container_words = {
            "drawer", "bin", "box", "shelf", "cabinet", "toolbox", "container",
            "bucket", "tray", "rack", "pegboard", "wall", "corner", "workbench",
            "bench", "table", "floor", "hook", "hanger", "bag", "case"
        }

        # Trigger phrases for non-memory intents (from polly-config)
        self._tell_kid_joke_phrases = [
            "tell me a kid joke", "tell me a kids joke", "kid joke",
            "tell me a potty joke", "potty joke", "tell me a poop joke",
            "poop joke", "fart joke", "tell me a fart joke",
            "tell me a silly joke", "silly joke",
            "tell me a funny kid joke", "tell me a gross joke",
            "tell me a unicorn joke", "unicorn joke",
            "tell me a dinosaur joke", "dinosaur joke",
            "tell the kids a joke", "joke for kids",
            "joke for the kids", "got a kid joke",
            "do you know any kid jokes", "say a funny joke for kids",
            "kids joke", "tell us a kid joke",
            "tell a kid joke", "got any kid jokes",
        ]
        self._tell_naughty_joke_phrases = [
            "tell me a naughty joke", "naughty joke", "dirty joke",
            "tell me a dirty joke", "adult joke", "tell me an adult joke",
            "spicy joke", "tell me a spicy joke", "risque joke",
            "tell me a risque joke", "cheeky joke", "tell me a cheeky joke",
            "tell me something naughty", "got any naughty jokes",
            "give me a naughty joke", "got a dirty joke",
            "tell me a grown up joke", "grown up joke",
        ]
        self._tell_joke_phrases = [
            "tell me a joke", "make me laugh", "say something funny",
            "i need a laugh", "cheer me up", "tell a joke",
            "got any jokes", "do you know any jokes", "know any jokes",
            "give me a joke", "hit me with a joke", "another joke",
            "tell me another joke", "tell me another one",
            "one more joke", "got another joke", "joke please",
            "can you tell me a joke", "do you have any jokes",
            "let's hear a joke", "how about a joke",
        ]
        self._ask_question_phrases = [
            "ask me a question", "let's talk",
            "got any questions for me", "what do you want to know",
            "i'm ready for a question", "go ahead and ask me",
            "let's do a question", "question time",
        ]
        self._repeat_phrases = [
            "repeat", "say that again", "what did you say", "what was that",
            "pardon", "come again", "one more time",
            "can you repeat that", "i didn't hear you", "i didn't catch that",
            "ask me again", "ask me that again", "ask that again",
            "what was the question", "what did you ask", "say it again",
            "can you ask me again", "ask that question again",
            "huh", "excuse me", "i missed that", "sorry what",
            "can you say that again", "repeat that please",
            "tell me again", "run that by me again",
        ]
        self._slower_phrases = [
            "slower", "slow down", "talk slower", "speak slower",
            "too fast", "not so fast", "can you slow down",
            "you're talking too fast", "that was too fast",
            "speak more slowly", "take it slow",
        ]
        self._thinking_phrases = [
            "i'm still thinking", "still thinking", "hang on",
            "let me think", "hold on", "hold your horses",
            "wait a minute", "give me a second", "give me a moment",
            "this is deep", "that's a good question", "good question",
            "let me see", "hmm", "um", "one second", "one moment",
            "i'm thinking", "thinking", "wait", "just a moment",
            "i need a minute", "hold that thought",
        ]
        self._skip_phrases = [
            "skip", "next question", "skip this one", "i don't know",
            "pass", "next one", "move on",
            "skip that", "i'll skip that one", "give me a different one",
            "try another one", "different question", "ask me something else",
            "i don't want to answer that", "i'd rather not",
            "never mind", "nevermind", "forget it",
        ]
        self._stop_phrases = [
            "stop", "that's enough", "i'm tired", "let's stop",
            "no more", "i'm done", "enough for today",
            "i'm finished", "we're done", "that's all",
            "that's it", "let's be done", "all done",
            "i'm all done", "no more questions",
            "that's all for now", "we can stop",
        ]
        self._goodbye_phrases = [
            "goodbye polly", "bye polly", "goodbye", "bye bye",
            "see you later", "good night", "goodnight",
            "goodnight polly", "nighty night", "see you tomorrow",
            "see ya", "bye", "later polly", "talk to you later",
            "i'm going to bed", "going to sleep",
            "i'm heading out", "heading out", "i'm leaving",
        ]
        self._greeting_phrases = [
            "hello polly", "hi polly", "hey polly", "good morning",
            "good afternoon", "good evening", "hello", "hi there",
            "good morning polly", "morning polly", "morning",
            "hey there", "howdy", "what's up polly",
            "how are you polly", "how are you doing",
        ]
        self._bible_phrases = [
            "read me a verse", "bible verse", "today's verse",
            "give me a verse", "read me today's verse",
            "verse about", "scripture", "read me a psalm", "read me a salm",
            "psalm", "salm", "read me a proverb", "proverb",
            "read me from the bible", "daily verse",
            "read me some scripture", "what does the bible say",
            "i need a bible verse", "give me some scripture",
            "read from the bible", "do you have a verse",
            "can you read me a verse", "what's today's verse",
            "inspirational verse", "devotional",
            "verse of the day", "daily bible verse",
        ]
        self._prayer_phrases = [
            # Direct prayer requests
            "say a prayer", "pray for me", "pray with me",
            "let's pray", "let us pray", "can you pray",
            "i need a prayer", "prayer", "pray",
            "say a prayer for me", "will you pray",
            "i want to pray", "help me pray",
            "lead me in prayer", "lead a prayer",
            "can we pray", "would you pray",
            "pray for us", "pray over me",
            # Time-based
            "bedtime prayer", "goodnight prayer",
            "nighttime prayer", "evening prayer",
            "morning prayer", "start the day with prayer",
            # Emotional triggers (natural speech)
            "i'm having a hard day", "i need some hope",
            "i'm feeling down", "i'm feeling low",
            "i'm worried", "i'm scared", "i'm anxious",
            "i feel alone", "i feel lonely",
            "i miss him", "i miss her", "i miss them",
            "i'm struggling", "things are tough",
            "give me strength", "i need strength",
            "i need peace", "i need comfort",
            "i'm thankful", "i'm grateful", "i'm blessed",
            "thank the lord", "praise god", "praise the lord",
            "bless this day", "bless my family",
            # Family-specific
            "pray for my family", "family prayer",
            "pray for my kids", "pray for the children",
            "pray for my grandchildren", "pray for my grandkids",
        ]
        self._nostalgia_phrases = [
            "tell me something from the old days", "take me back",
            "the good old days", "nostalgia",
            "what was it like back then",
            "reminisce", "let's reminisce", "remember the old days",
            "tell me something from my childhood",
            "back in my day",
            "what was it like growing up",
            "memory lane", "take me down memory lane",
            "tell me something nostalgic",
            "the old days", "back in the day",
        ]
        self._medication_phrases = [
            "remind me to take", "medication", "my pills",
            "what medications", "did i take my pills", "medicine",
            "med reminder", "what pills do i take", "my meds",
            "what are my meds", "when do i take my pills",
            "when is my next pill", "pill schedule",
            "did i take my meds", "have i taken my medicine",
            "i took my pills", "i took my meds", "meds taken",
            "i already took my medicine", "took my medication",
            "what medicine do i take",
        ]
        # Message board intents
        self._check_messages_phrases = [
            "any messages", "check messages", "do i have messages",
            "are there any messages", "messages for me", "check the board",
            "what's on the board", "message board", "what are my messages",
            "read my messages", "read me my messages", "do i have any messages",
            "what messages do i have", "any new messages", "read the messages",
            "what did i miss", "anything on the board",
        ]
        self._clear_messages_phrases = [
            "clear the board", "clear messages", "clear message",
            "clear the message board", "clear the messages",
            "delete messages", "delete message", "delete the messages",
            "erase the board", "wipe the board",
            "delete all messages", "clear all messages", "remove all messages",
            "get rid of the messages", "erase messages", "wipe messages",
            "clean the board", "empty the board",
        ]
        self._person_status_words = {
            "dad", "mom", "daddy", "mommy", "papa", "mama",
            "grandma", "grandpa", "brother", "sister",
            "nana", "nanny", "pops", "poppy", "granny",
            "auntie", "aunt", "uncle", "cousin",
            "hubby", "husband", "wife", "wifey",
        }

        self._weather_phrases = [
            "what's the weather", "what is the weather", "weather this week",
            "weather today", "the weather", "farmer's almanac", "forecast",
            "how's the weather", "what's it like outside",
            "is it going to rain", "what's the forecast",
            "what's the weather like", "weather report",
            "do i need an umbrella", "is it cold outside",
            "what's it going to be like this week",
            "what's the temperature", "temperature outside",
        ]

        self._time_phrases = [
            "what time is it", "what's the time", "what is the time",
            "do you have the time", "tell me the time", "current time",
            "what time do you have", "can you tell me the time",
            "you got the time", "what time you got",
        ]
        self._date_phrases = [
            "what day is it", "what's today's date", "what is today's date",
            "what's the date", "what is the date", "what day is today",
            "what is today", "what's today", "today's date",
            "what day of the week is it", "what month is it",
            "what year is it", "what's the date today",
            "can you tell me the date", "do you know what day it is",
        ]
        self._thank_you_phrases = [
            "thank you", "thanks polly", "thanks", "thank you polly",
            "appreciate it", "that was helpful", "you're the best",
            "thanks so much", "thank you so much",
            "that's very kind", "you're sweet", "you're so helpful",
            "i appreciate that", "thanks a lot", "thanks a bunch",
            "that was great", "perfect thank you", "awesome thanks",
            "great job polly", "good job polly", "nice one polly",
        ]
        self._who_is_phrases = [
            "who is", "who's",
        ]

    def parse(self, text: str) -> Dict:
        text = text.strip()
        if not text:
            return {"intent": "unknown", "confidence": 0.0}

        text_lower = text.lower()

        # Normalize contractions: "whats" → "what's", "im" → "i'm", "dont" → "don't"
        # so phrases match regardless of whether STT includes apostrophes
        contraction_map = {
            "whats ": "what's ", "thats ": "that's ", "hows ": "how's ",
            "todays ": "today's ", "lets ": "let's ", "dont ": "don't ",
            "didnt ": "didn't ", "doesnt ": "doesn't ", "cant ": "can't ",
            "wont ": "won't ", "isnt ": "isn't ", "youre ": "you're ",
        }
        for abbrev, full in contraction_map.items():
            text_lower = text_lower.replace(abbrev, full)
        # Word-boundary contractions that can match inside other words
        text_lower = re.sub(r'\bim ', "i'm ", text_lower)
        text_lower = re.sub(r'\bive ', "i've ", text_lower)

        # ── Family storytelling intents (check first, order matters) ──

        if self._matches(text_lower, self._story_progress_phrases):
            return {"intent": "story_progress", "confidence": 0.95}

        if self._matches(text_lower, self._family_question_phrases):
            return {"intent": "family_question", "confidence": 0.95}

        if self._matches(text_lower, self._hear_stories_phrases):
            # Extract who they want to hear about
            query = None
            # Longer "about" phrases first so they capture the full topic
            for phrase in [
                "tell me a story about", "say a story about",
                "give me a story about", "read me a story about",
                "share a story about", "hear a story about",
                "play a story about", "narrate a story about",
                "can you tell me a story about", "i want to hear a story about",
                "i'd like to hear a story about", "do you have a story about",
                "do you have any stories about", "got any stories about",
                "any stories about", "story about",
                "tell me about", "what have you heard about",
                "what did", "what has",
            ]:
                if phrase in text_lower:
                    idx = text_lower.index(phrase) + len(phrase)
                    query = text_lower[idx:].strip().rstrip("?. ")
                    if not query:
                        query = None
                    break
            return {"intent": "hear_stories", "query": query, "confidence": 0.9}

        if self._matches(text_lower, self._tell_story_phrases):
            return {"intent": "tell_story", "confidence": 0.95}

        intro = self._parse_introduction(text)
        if intro:
            return {"intent": "introduce_self", "name": intro[0],
                    "relationship": intro[1], "confidence": 0.9}

        # Check non-memory intents (they're simpler/faster)
        if self._matches(text_lower, self._tell_kid_joke_phrases):
            return {"intent": "tell_kid_joke", "confidence": 0.95}

        if self._matches(text_lower, self._tell_naughty_joke_phrases):
            return {"intent": "tell_naughty_joke", "confidence": 0.95}

        if self._matches(text_lower, self._tell_joke_phrases):
            return {"intent": "tell_joke", "confidence": 0.95}

        if self._matches(text_lower, self._ask_question_phrases):
            return {"intent": "ask_question", "confidence": 0.95}

        if self._matches(text_lower, self._repeat_phrases):
            return {"intent": "repeat", "confidence": 0.95}

        if self._matches(text_lower, self._slower_phrases):
            return {"intent": "slower", "confidence": 0.95}

        # ── Message board intents (before item queries) ──

        if self._matches(text_lower, self._check_messages_phrases):
            return {"intent": "check_messages", "confidence": 0.95}

        if self._matches(text_lower, self._clear_messages_phrases):
            return {"intent": "clear_messages", "confidence": 0.95}

        # "[person] is home/back" — clear their status
        home_match = re.search(r"(\w+) is (?:home|back|here)\b", text_lower)
        if home_match:
            person = home_match.group(1).strip()
            if person.lower() not in ("it", "this", "that", "there", "what", "who", "everyone"):
                return {"intent": "person_home", "person": person, "confidence": 0.9}

        # "Send a message to [person]'s Polly" — cross-tenant messaging (two-step)
        polly_msg_match = re.search(
            r"(?:send|leave) (?:a )?message (?:to |for )?(\w+(?:\s+\w+)?)'?s? polly",
            text_lower)
        if not polly_msg_match:
            polly_msg_match = re.search(
                r"message (\w+(?:\s+\w+)?)'?s? polly",
                text_lower)
        if polly_msg_match:
            person = polly_msg_match.group(1).strip()
            if person.lower() not in ("a", "the", "my", "our"):
                return {"intent": "send_polly_message", "person": person, "confidence": 0.95}

        leave_msg = self._is_leave_message(text_lower)
        if leave_msg:
            return {"intent": "leave_message", "person": leave_msg["person"],
                    "message": leave_msg["message"], "confidence": 0.9}

        person_query = self._is_person_query(text_lower, self._family_names)
        if person_query:
            return {"intent": "where_is_person", "person": person_query, "confidence": 0.9}

        status_update = self._is_status_update(text_lower)
        if status_update:
            return {"intent": "status_update", "person": status_update["person"],
                    "status": status_update["status"], "confidence": 0.85}

        # ── Content intents (before memory/item to avoid false matches) ──

        if self._matches(text_lower, self._bible_phrases):
            topic = None
            topic_match = re.search(r"verse about (.+)", text_lower)
            if topic_match:
                topic = topic_match.group(1).strip()
            elif "psalm" in text_lower or "salm" in text_lower:
                topic = "Psalm"
            elif "proverb" in text_lower:
                topic = "Proverb"
            return {"intent": "bible_verse", "topic": topic, "confidence": 0.9}

        # Check for blessing playback (recorded voice prayers) before AI prayers
        blessing_result = self._is_play_blessing(text_lower)
        if blessing_result:
            return blessing_result

        if self._matches(text_lower, self._prayer_phrases):
            theme = None
            pray_for = None  # specific person to pray for

            # Time-based
            if any(w in text_lower for w in ["bedtime", "goodnight", "nighttime", "evening", "sleep"]):
                theme = "rest"
            elif any(w in text_lower for w in ["morning", "start the day", "new day"]):
                theme = "strength"
            # Emotional categories
            elif any(w in text_lower for w in ["worried", "worry", "anxious", "anxiety", "scared", "fear", "nervous"]):
                theme = "anxiety"
            elif any(w in text_lower for w in ["miss him", "miss her", "miss them", "passed away", "lost", "grief", "heaven"]):
                theme = "grief"
            elif any(w in text_lower for w in ["alone", "lonely", "loneliness", "isolated", "by myself"]):
                theme = "loneliness"
            elif any(w in text_lower for w in ["hard day", "tough", "struggling", "difficult", "having a hard"]):
                theme = "strength"
            elif any(w in text_lower for w in ["heal", "healing", "sick", "health", "surgery", "doctor", "pain"]):
                theme = "healing"
            elif any(w in text_lower for w in ["forgive", "forgiveness", "let go", "bitter", "angry"]):
                theme = "forgiveness"
            elif any(w in text_lower for w in ["peace", "calm", "quiet", "still", "rest", "comfort", "grace", "mercy"]):
                theme = "peace"
            elif any(w in text_lower for w in ["hope", "hopeful", "hopeless", "feeling down", "feeling low", "down"]):
                theme = "hope"
            elif any(w in text_lower for w in ["strength", "strong", "courage", "brave", "resilience", "resilient", "perseverance", "endurance"]):
                theme = "strength"
            elif any(w in text_lower for w in ["faith", "believe", "trust", "doubt", "wisdom", "guidance", "guide"]):
                theme = "faith"
            elif any(w in text_lower for w in ["thank", "grateful", "blessing", "thankful", "blessed", "bless", "praise", "glory", "glorious"]):
                theme = "gratitude"
            elif any(w in text_lower for w in ["purpose", "meaning", "legacy", "why am i"]):
                theme = "purpose"
            elif any(w in text_lower for w in ["happy", "happiness", "joy", "celebrate", "celebration", "wonderful"]):
                theme = "joy"
            # Family
            elif any(w in text_lower for w in ["kid", "kids", "children", "grandkid", "grandchildren", "grandson", "granddaughter", "family"]):
                theme = "family"

            # Check for "pray for [person/topic]" pattern
            pray_for_match = re.search(r'pray(?:er)?\s+(?:for|over)\s+(?:my\s+)?(.+?)(?:\s+please)?$', text_lower)
            if pray_for_match:
                target = pray_for_match.group(1).strip()
                # Skip only truly generic self-references
                skip = {"me", "us", "the family", "my family", "the kids"}
                if target and target not in skip:
                    # Check if target matches a known family member
                    is_family = False
                    if self._family_names:
                        for fn in self._family_names:
                            if fn.lower() == target or fn.lower() in target:
                                is_family = True
                                pray_for = fn  # use proper casing from family tree
                                theme = None  # person prayer, not themed
                                break
                    if not is_family:
                        # Not a family member — still pass it through
                        # "world peace", "the troops", "grace", "healing" all work
                        pray_for = target

            return {"intent": "prayer", "theme": theme, "pray_for": pray_for, "confidence": 0.9}

        if self._matches(text_lower, self._nostalgia_phrases):
            return {"intent": "nostalgia", "confidence": 0.9}

        # Only match medication if it's not an item query ("where are my medicine balls")
        if self._matches(text_lower, self._medication_phrases):
            if not any(q in text_lower for q in ["where", "find", "lost", "can't find", "looking for"]):
                return {"intent": "medication", "confidence": 0.9, "raw": text}

        if self._matches(text_lower, self._weather_phrases):
            return {"intent": "weather", "confidence": 0.9}

        if self._matches(text_lower, self._time_phrases):
            return {"intent": "tell_time", "confidence": 0.95}

        if self._matches(text_lower, self._date_phrases):
            return {"intent": "tell_date", "confidence": 0.95}

        if self._matches(text_lower, self._thank_you_phrases):
            return {"intent": "thank_you", "confidence": 0.9}

        # "Who is [name]?" — extract the name
        who_match = re.search(r"(?:who(?:'s| is) )(.+?)(?:\?|$)", text_lower)
        if who_match:
            name = who_match.group(1).strip()
            if name and name not in ("this", "that", "it", "there", "here"):
                return {"intent": "who_is", "name": name, "confidence": 0.9}

        # ── Memory/item intents ──
        if self._is_help(text_lower):
            return {"intent": "help", "confidence": 1.0}

        if self._is_list(text_lower):
            return {"intent": "list_all", "confidence": 1.0}

        # "I found it" / "got it" / "never mind"
        if self._is_found_it(text_lower):
            return {"intent": "found_it", "confidence": 0.9}
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
